and3rson/deck65/circuits/anim/1.png

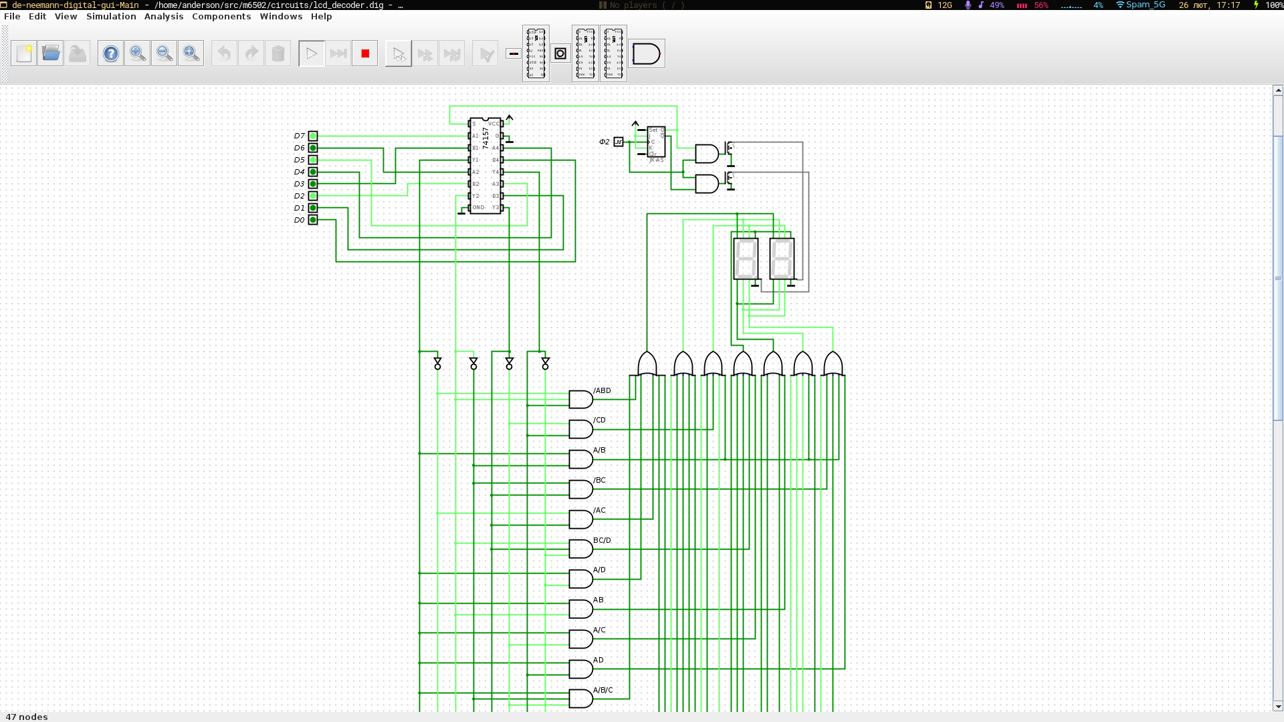
circuits/anim/1.png
