and3rson/deck65/circuits/anim/3.png

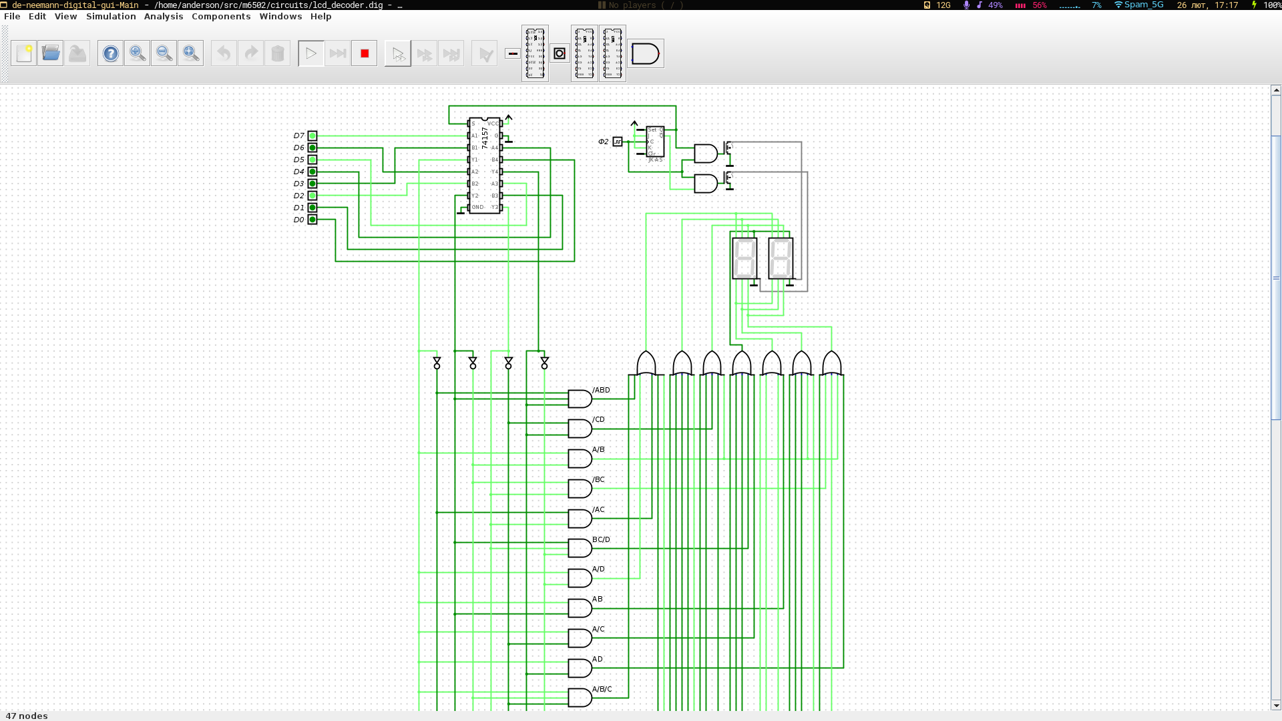
circuits/anim/3.png
