and3rson/deck65/circuits/anim/anim.gif

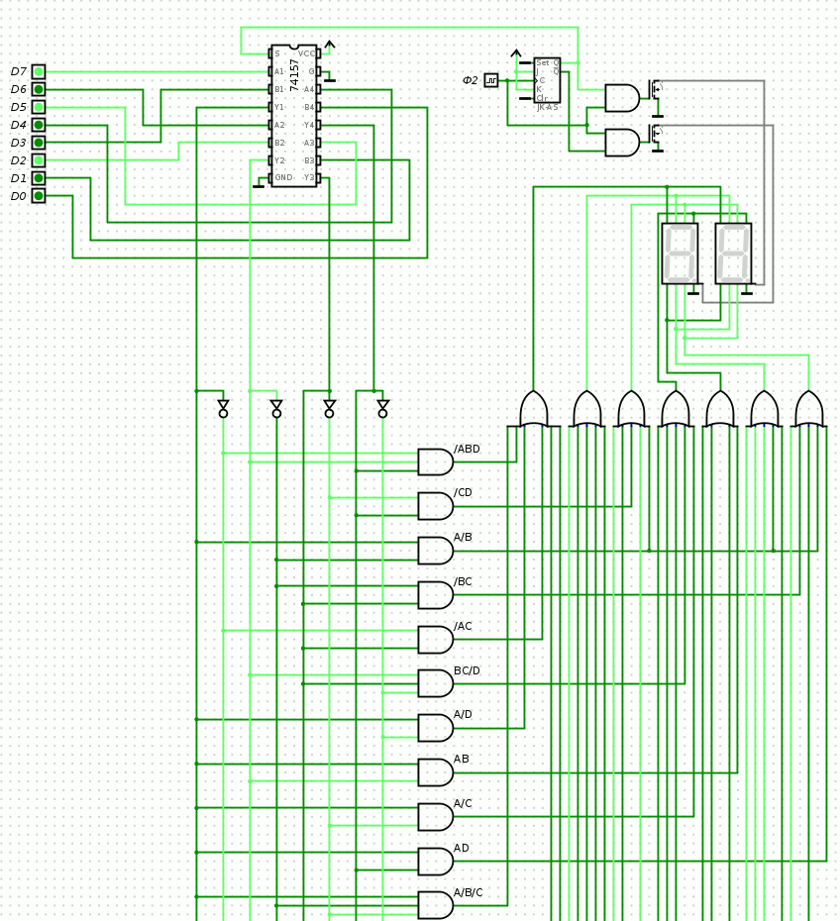
circuits/anim/anim.gif
