and3rson/deck65/circuits/sevenseg_decoder.png

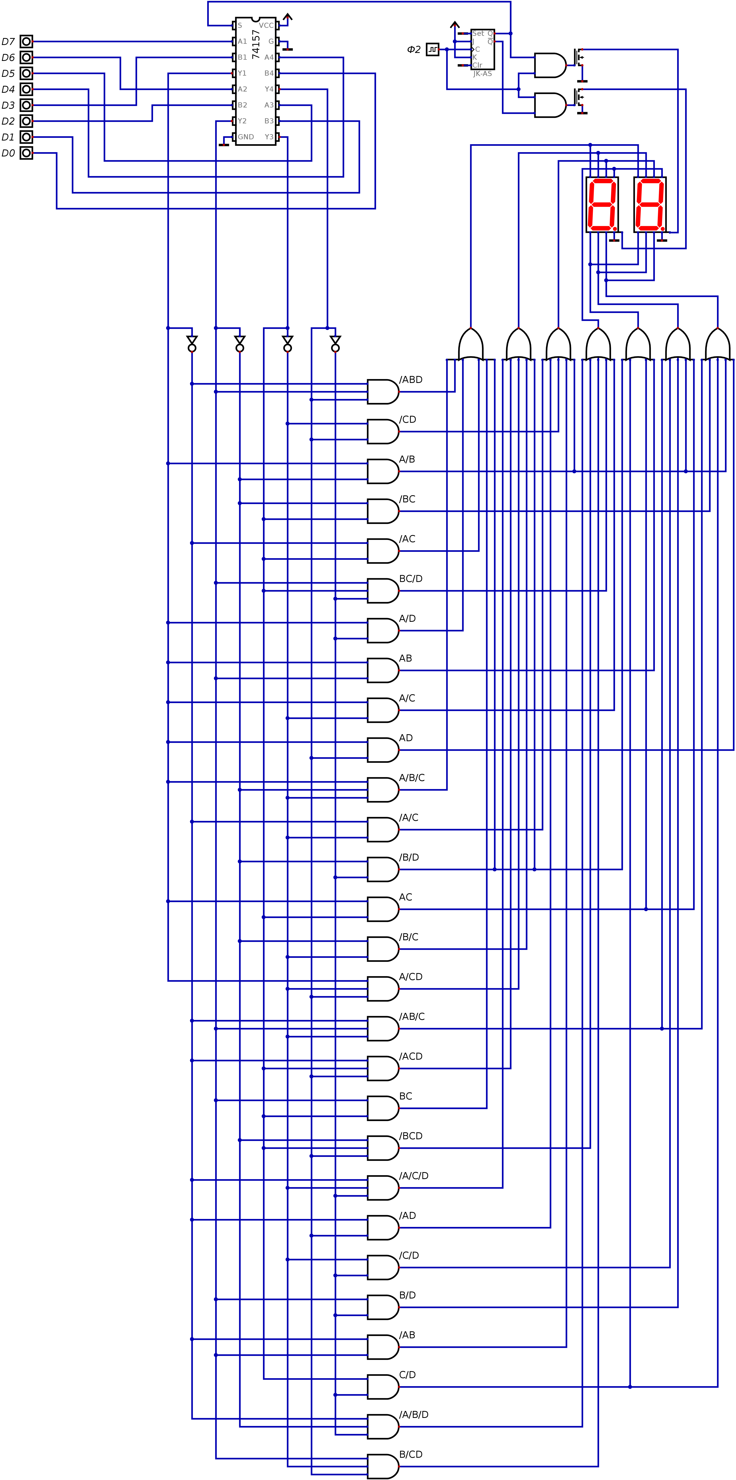
circuits/sevenseg_decoder.png
