and3rson/deck65/gal/img/1_big.png

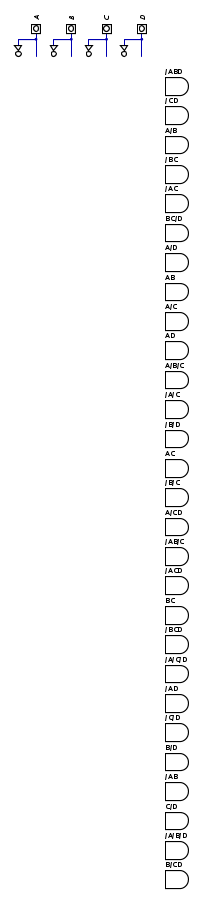
gal/img/1_big.png
