and3rson/deck65/gal/img/2_big.png

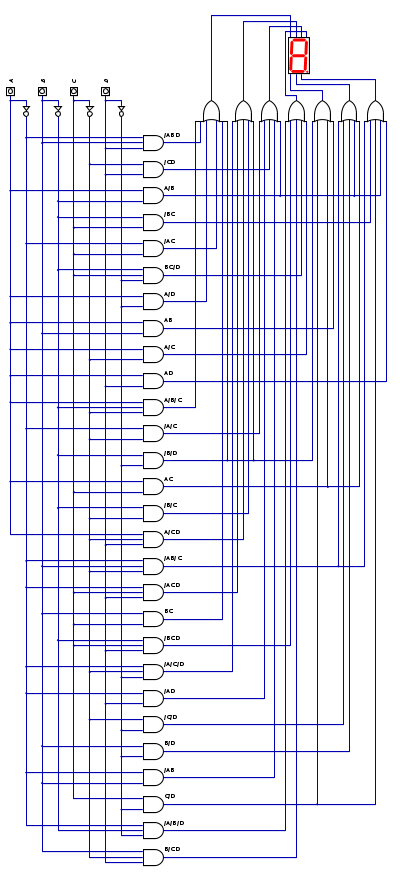
gal/img/2_big.png
