and3rson/deck65/gal/img/3_big.png

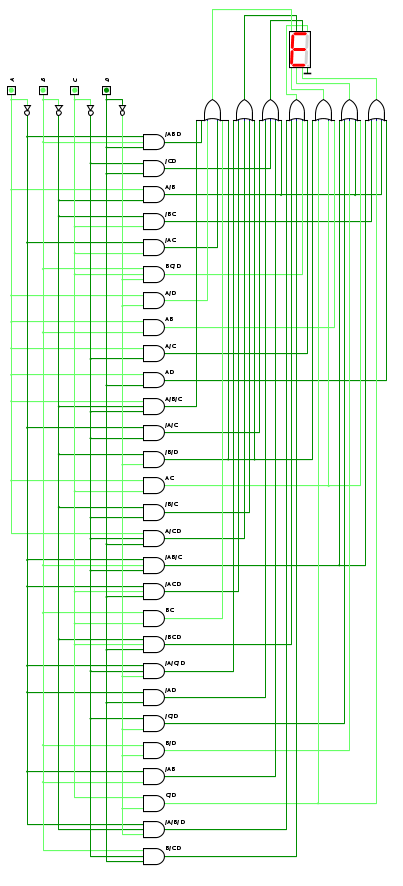
gal/img/3_big.png
