and3rson/deck65/img/24064.jpg

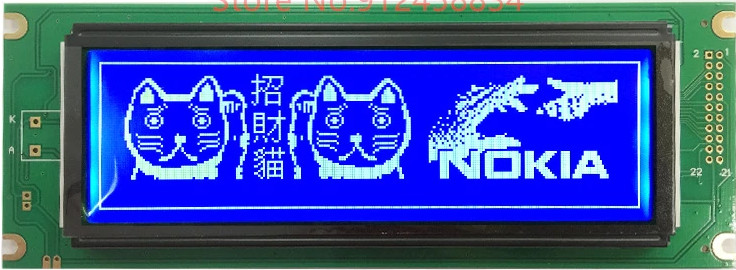
img/24064.jpg
