and3rson/deck65/img/24064_quirks.png

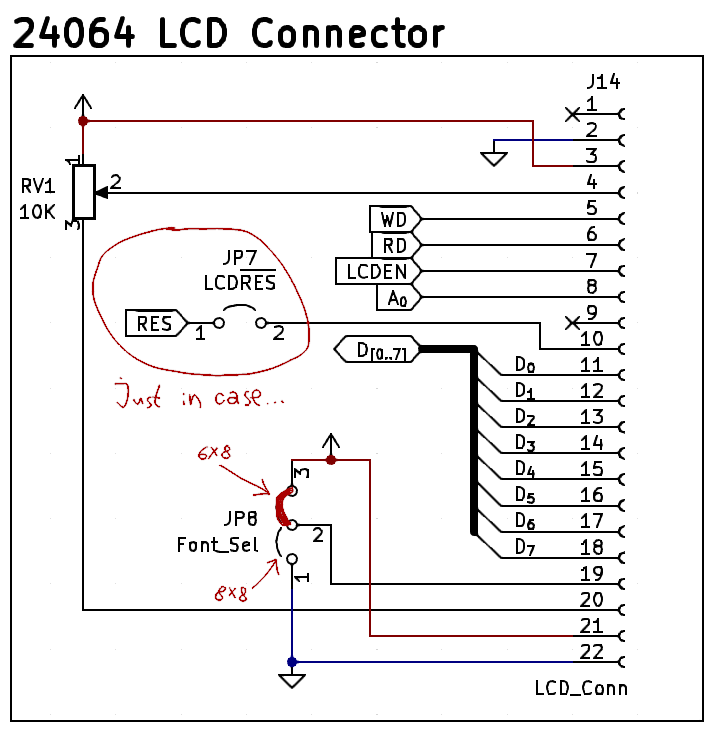
img/24064_quirks.png
