and3rson/deck65/img/cap_spread.png

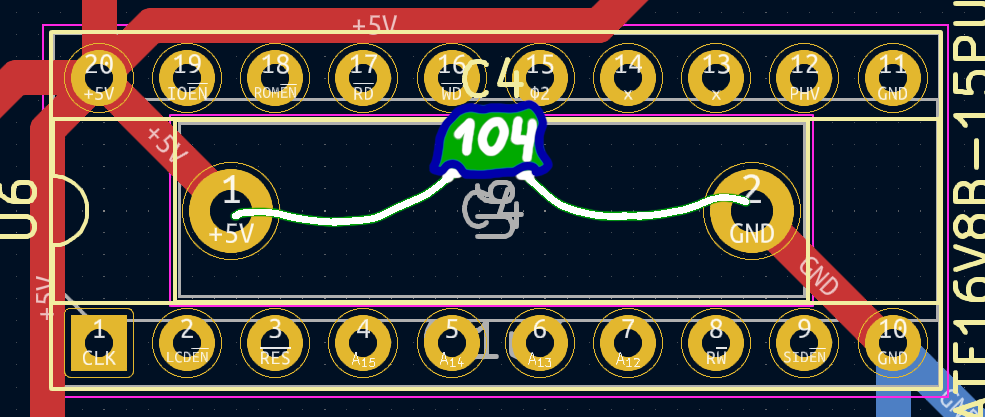
img/cap_spread.png
