and3rson/deck65/img/case_4_screws.jpg

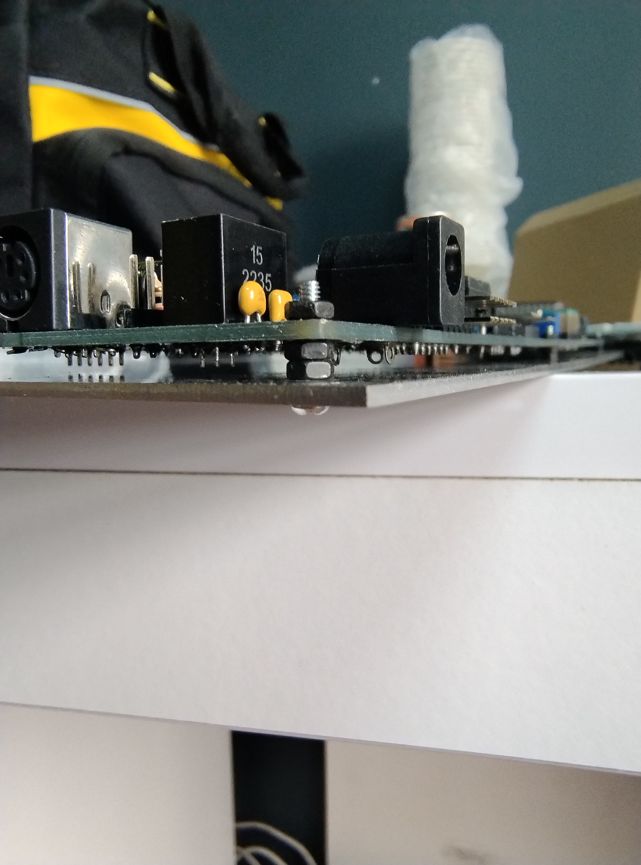
img/case_4_screws.jpg
