and3rson/deck65/img/case_8_clearance.jpg

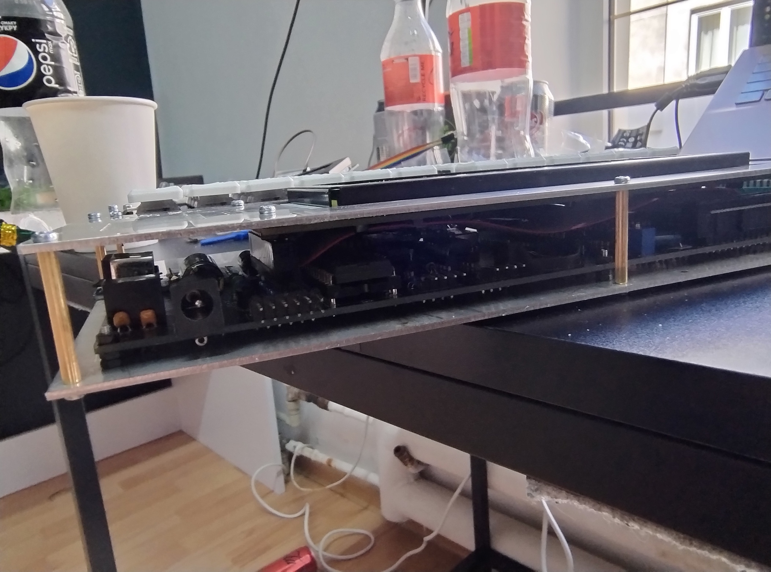
img/case_8_clearance.jpg
