and3rson/deck65/img/clock.png

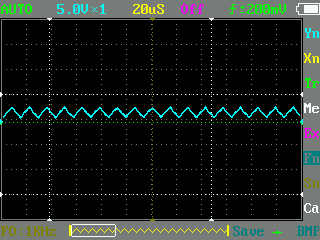
img/clock.png
