and3rson/deck65/img/composite_render_tv.jpg

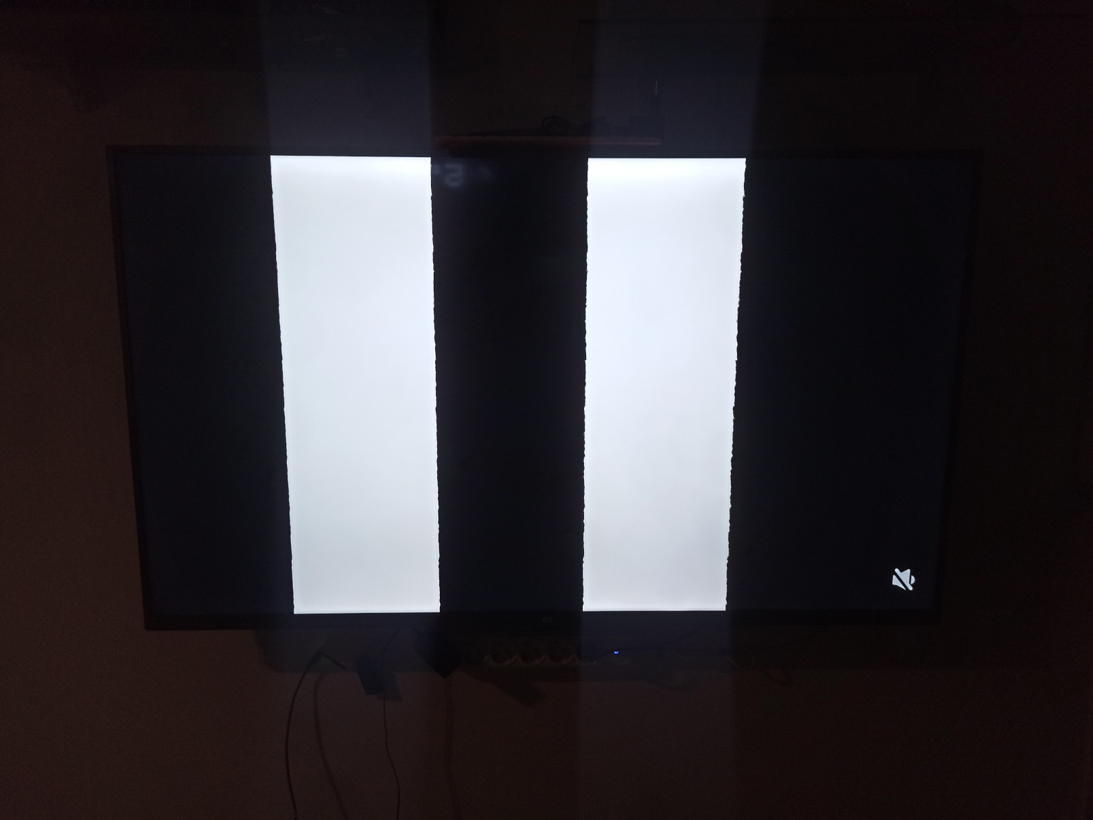
img/composite_render_tv.jpg
