and3rson/deck65/img/ds1813_reset.png

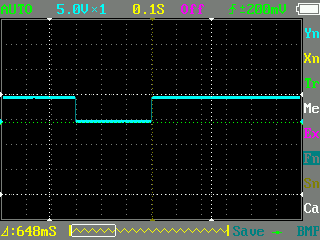
img/ds1813_reset.png
