and3rson/deck65/img/gal_slowbus_addr_rw.png

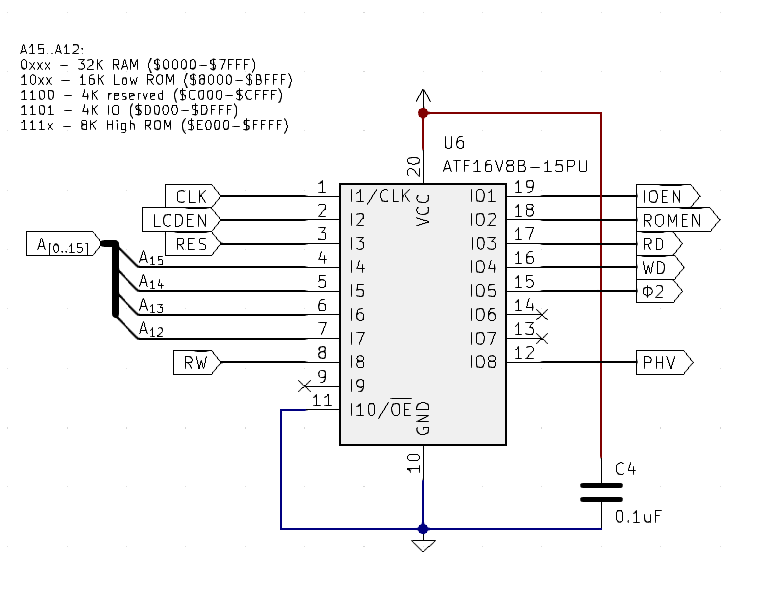
img/gal_slowbus_addr_rw.png
