and3rson/deck65/img/lcd_garbage.jpg

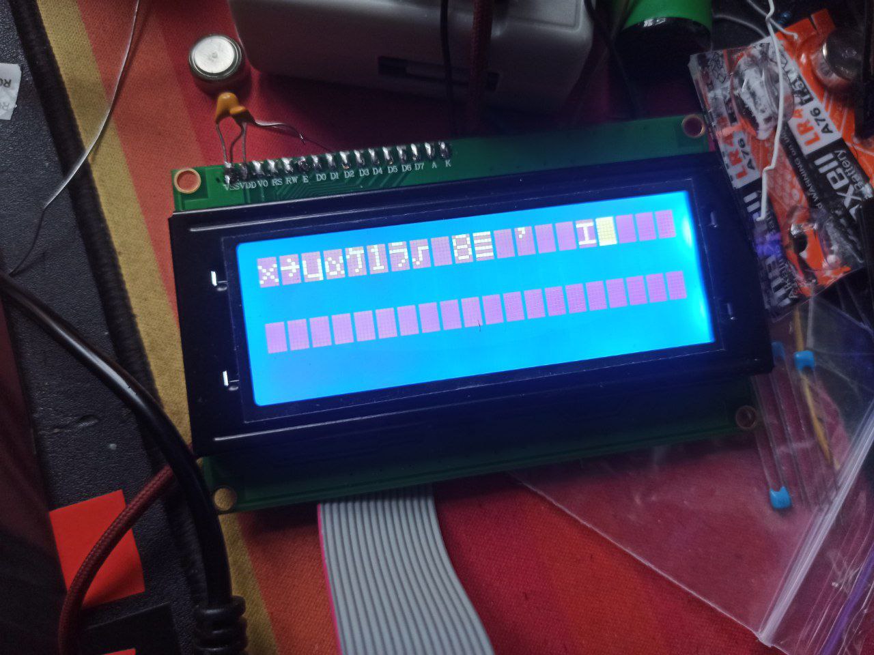
img/lcd_garbage.jpg
