and3rson/deck65/img/lcd_via_timing.png

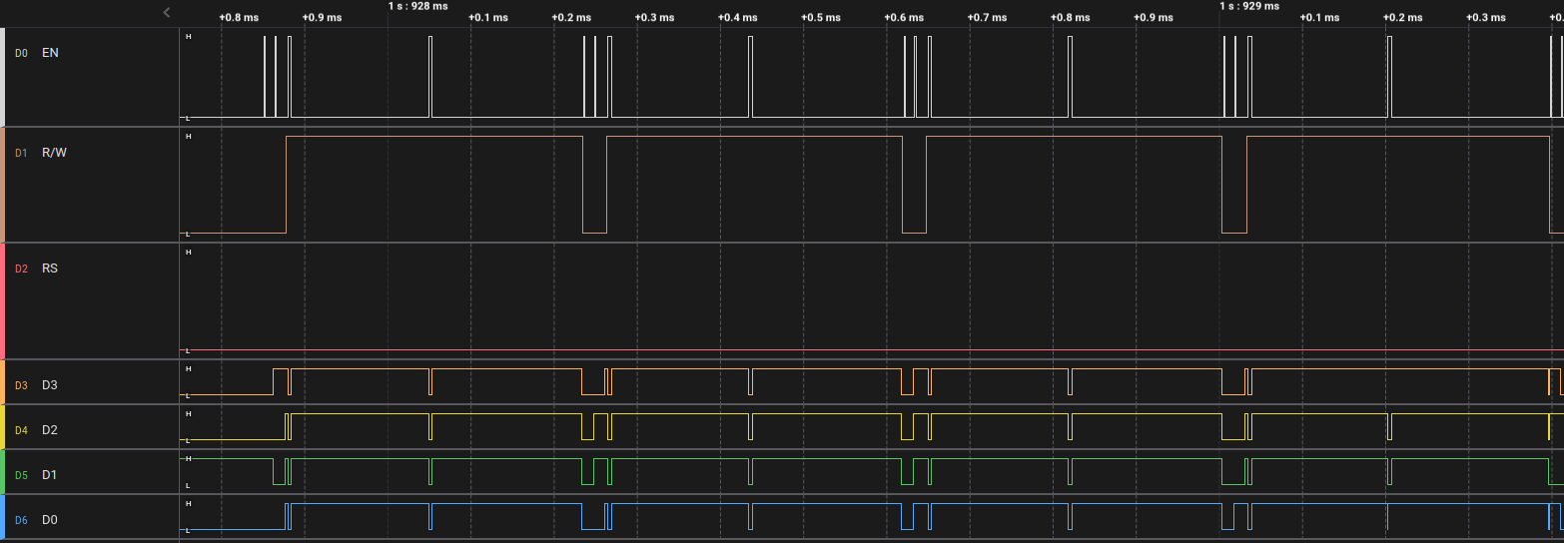
img/lcd_via_timing.png
