and3rson/deck65/img/lcd_weirdness.png

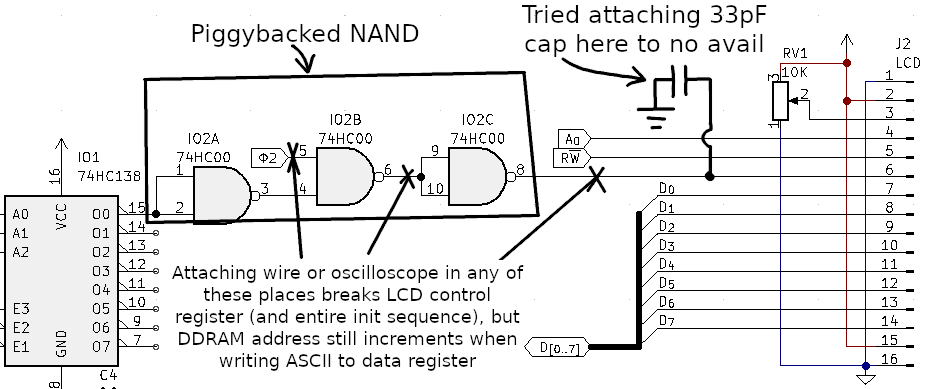
img/lcd_weirdness.png
