and3rson/deck65/img/lcden_timing2.png

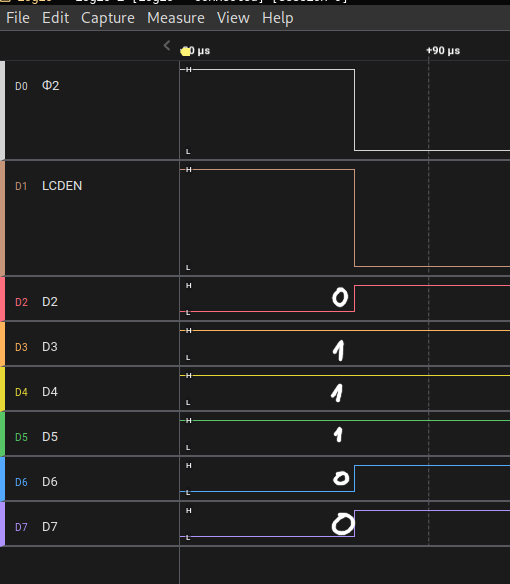
img/lcden_timing2.png
