and3rson/deck65/img/lcden_timing.png

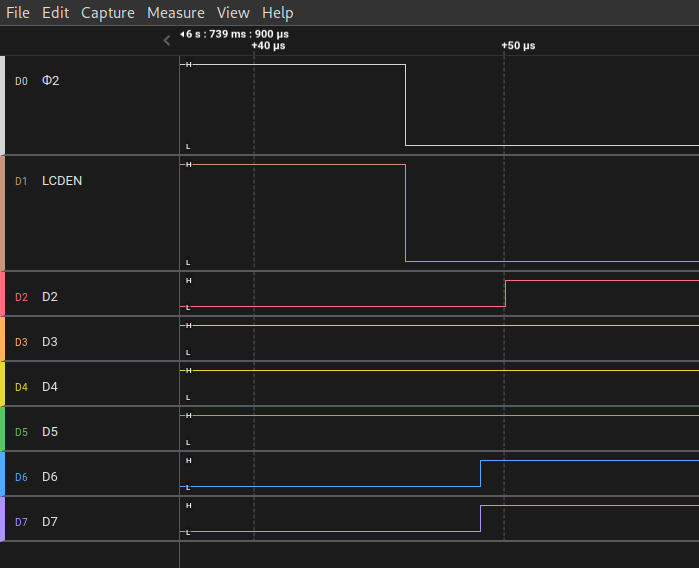
img/lcden_timing.png
