and3rson/deck65/img/mess2.jpg

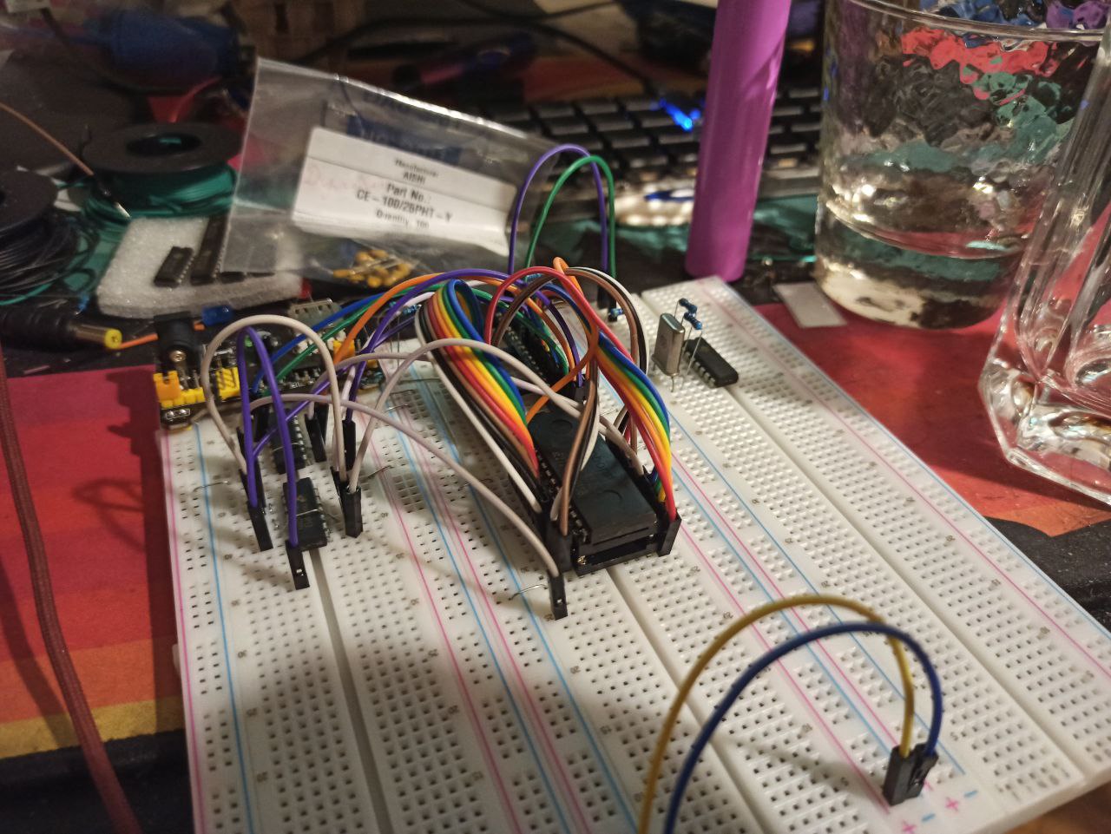
img/mess2.jpg
