and3rson/deck65/img/mess3.jpg

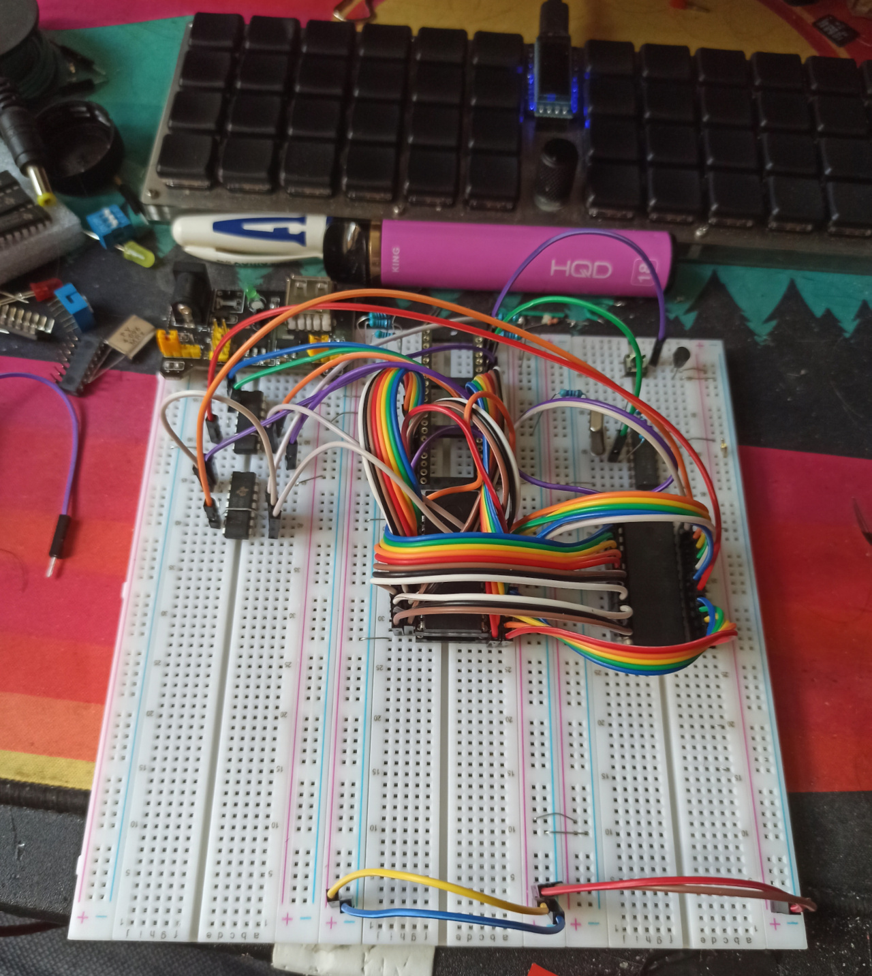
img/mess3.jpg
