and3rson/deck65/img/mess.jpg

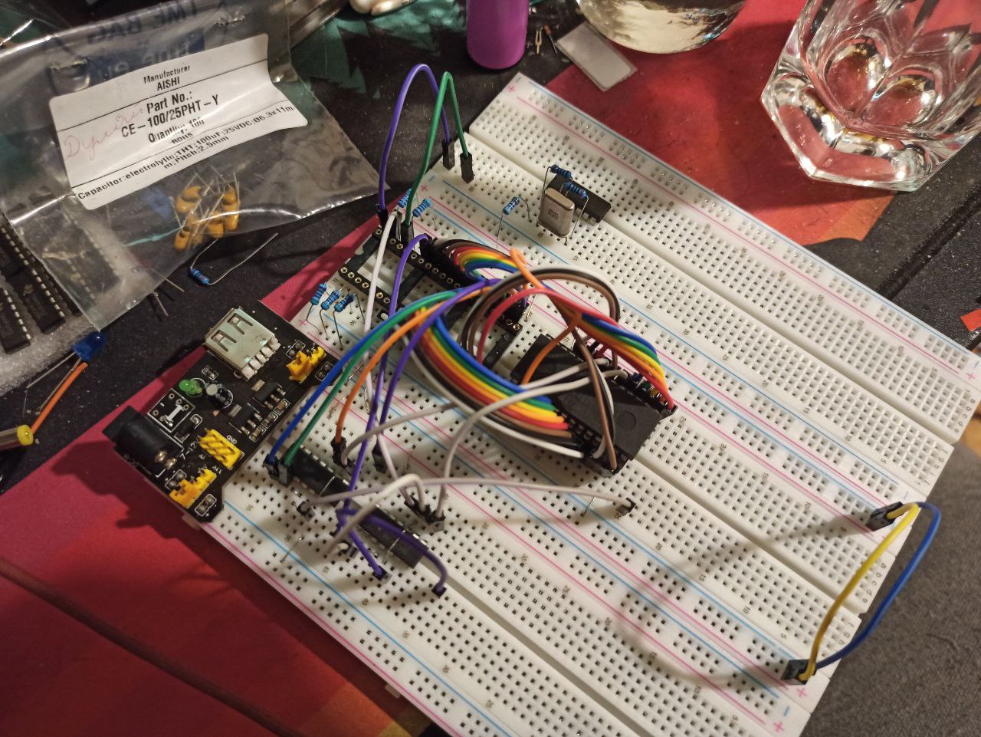
img/mess.jpg
