and3rson/deck65/img/nand_piggyback.jpg

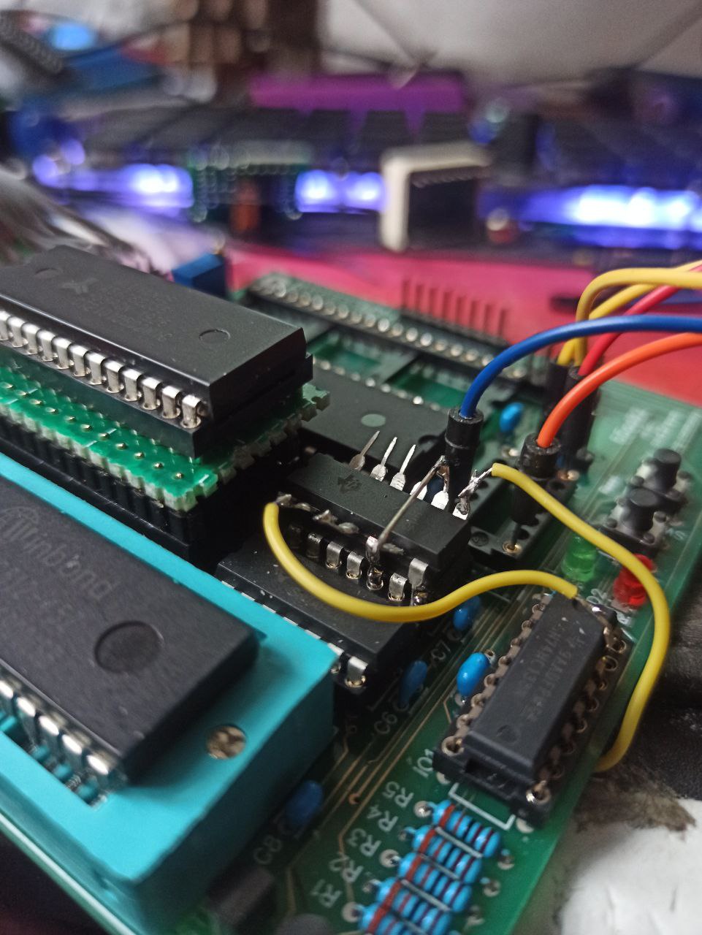
img/nand_piggyback.jpg
