and3rson/deck65/img/pal_weirdness.png

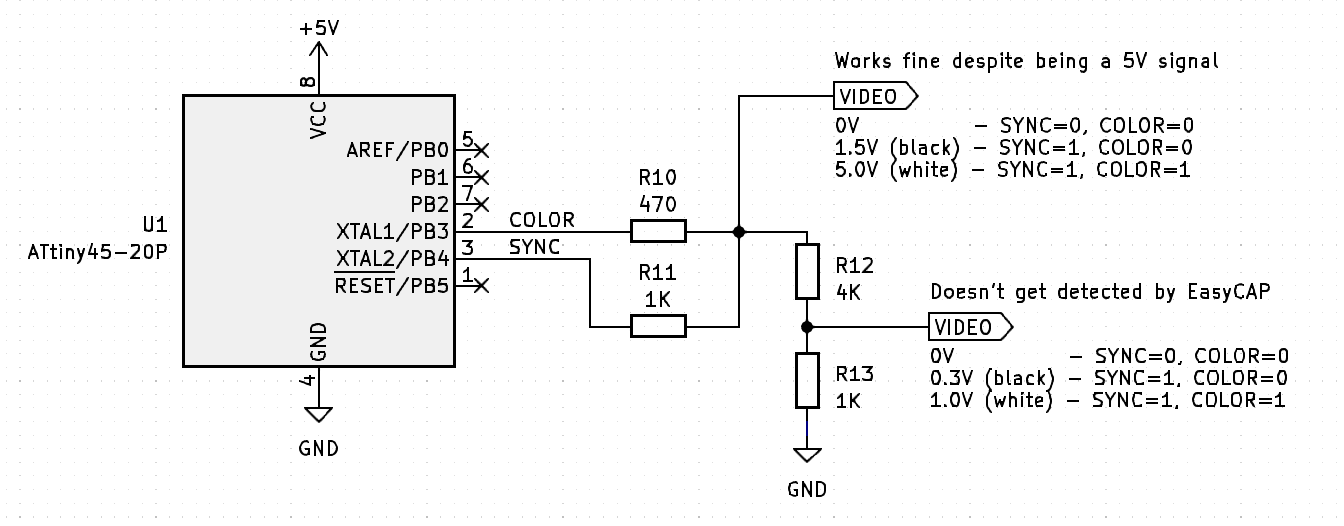
img/pal_weirdness.png
