and3rson/deck65/img/ram_banking.png

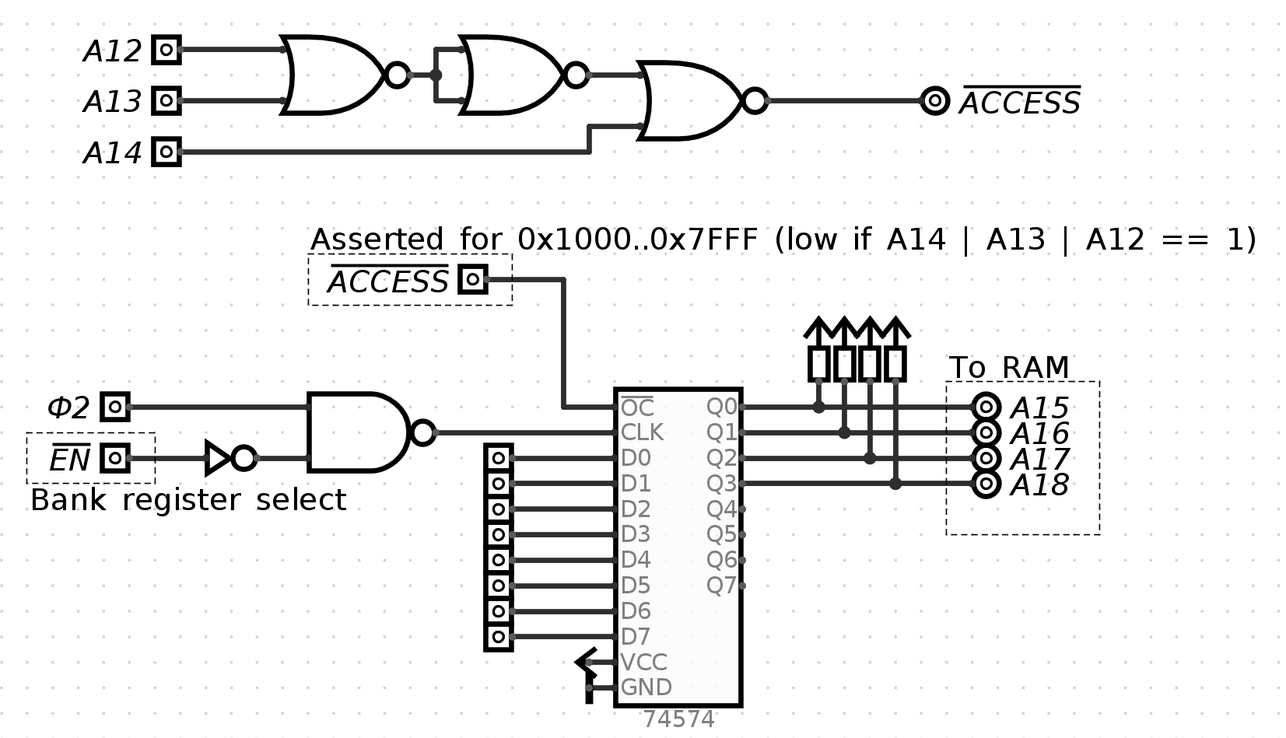
img/ram_banking.png
