and3rson/deck65/img/render.gif

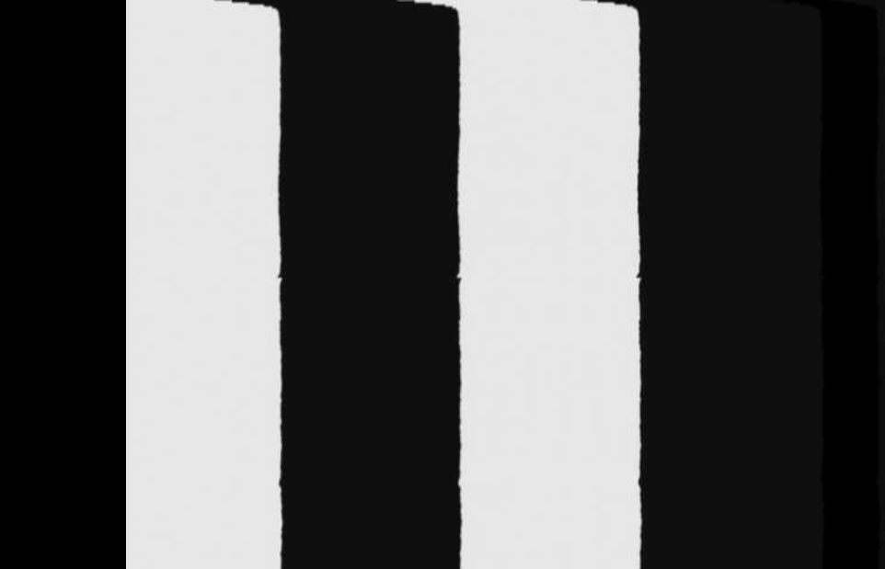
img/render.gif
