and3rson/deck65/img/rw_banking2.jpg

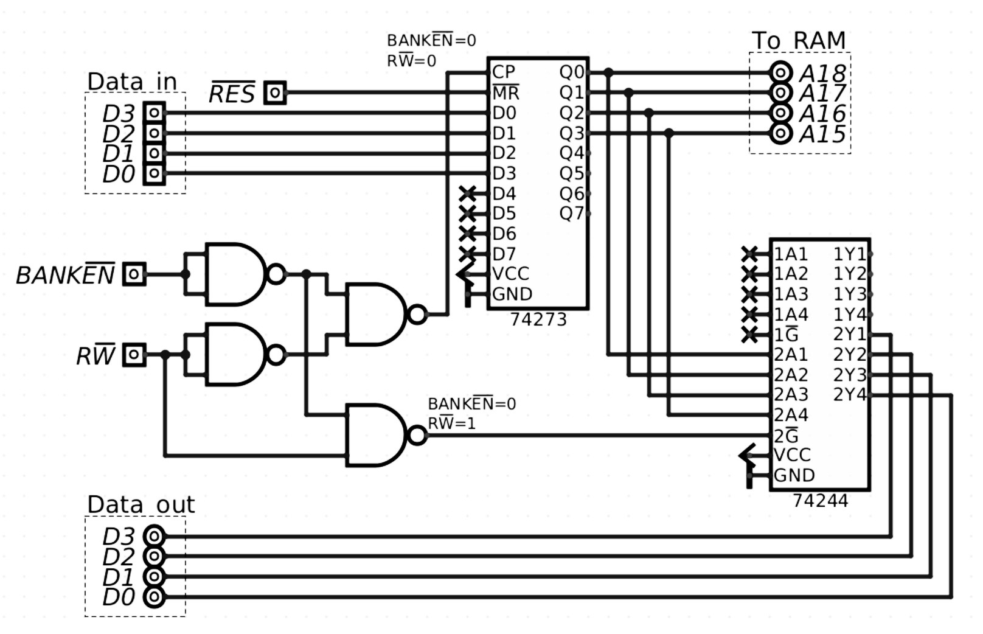
img/rw_banking2.jpg
