and3rson/deck65/img/rw_banking3.jpg

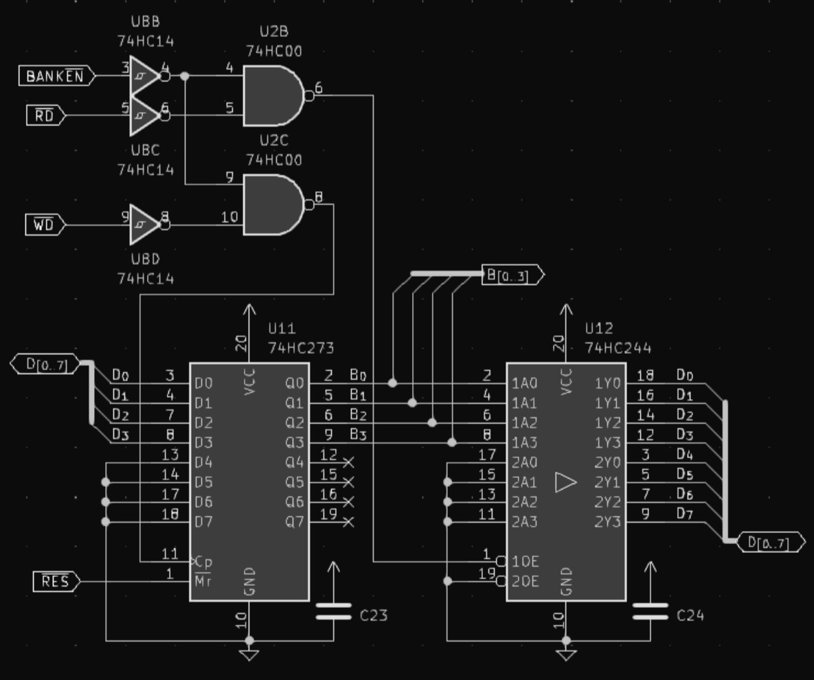
img/rw_banking3.jpg
