and3rson/deck65/img/rw_banking4.jpg

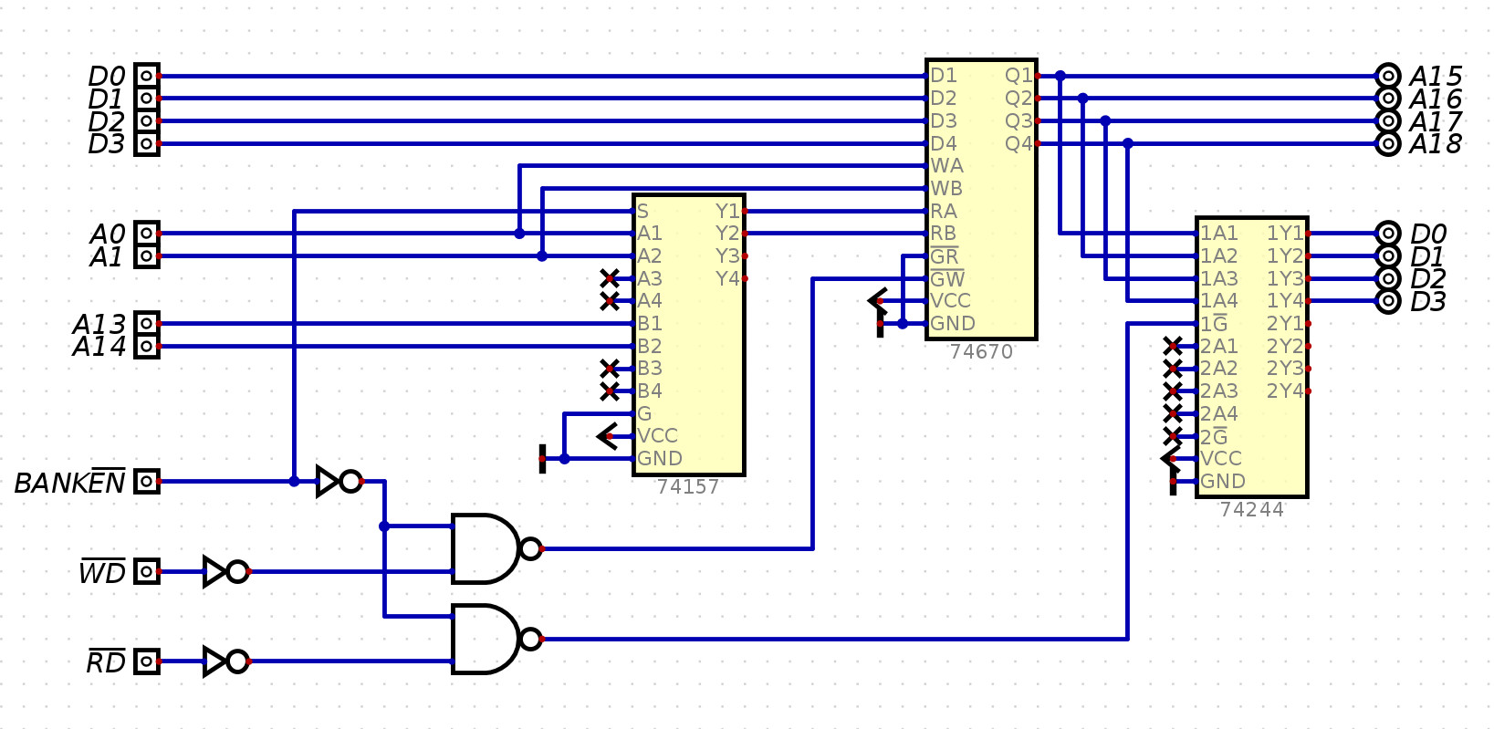
img/rw_banking4.jpg
