and3rson/deck65/img/rw_banking.jpg

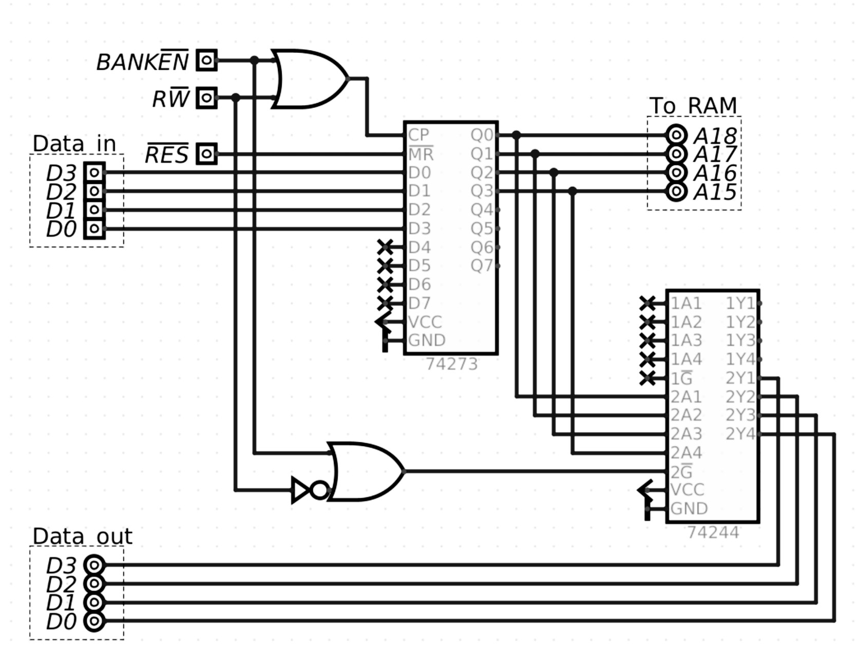
img/rw_banking.jpg
