and3rson/deck65/img/sdcard_timing.png

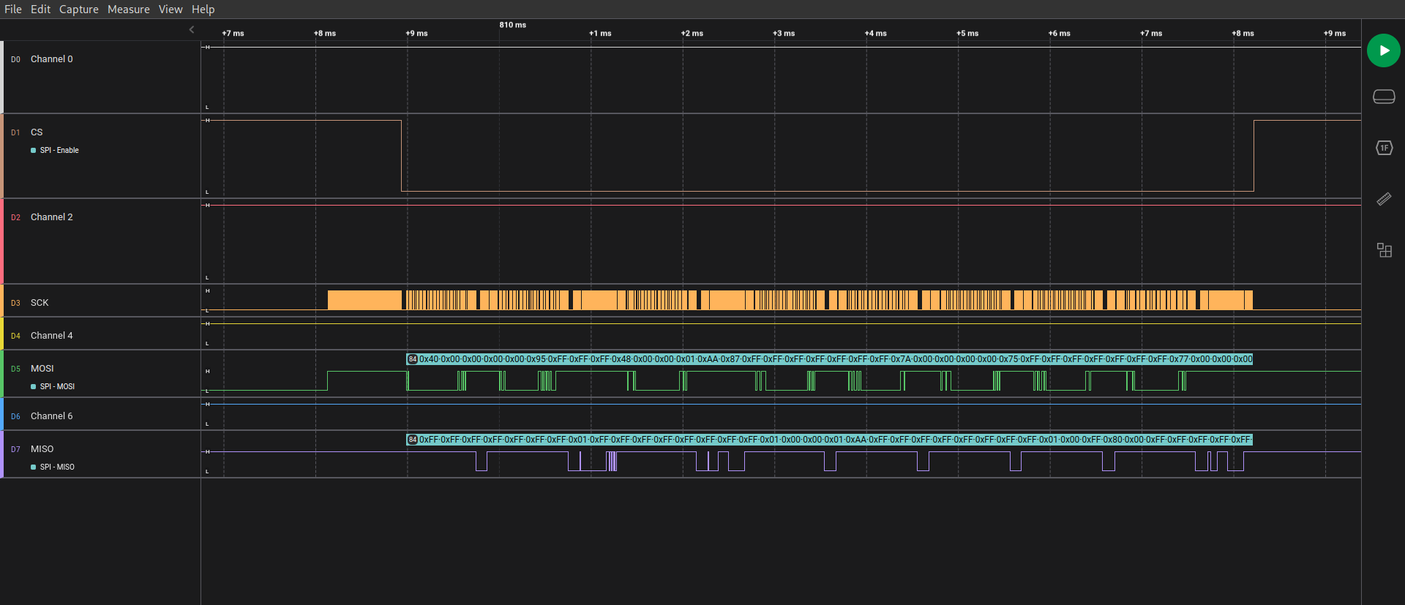
img/sdcard_timing.png
