and3rson/deck65/img/sid_sync.png

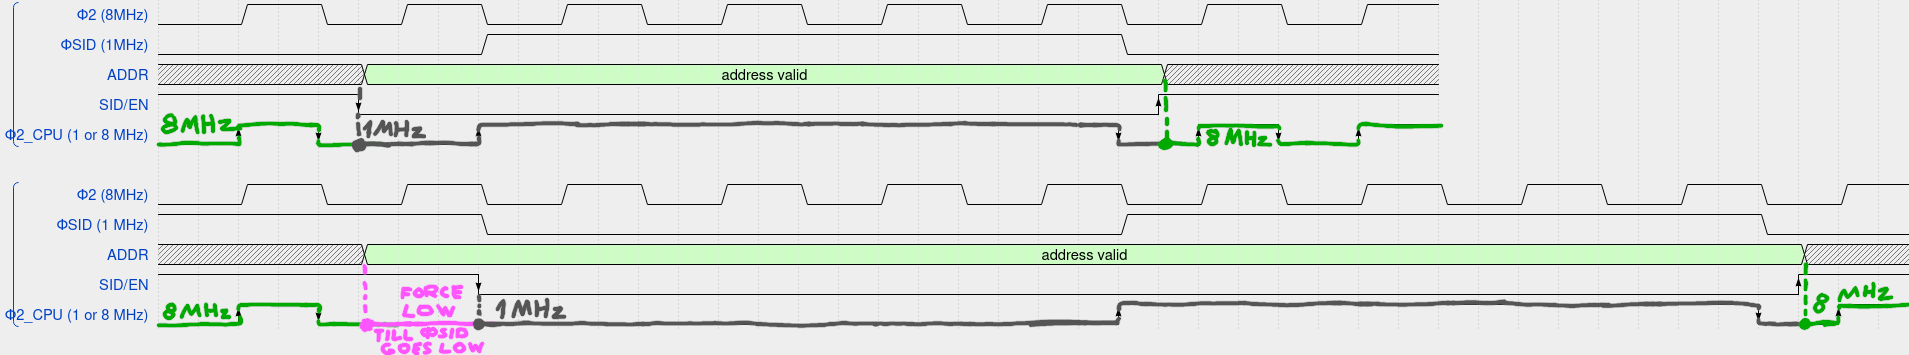
img/sid_sync.png
