and3rson/deck65/img/slowbus_diagram.png

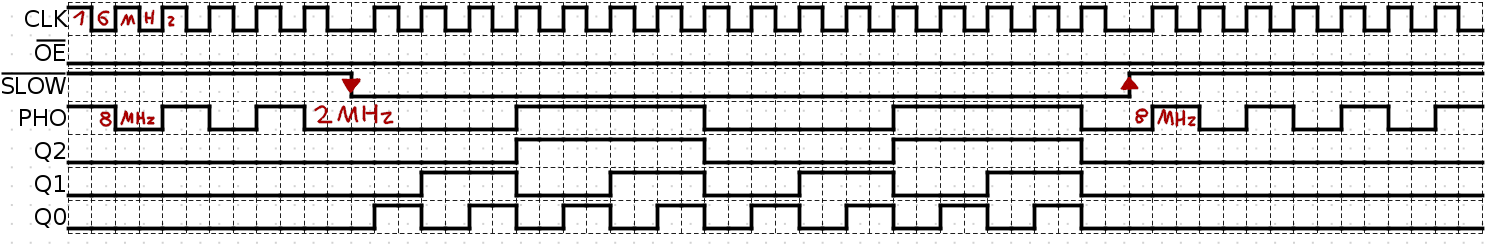
img/slowbus_diagram.png
