and3rson/deck65/img/telehack1.jpg

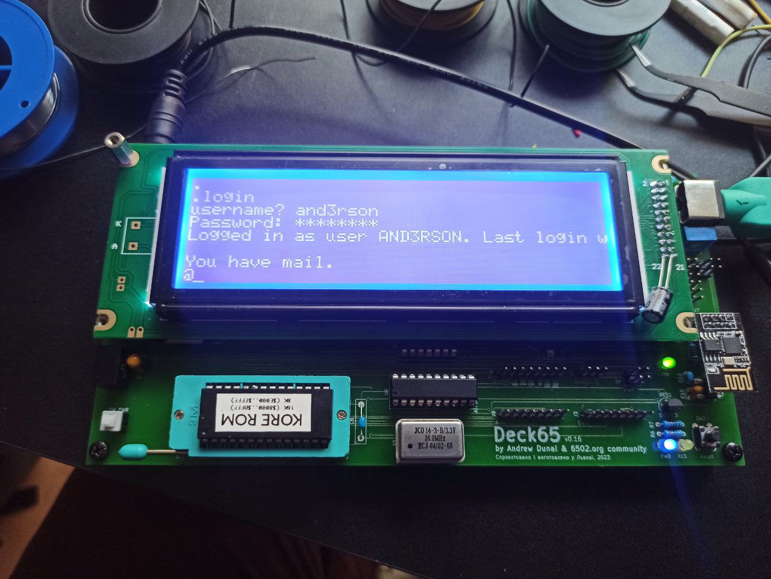
img/telehack1.jpg
