and3rson/deck65/img/telehack2.jpg

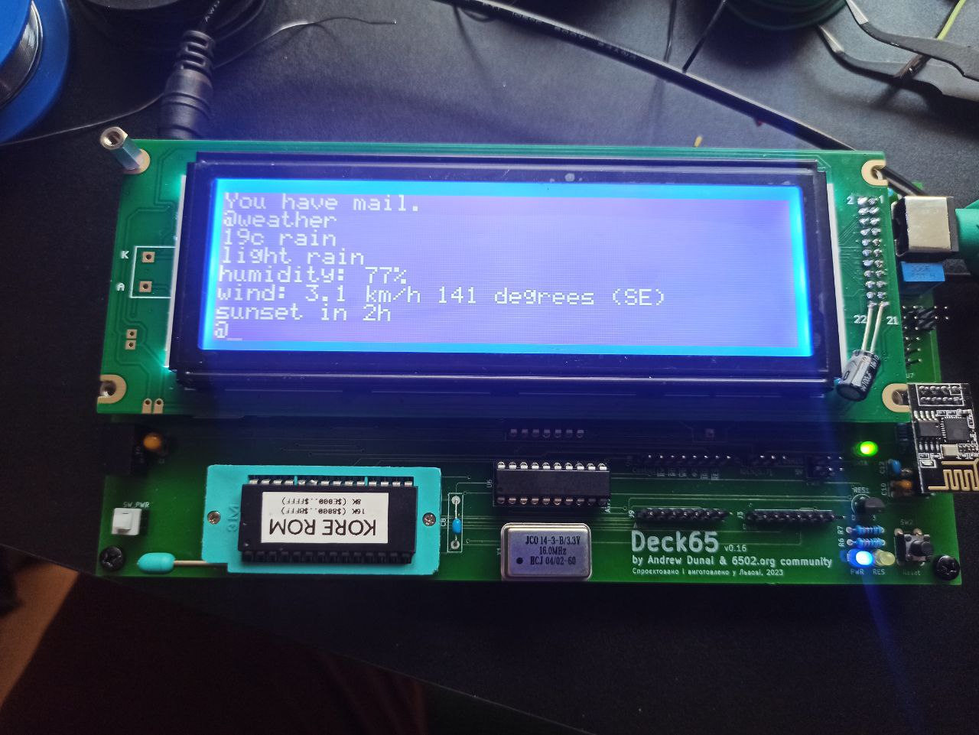
img/telehack2.jpg
