and3rson/deck65/img/telehack3.jpg

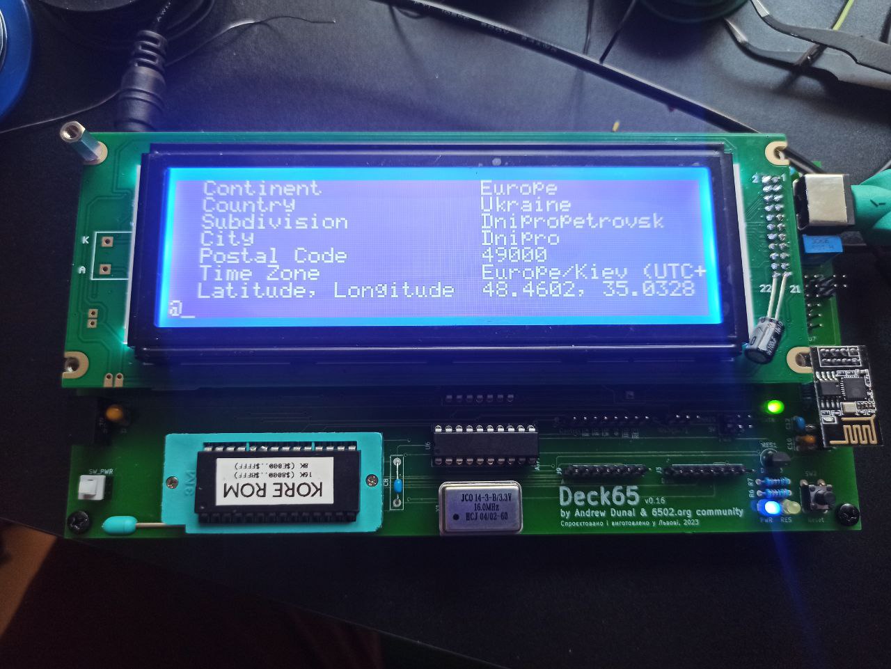
img/telehack3.jpg
