and3rson/deck65/img/underclock.png

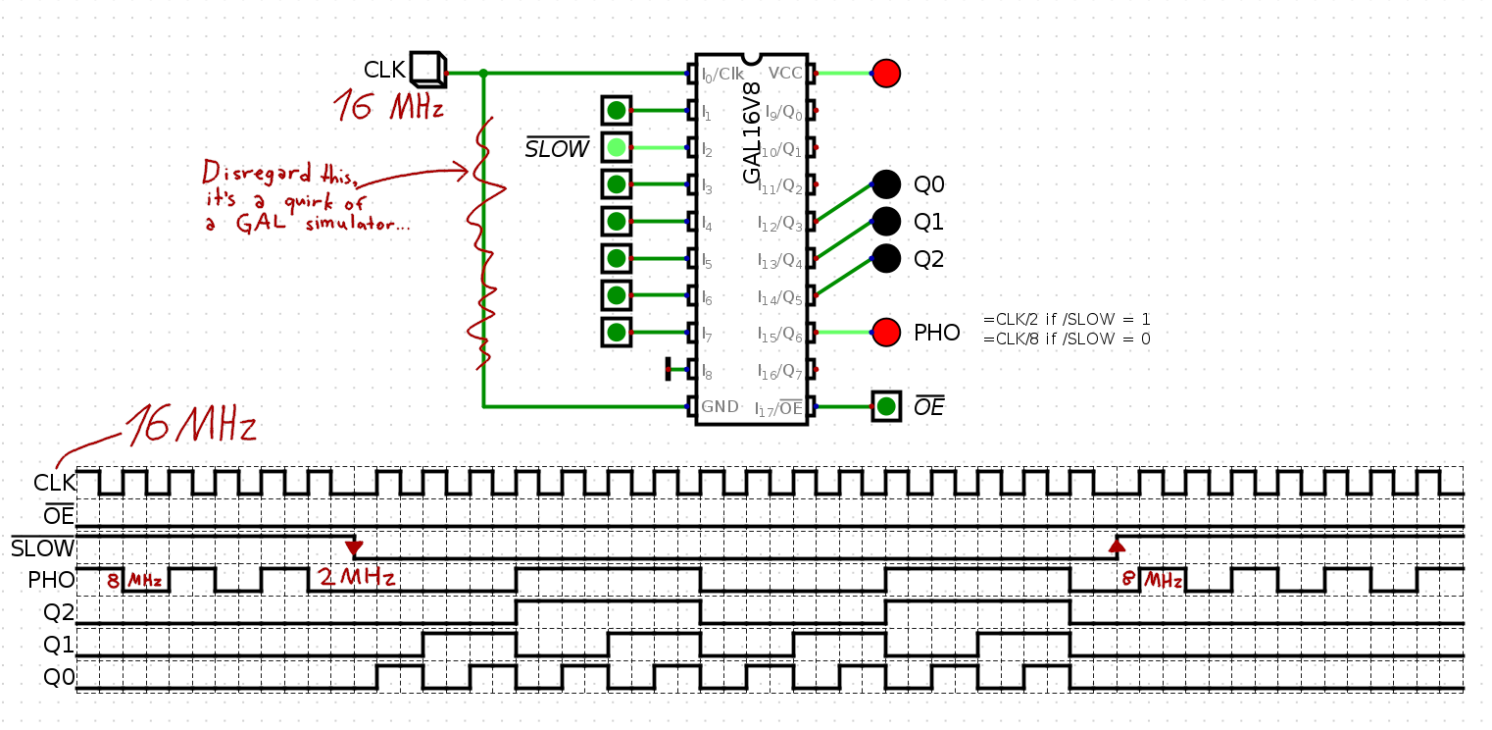
img/underclock.png
