and3rson/deck65/img/v01.png

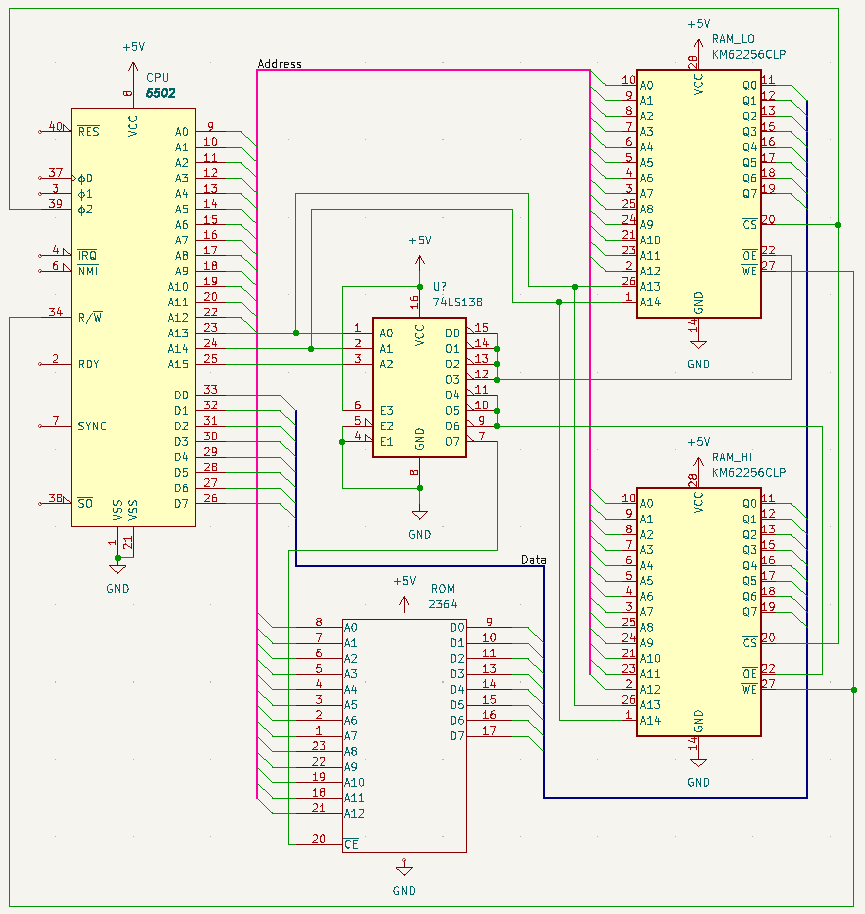
img/v01.png
