and3rson/deck65/img/v02.png

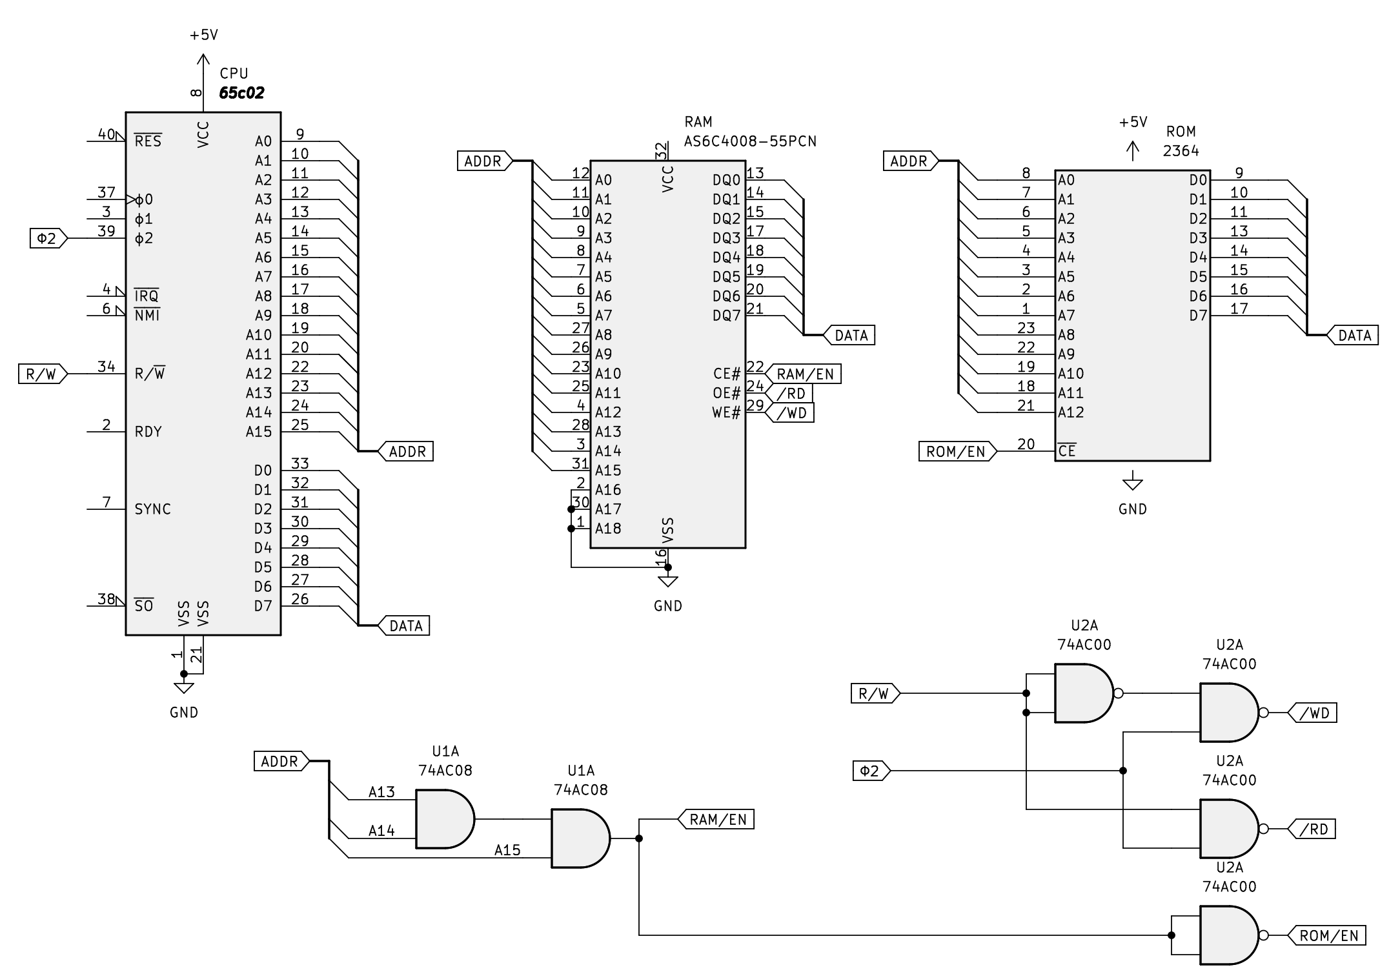
img/v02.png
