and3rson/deck65/img/v2_0.jpg

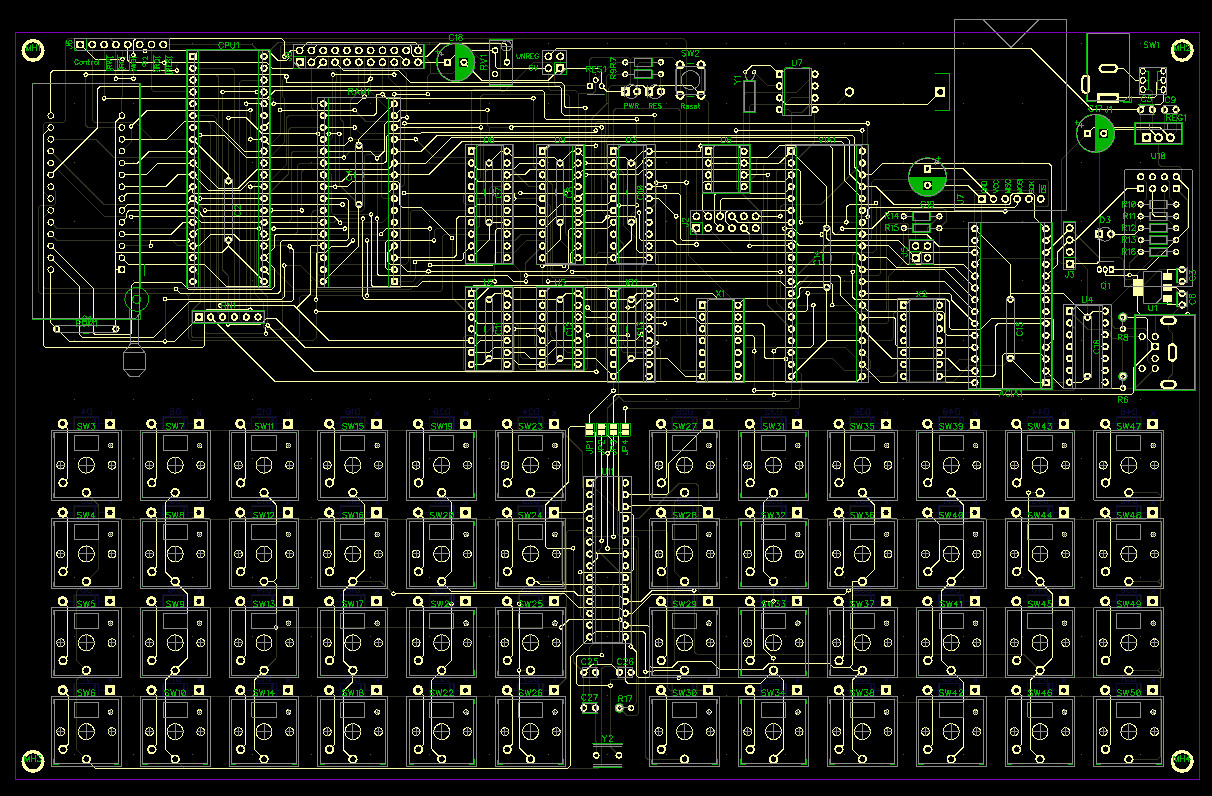
img/v2_0.jpg
