and3rson/deck65/img/v2_0.png

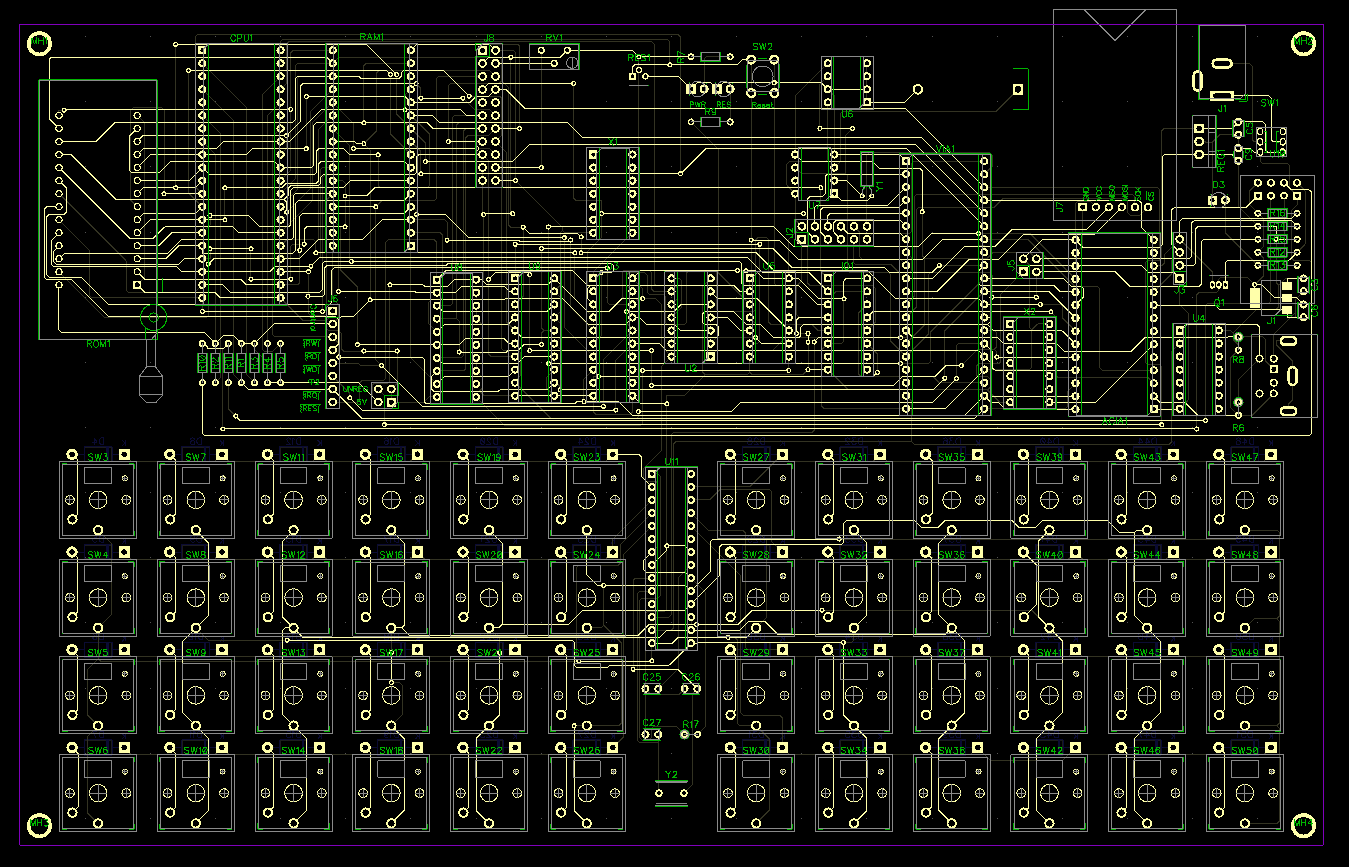
img/v2_0.png
