and3rson/deck65/img/v2_0_3d.jpg

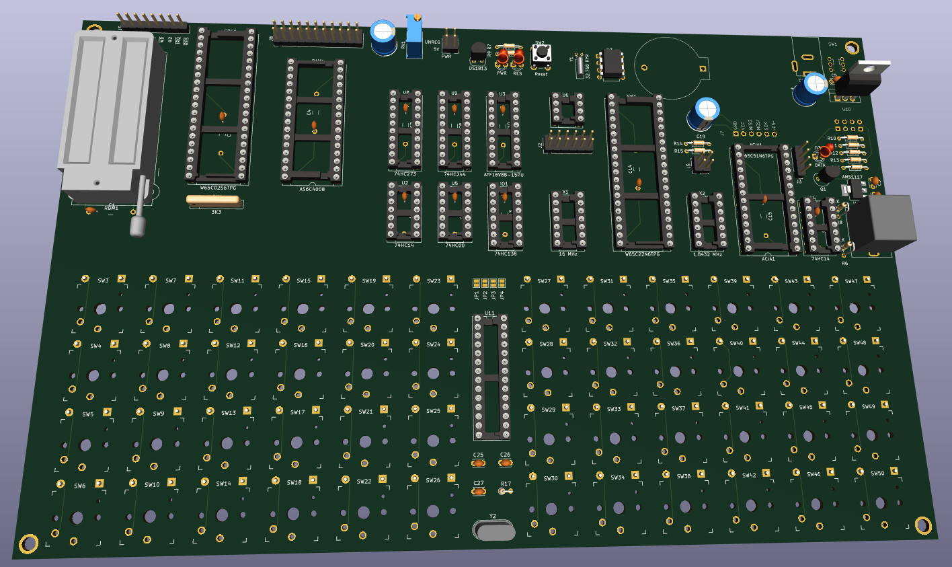
img/v2_0_3d.jpg
