and3rson/deck65/img/v2_0_banking_610.jpg

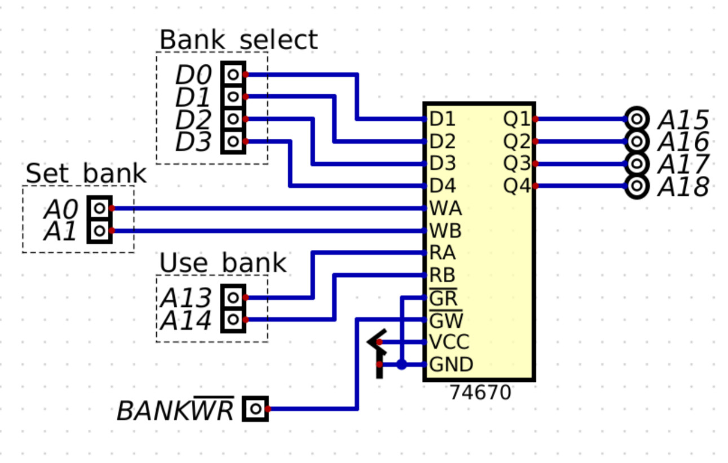
img/v2_0_banking_610.jpg
