and3rson/deck65/img/v2_0_banking_mistake.jpg

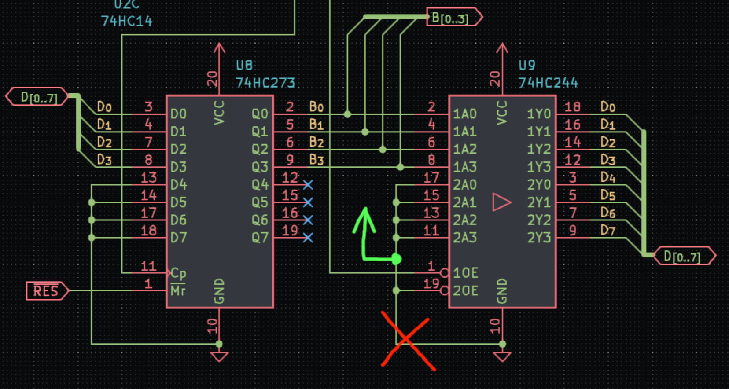
img/v2_0_banking_mistake.jpg
