and3rson/deck65/img/v2_0_case_bottom.png

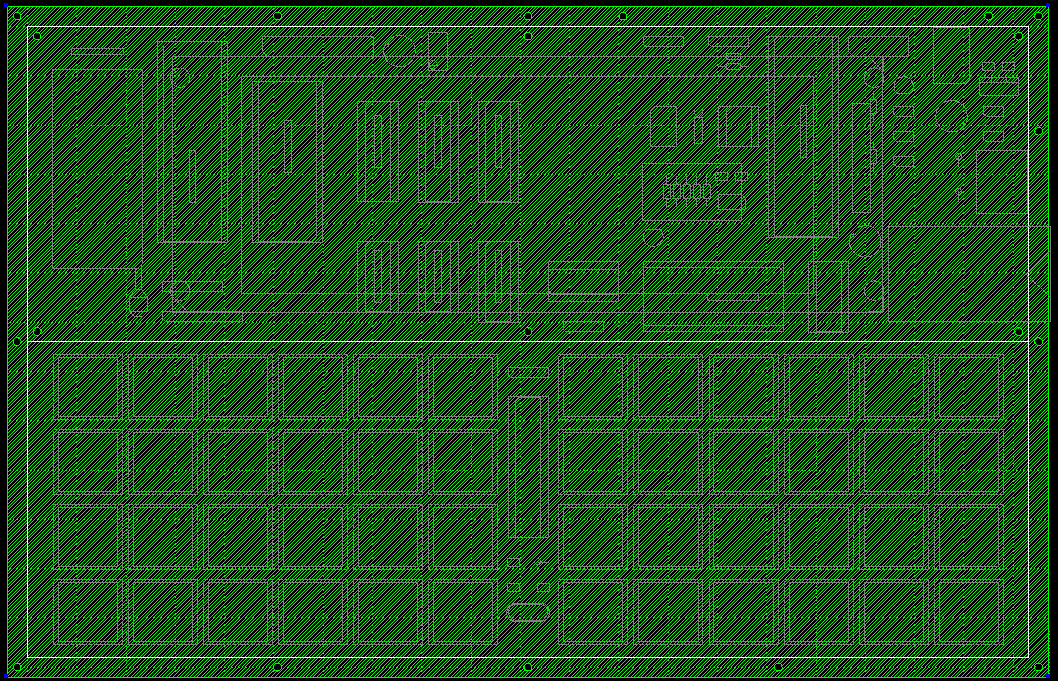
img/v2_0_case_bottom.png
