and3rson/deck65/img/v2_0_case_middle.png

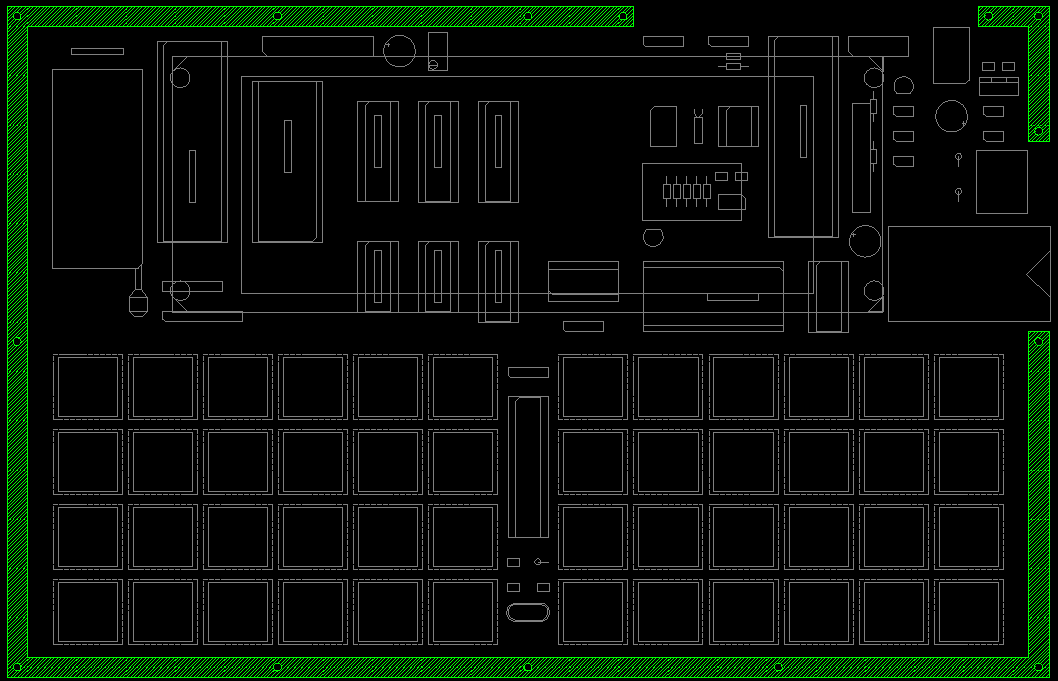
img/v2_0_case_middle.png
