and3rson/deck65/img/v2_0_pcb1.jpg

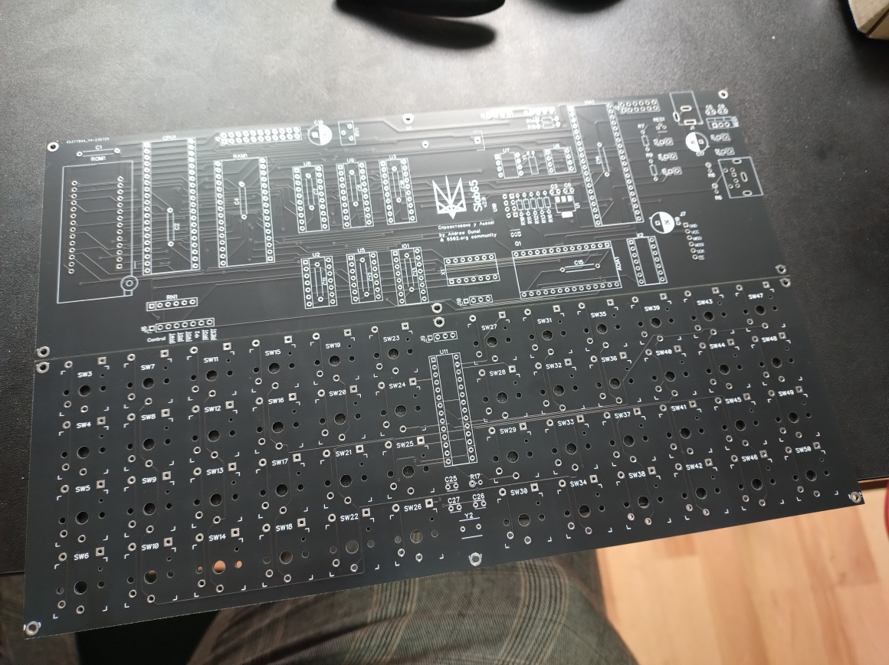
img/v2_0_pcb1.jpg
