and3rson/deck65/img/v2_0_renders/editor.jpg

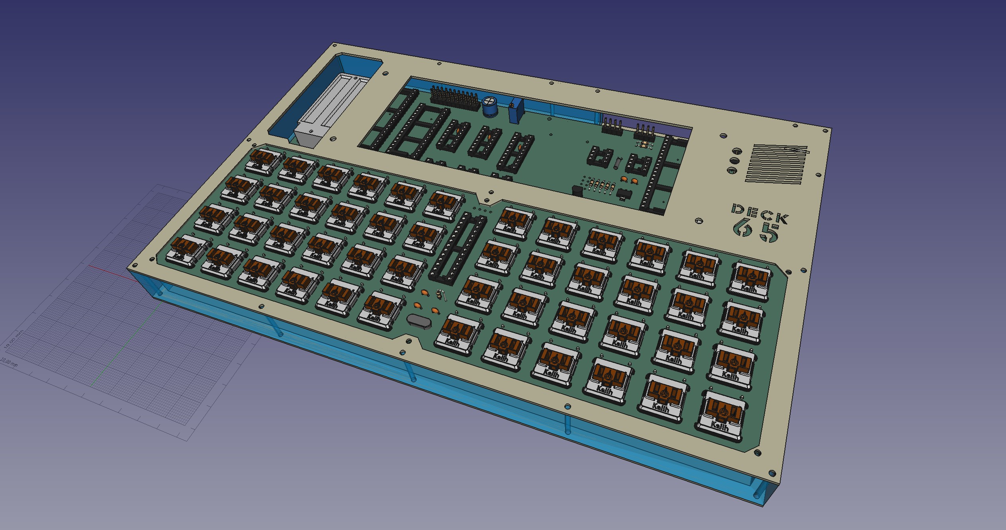
img/v2_0_renders/editor.jpg
