and3rson/deck65/img/v2_0_renders/freecad.jpg

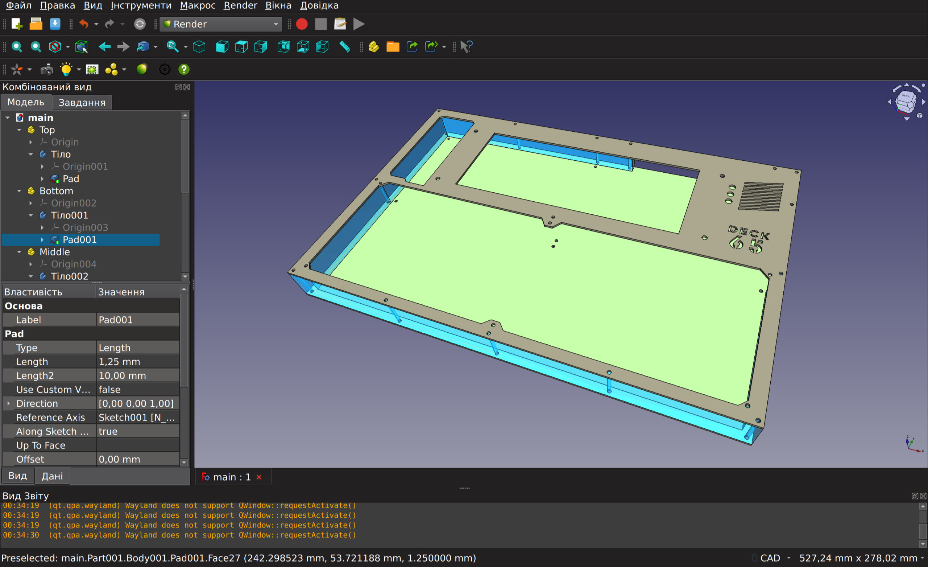
img/v2_0_renders/freecad.jpg
