and3rson/deck65/img/v2_0_renders/render.jpg

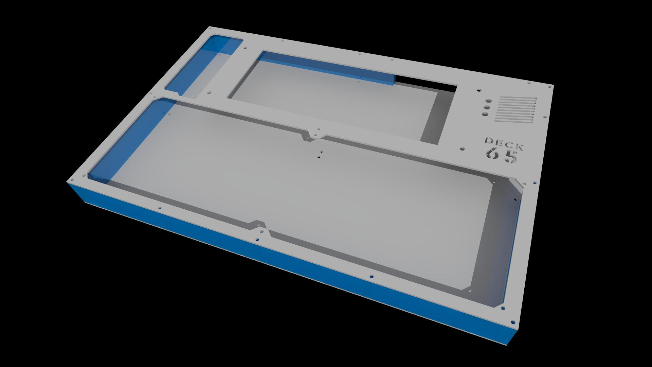
img/v2_0_renders/render.jpg
