and3rson/deck65/img/v2_0_renders/render_angle_pcb.jpg

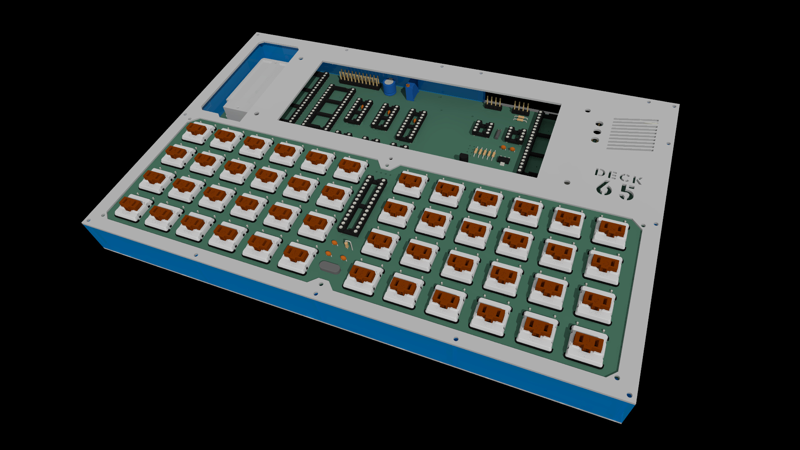
img/v2_0_renders/render_angle_pcb.jpg
