and3rson/deck65/img/v2_0_renders/render_top_pcb.jpg

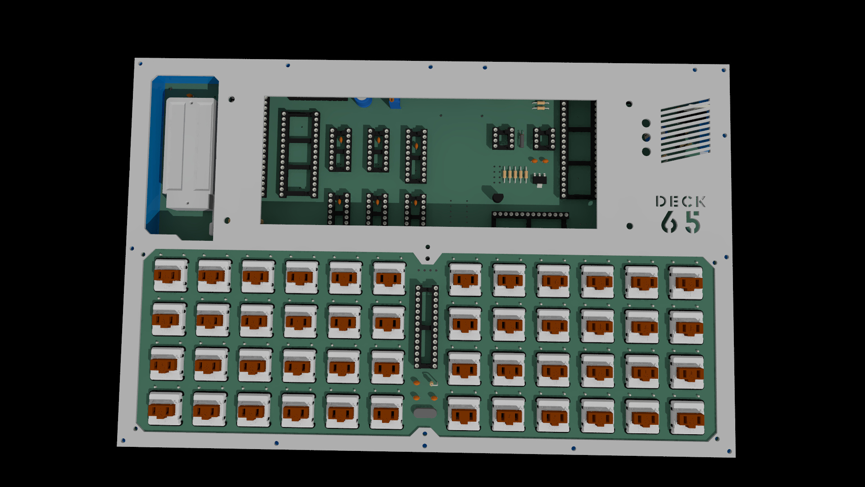
img/v2_0_renders/render_top_pcb.jpg
