and3rson/deck65/img/v2_0_renders/top.png

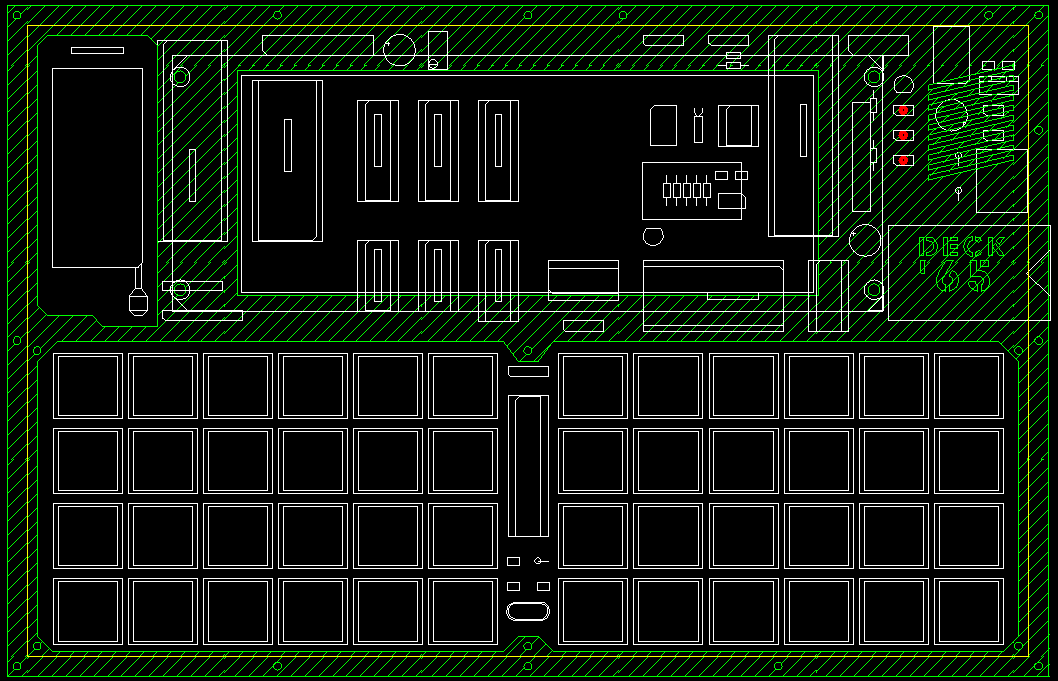
img/v2_0_renders/top.png
