and3rson/deck65/img/v2_0_top_view.jpg

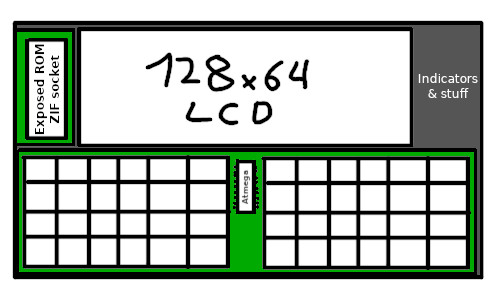
img/v2_0_top_view.jpg
