and3rson/deck65/img/v2_0_unrouted.jpg

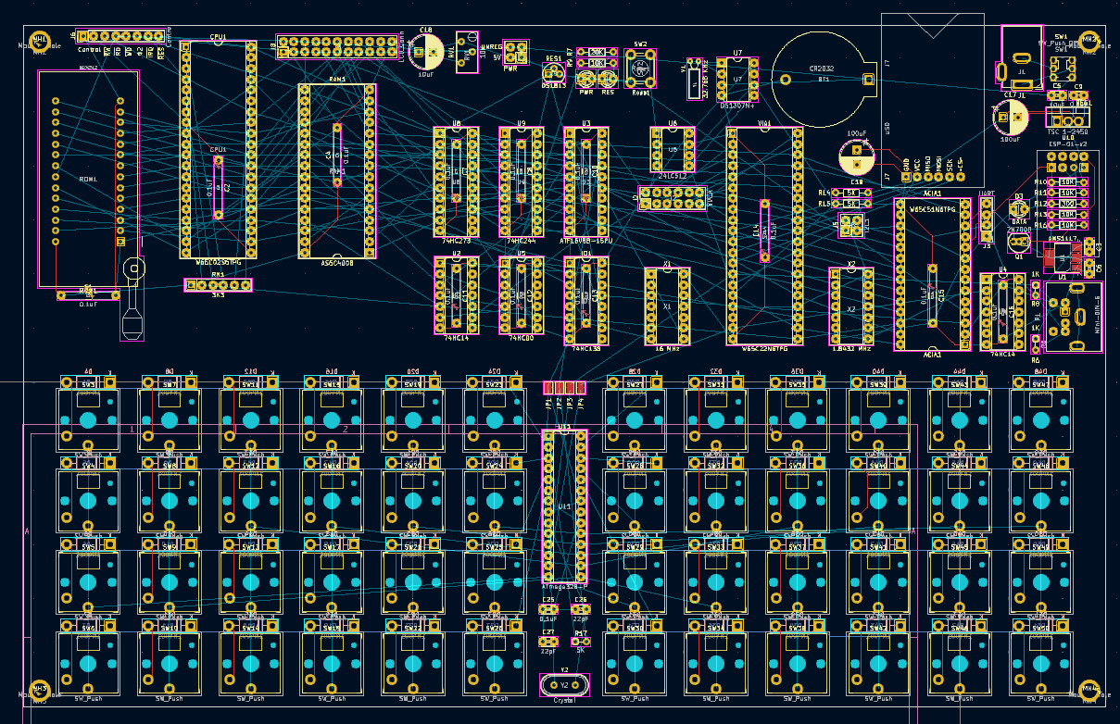
img/v2_0_unrouted.jpg
