and3rson/deck65/img/v03.png

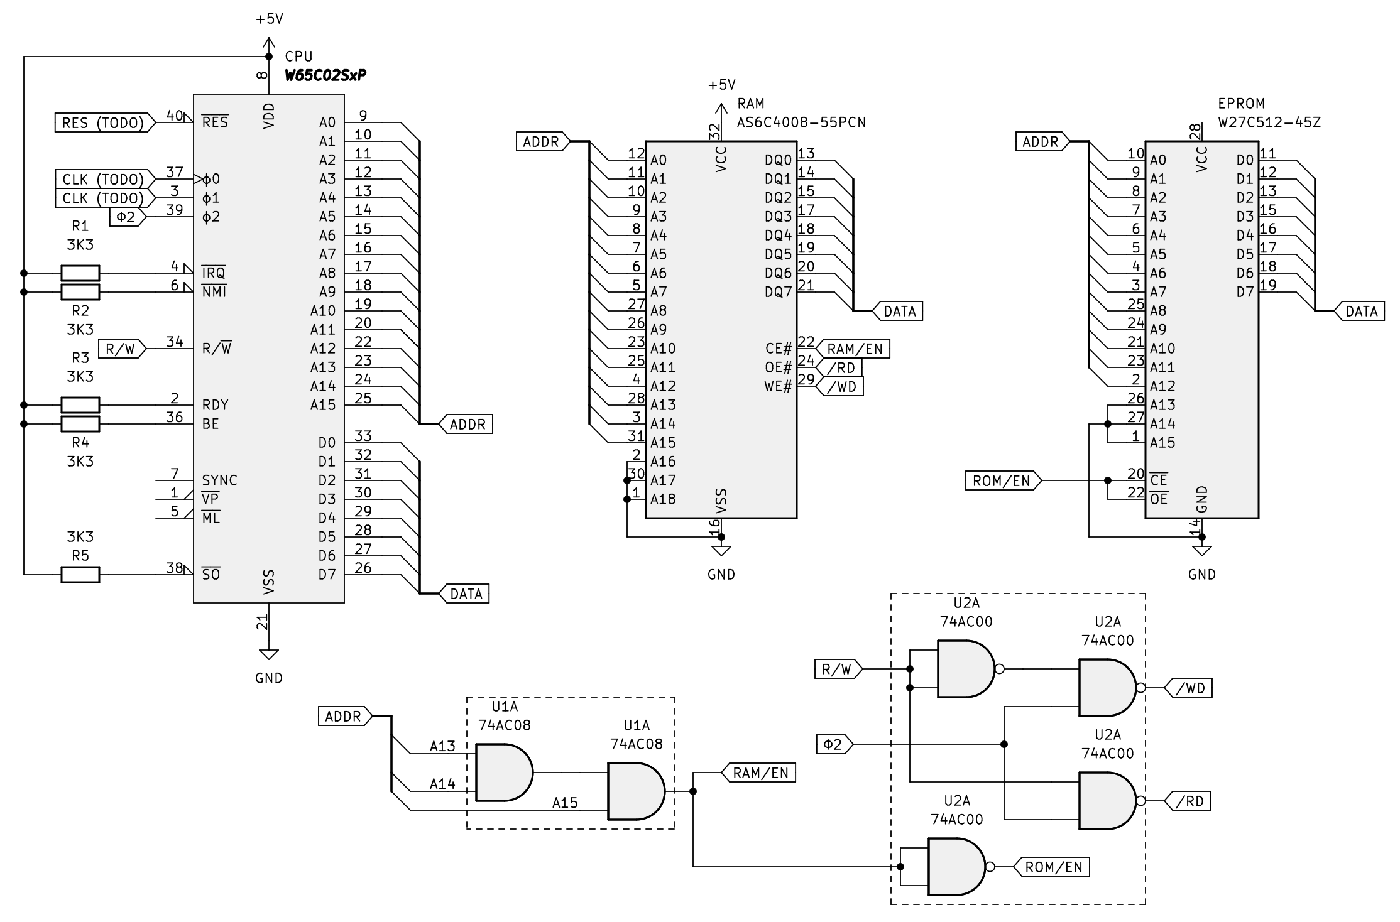
img/v03.png
