and3rson/deck65/img/v04.png

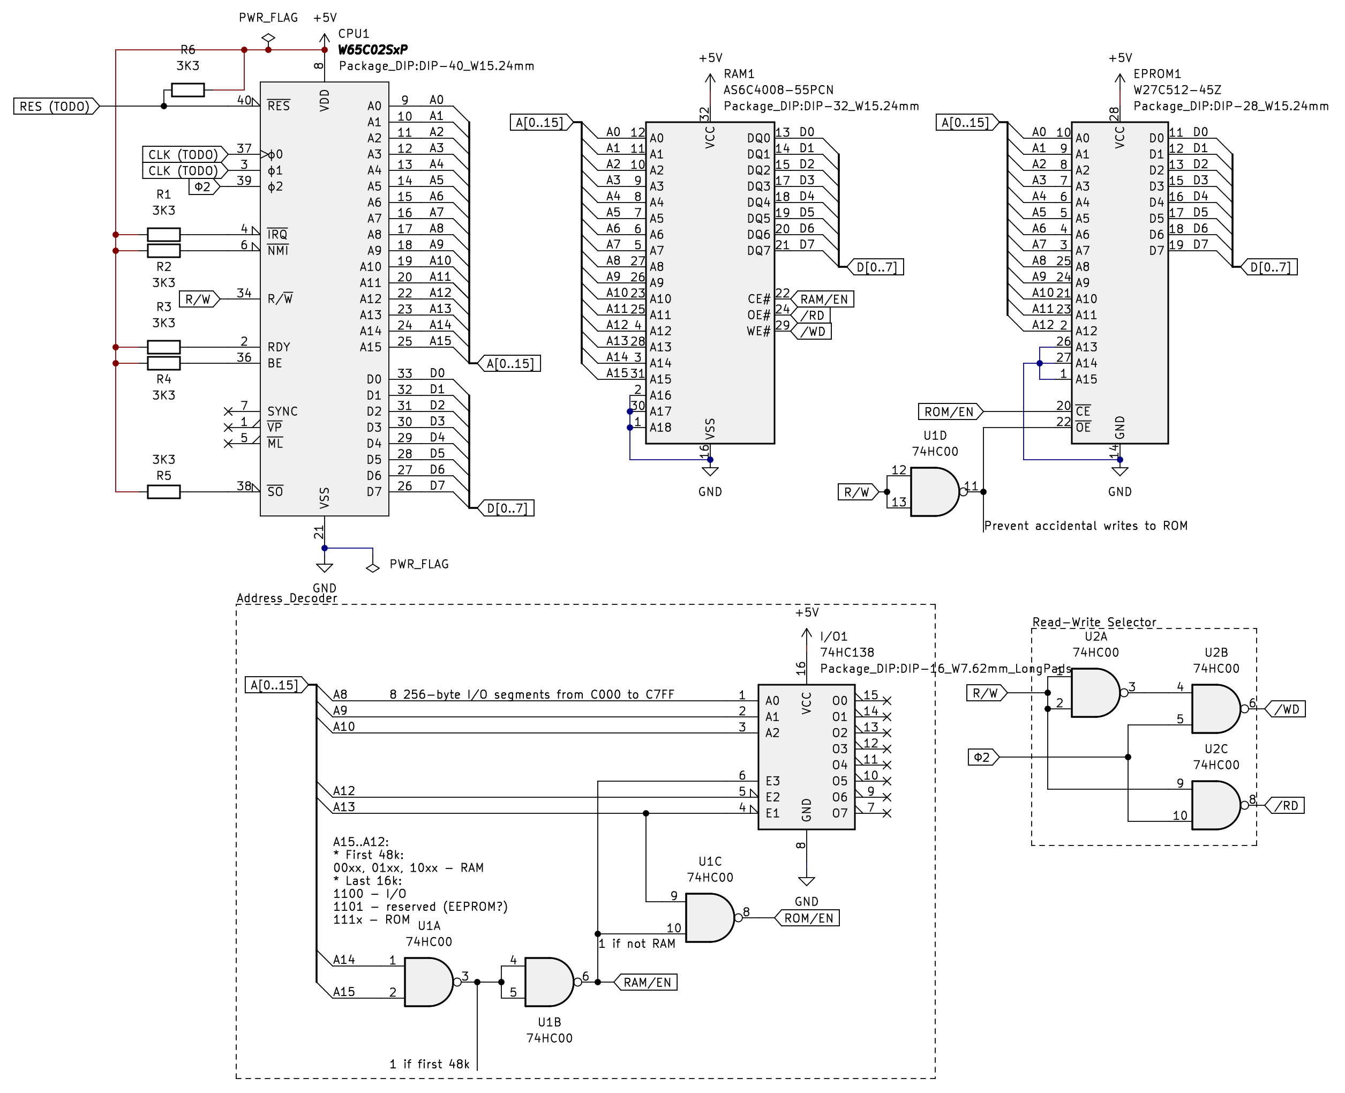
img/v04.png
