and3rson/deck65/img/v04_addr.png

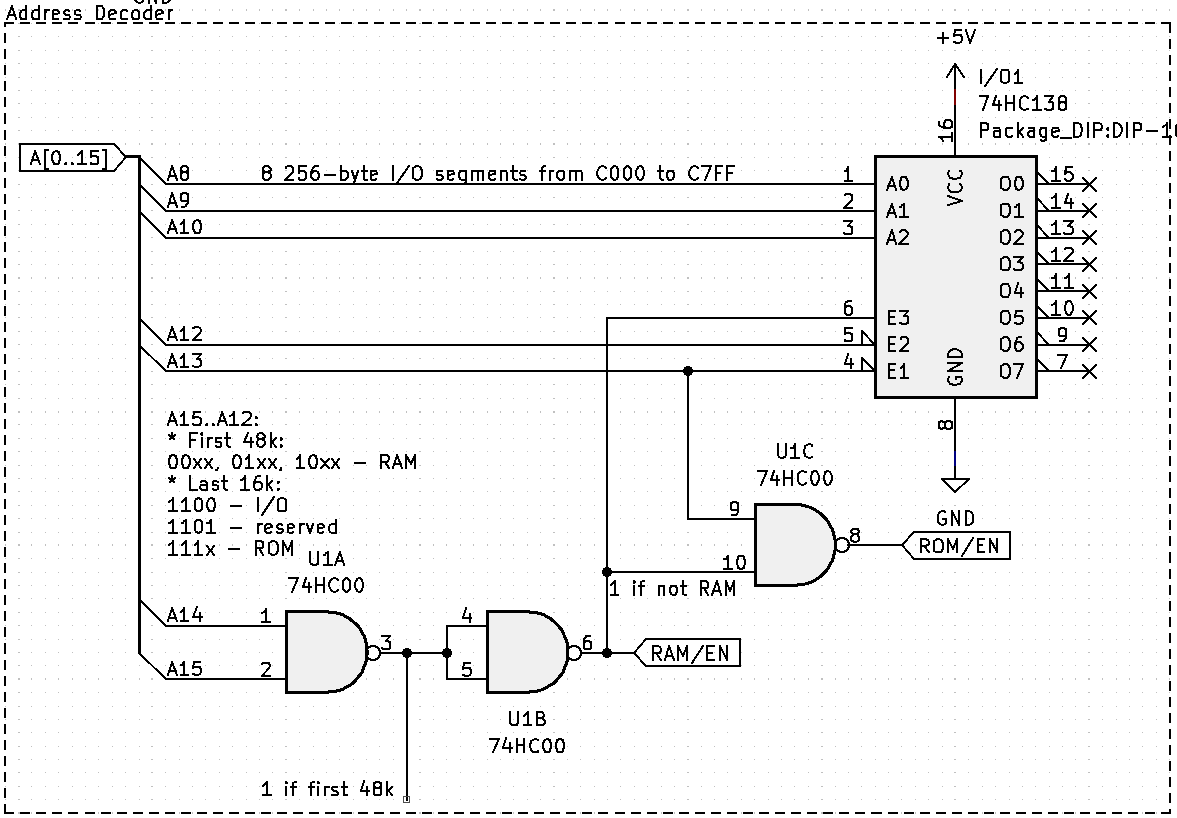
img/v04_addr.png
