and3rson/deck65/img/v05.png

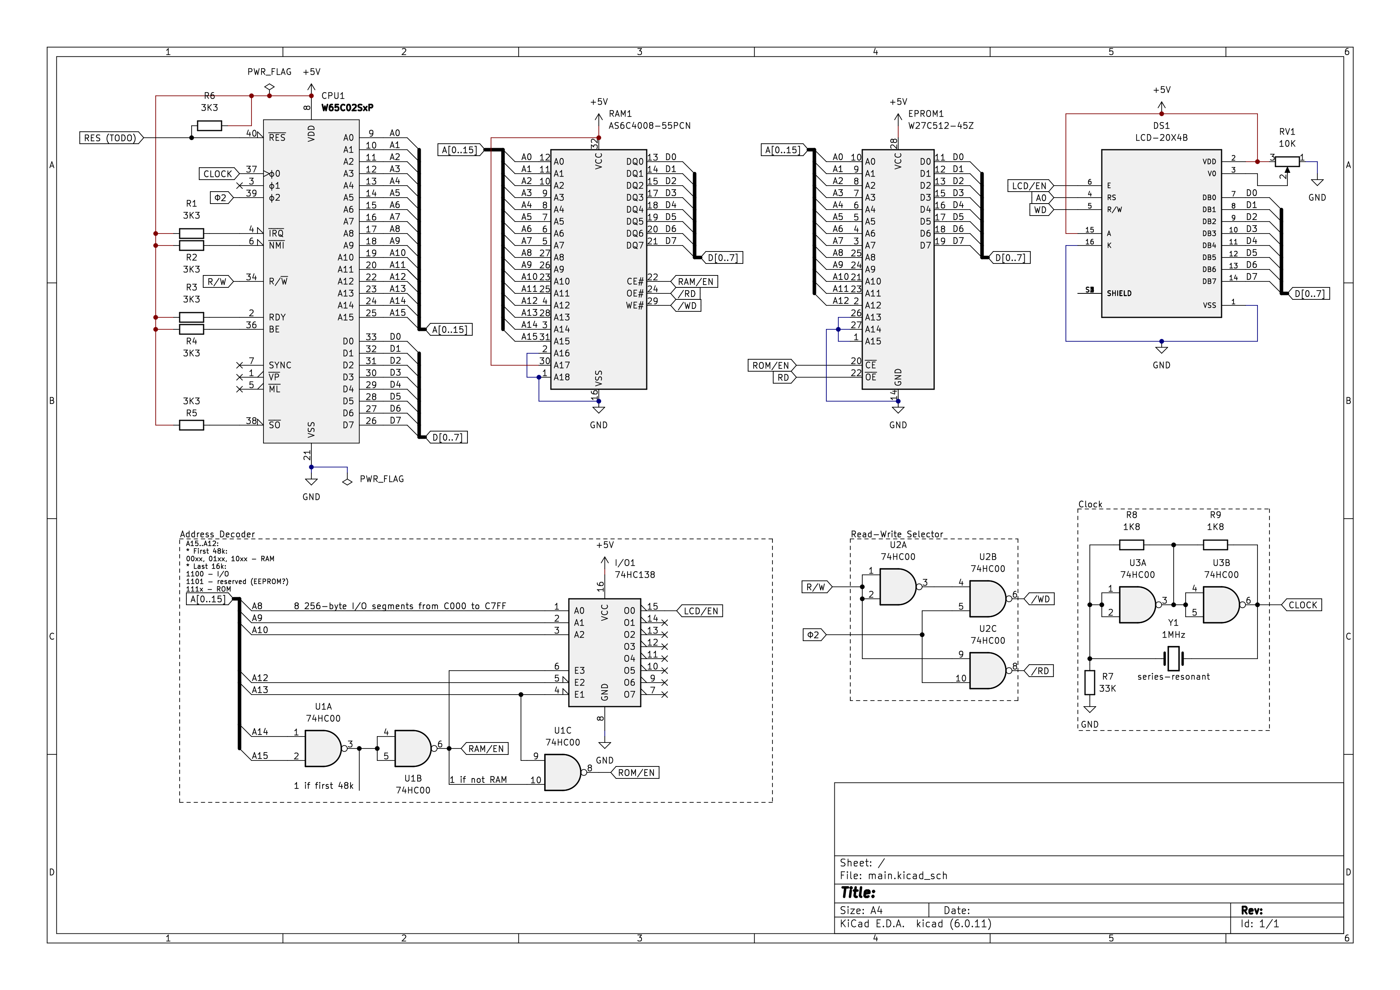
img/v05.png
