and3rson/deck65/img/v06.png

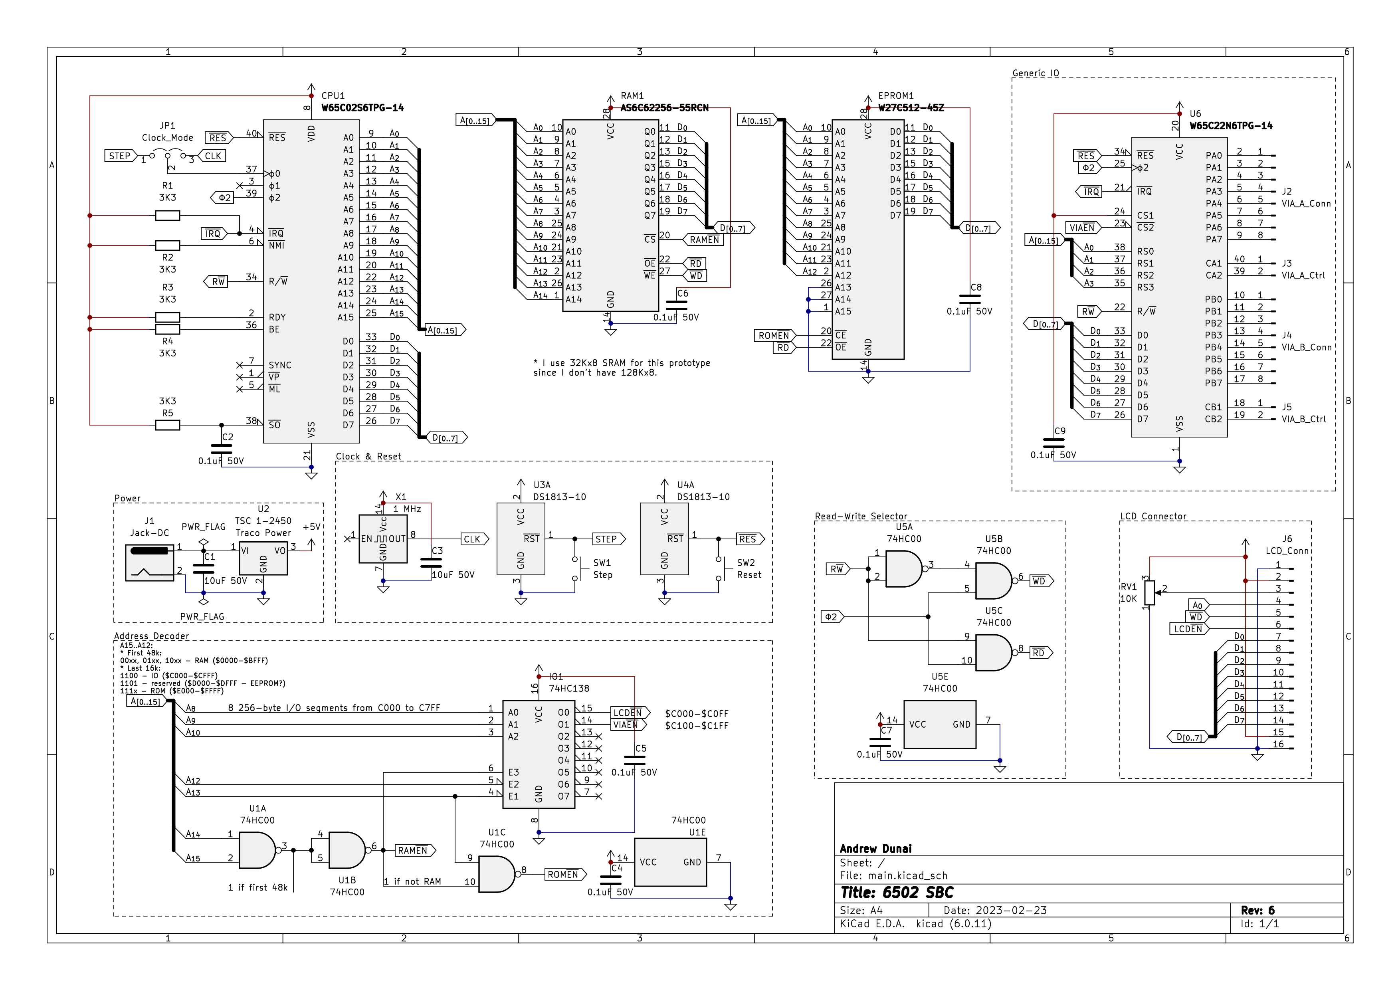
img/v06.png
