and3rson/deck65/img/v07.jpg

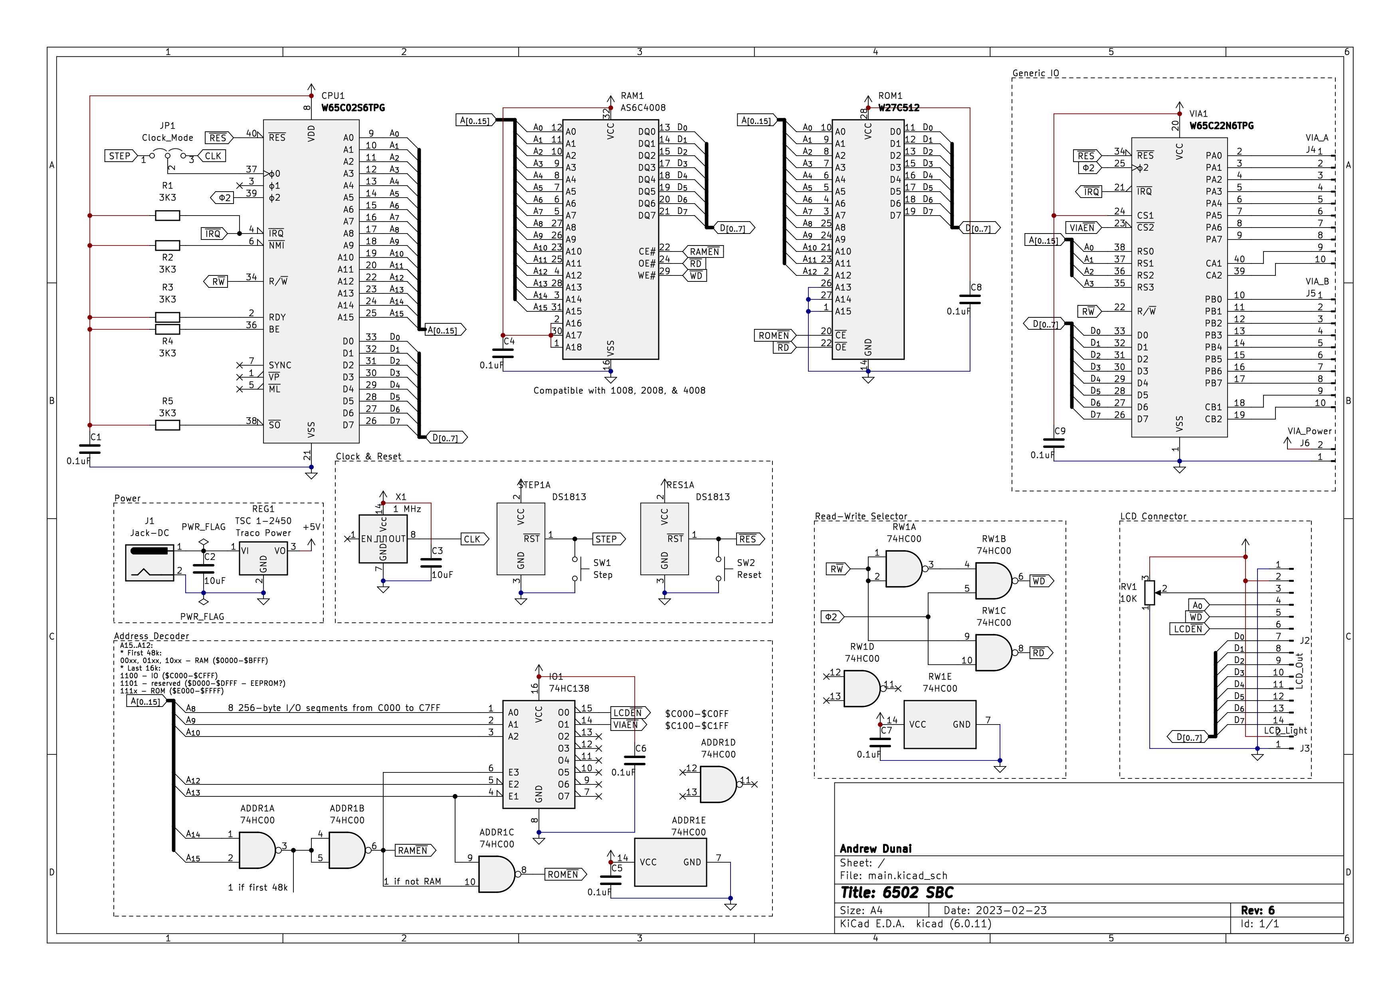
img/v07.jpg
