and3rson/deck65/img/v07_3d.jpg

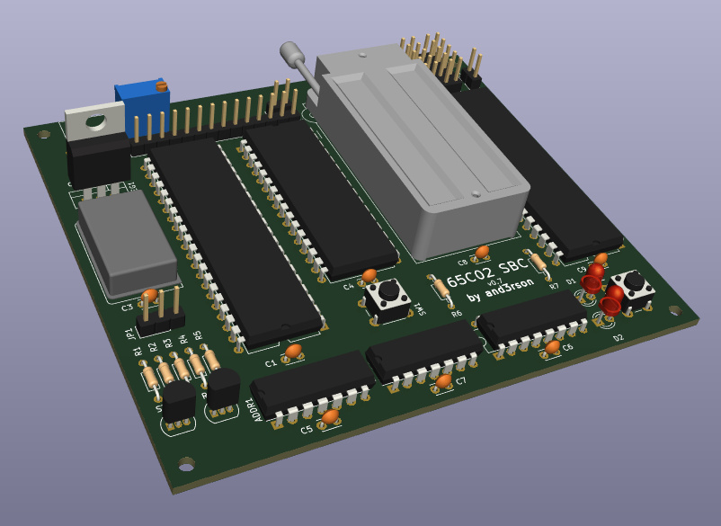
img/v07_3d.jpg
