and3rson/deck65/img/v07_routed.jpg

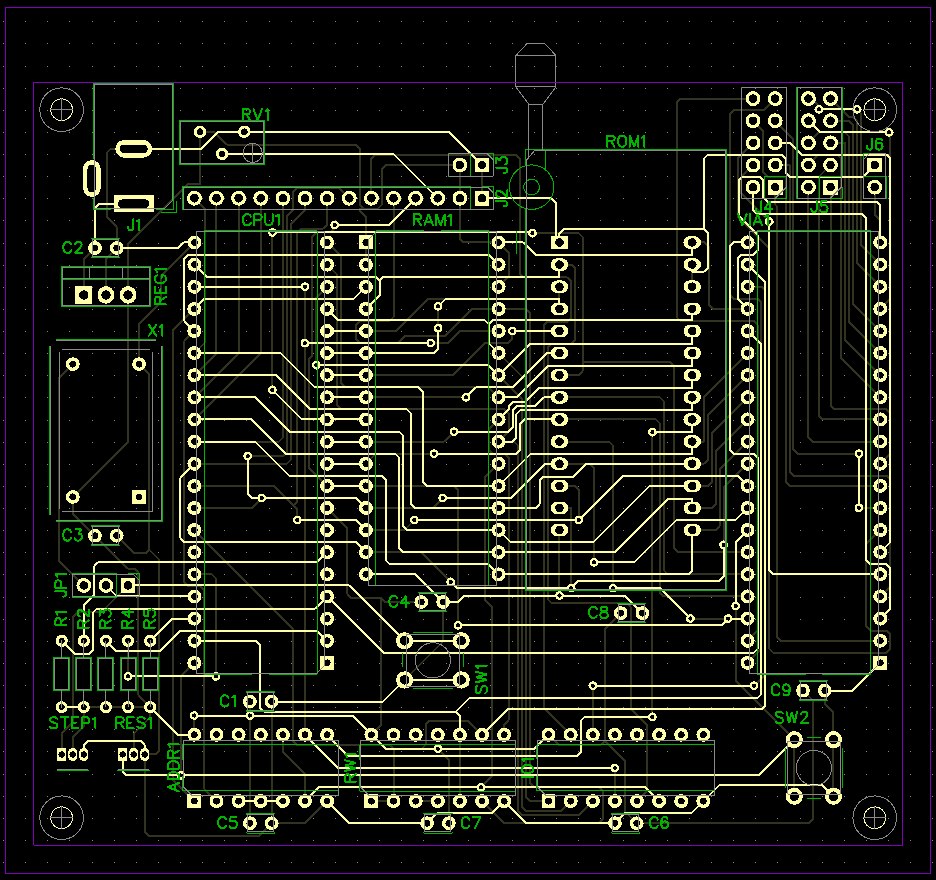
img/v07_routed.jpg
