and3rson/deck65/img/v07_unrouted.jpg

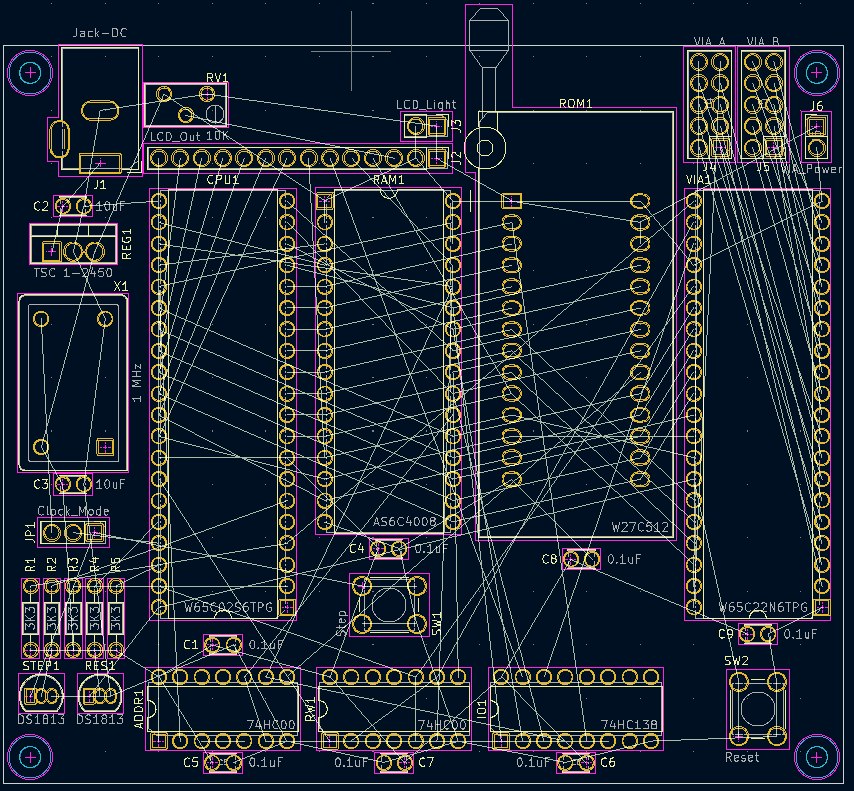
img/v07_unrouted.jpg
