and3rson/deck65/img/v08_3d.jpg

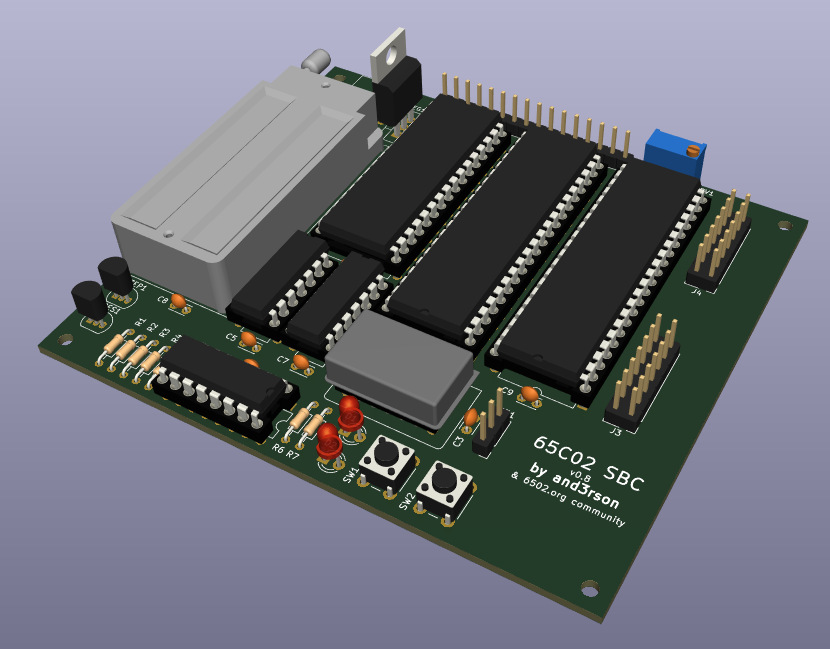
img/v08_3d.jpg
