and3rson/deck65/img/v08_routed.jpg

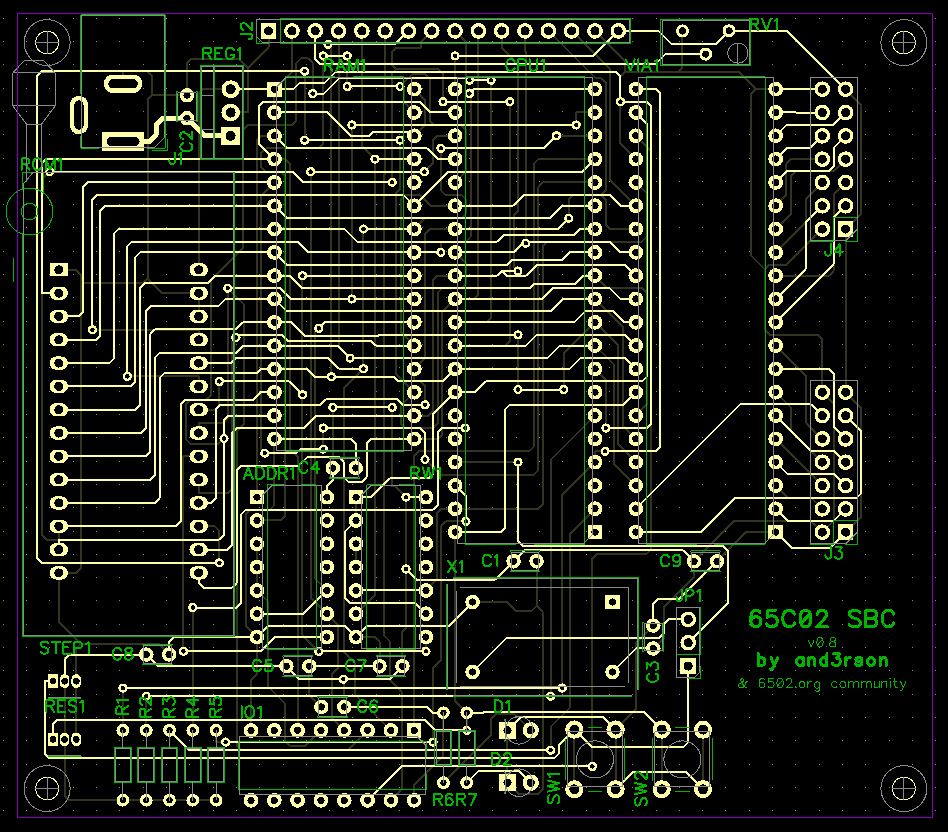
img/v08_routed.jpg
