and3rson/deck65/img/v08_unrouted.jpg

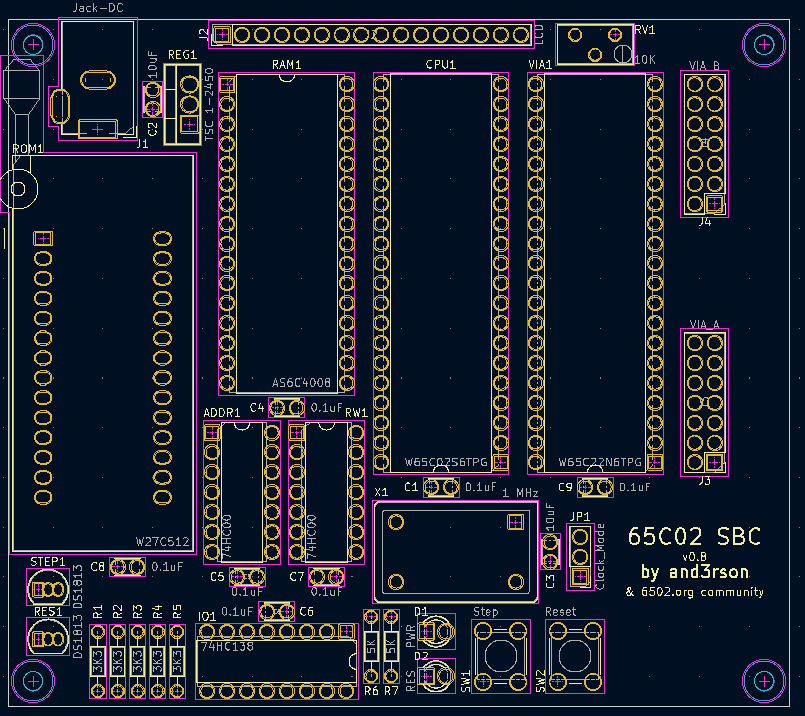
img/v08_unrouted.jpg
