and3rson/deck65/img/v08_unrouted_bw.jpg

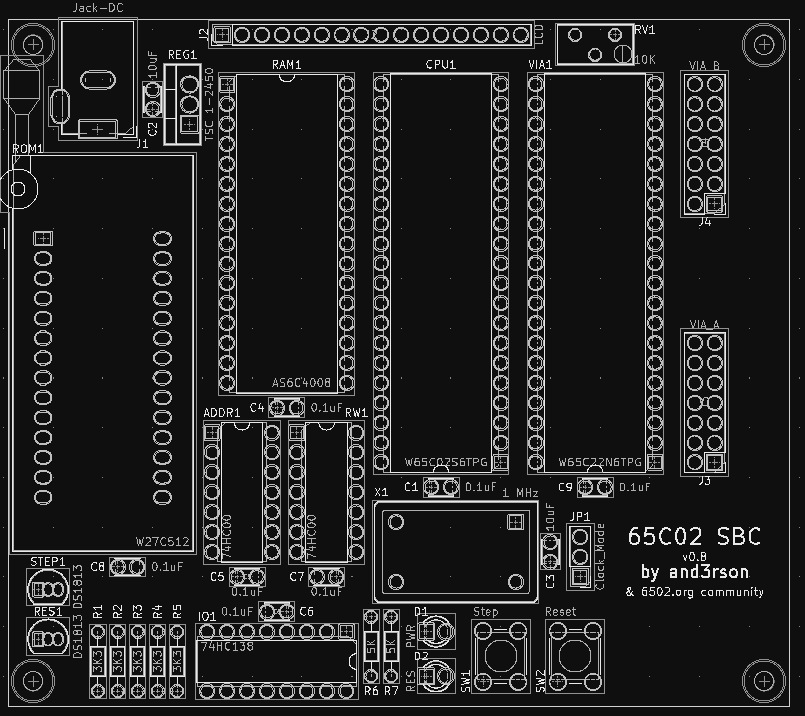
img/v08_unrouted_bw.jpg
