and3rson/deck65/img/v09.jpg

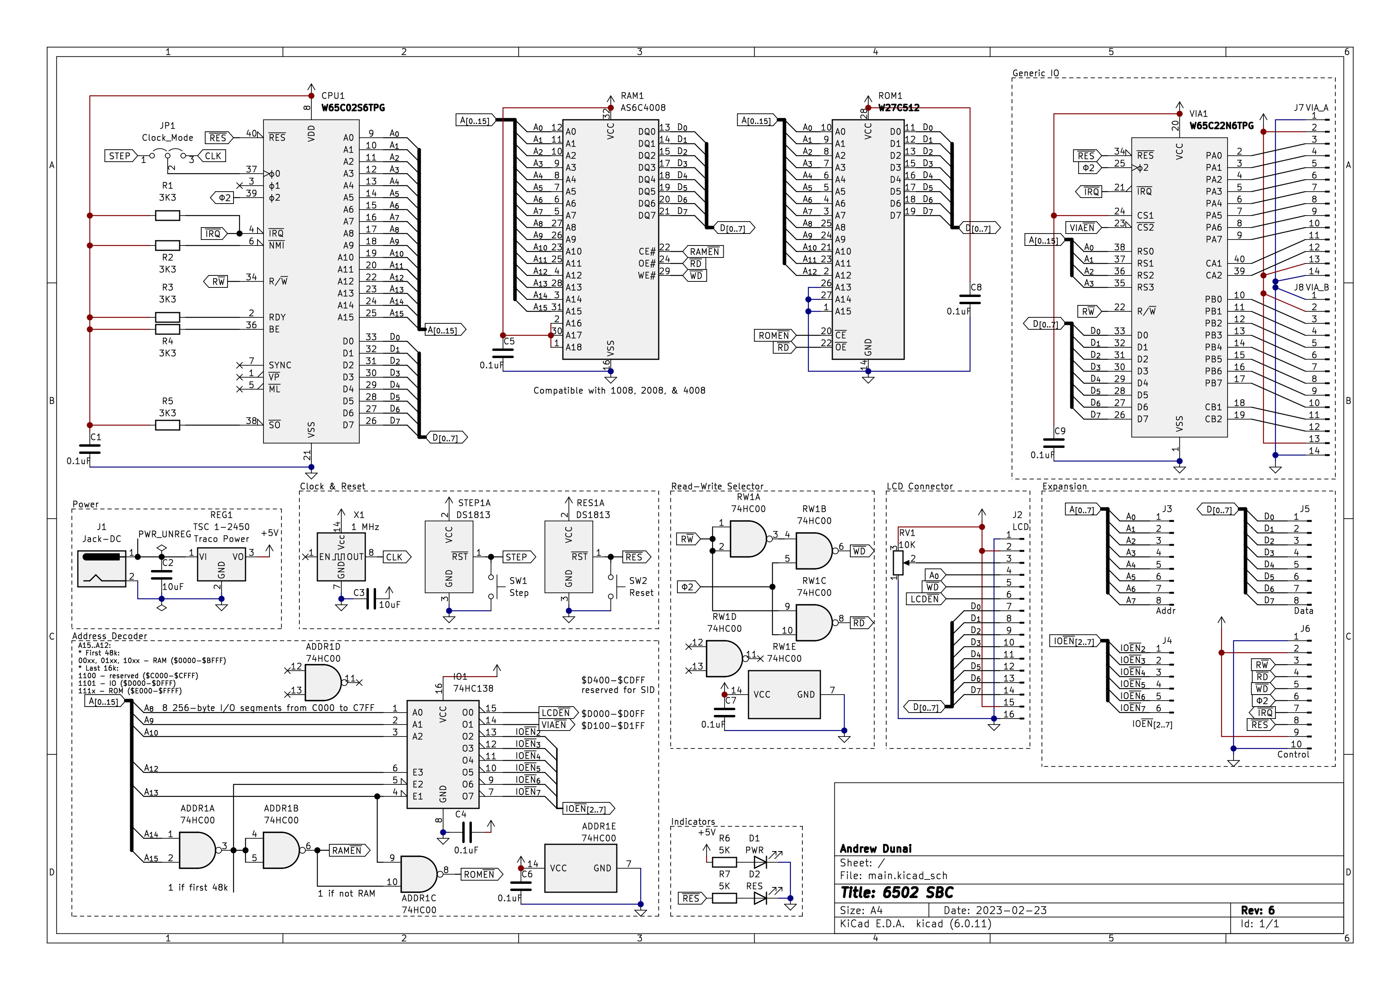
img/v09.jpg
