and3rson/deck65/img/v09_3d.jpg

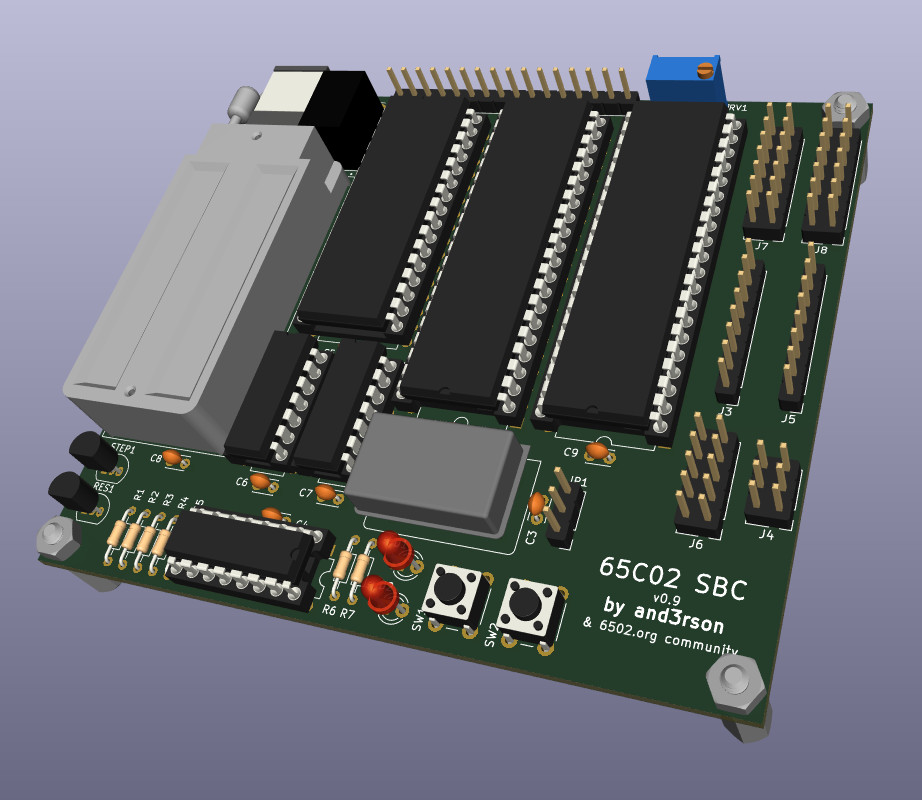
img/v09_3d.jpg
