and3rson/deck65/img/v09_add_numbers.png

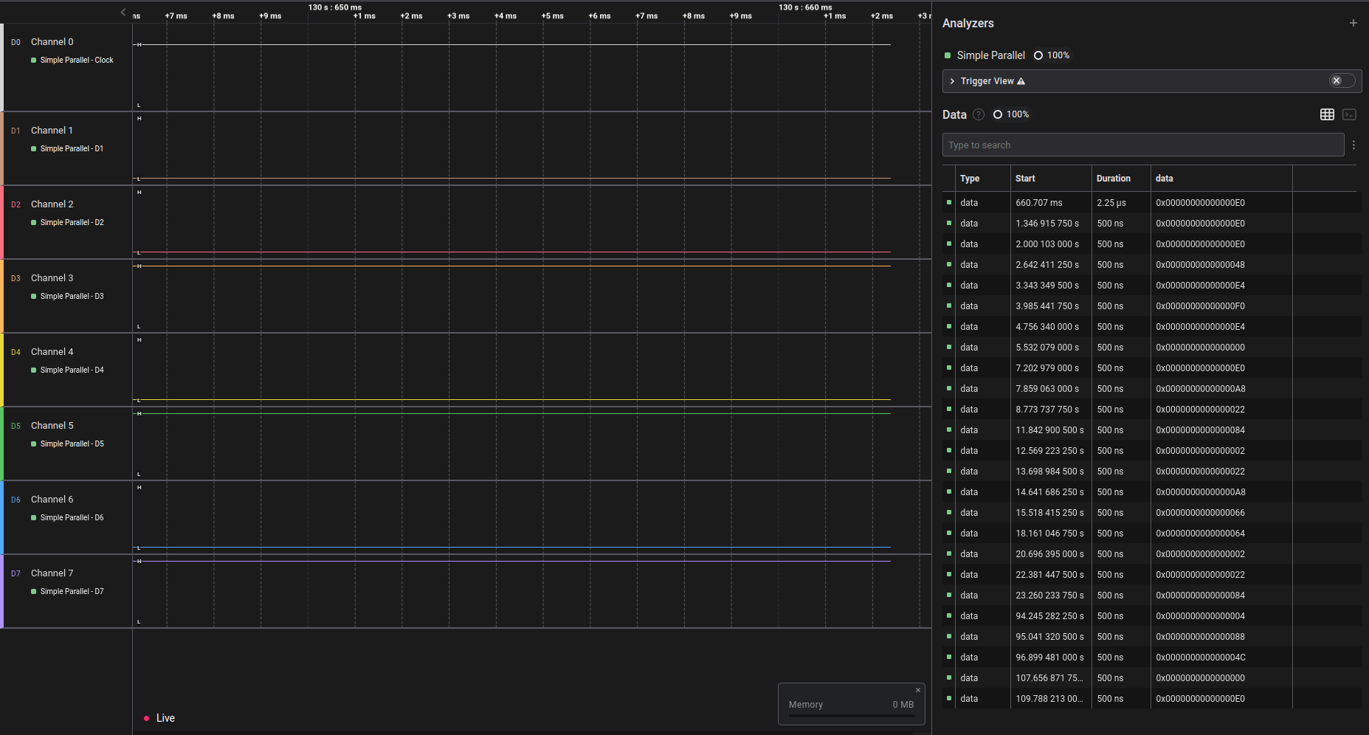
img/v09_add_numbers.png
