and3rson/deck65/img/v09_clock.png

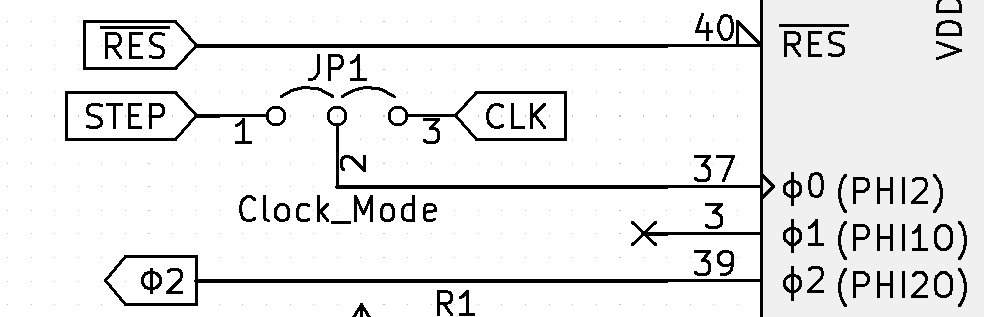
img/v09_clock.png
