and3rson/deck65/img/v09_clock_finally.png

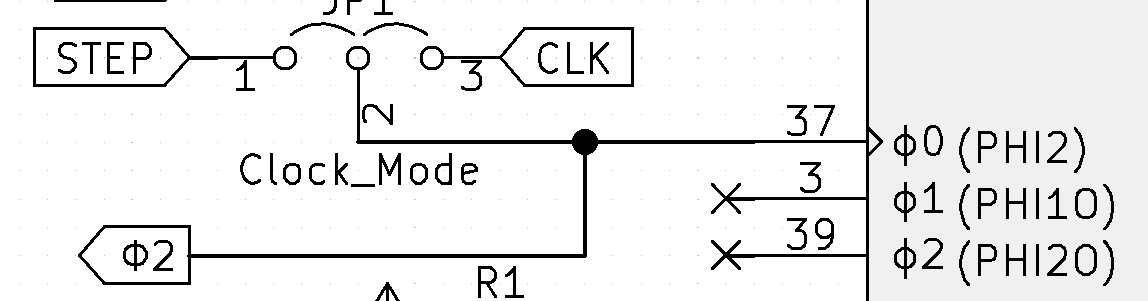
img/v09_clock_finally.png
