and3rson/deck65/img/v09_final.jpg

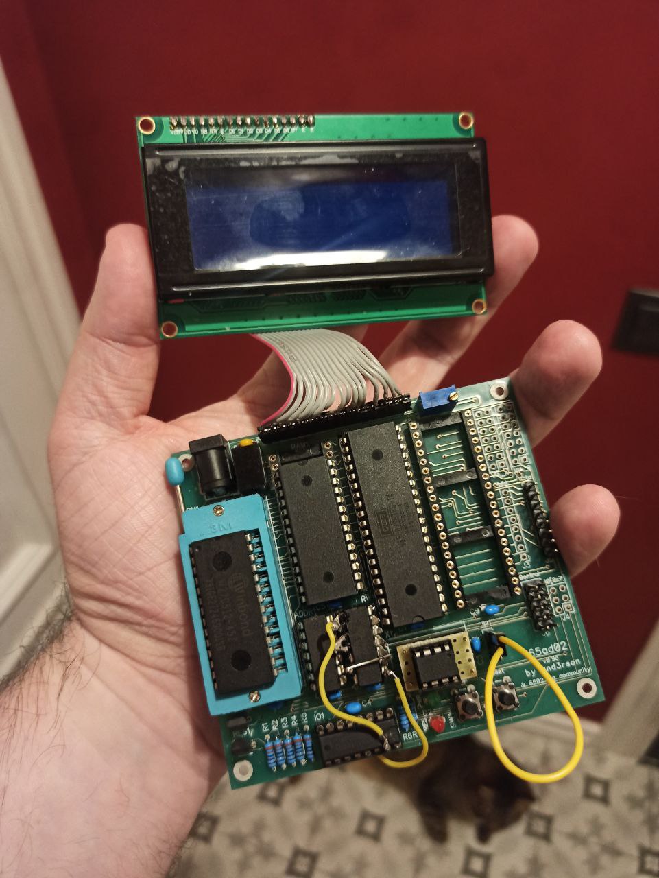
img/v09_final.jpg
