and3rson/deck65/img/v09_hello.jpg

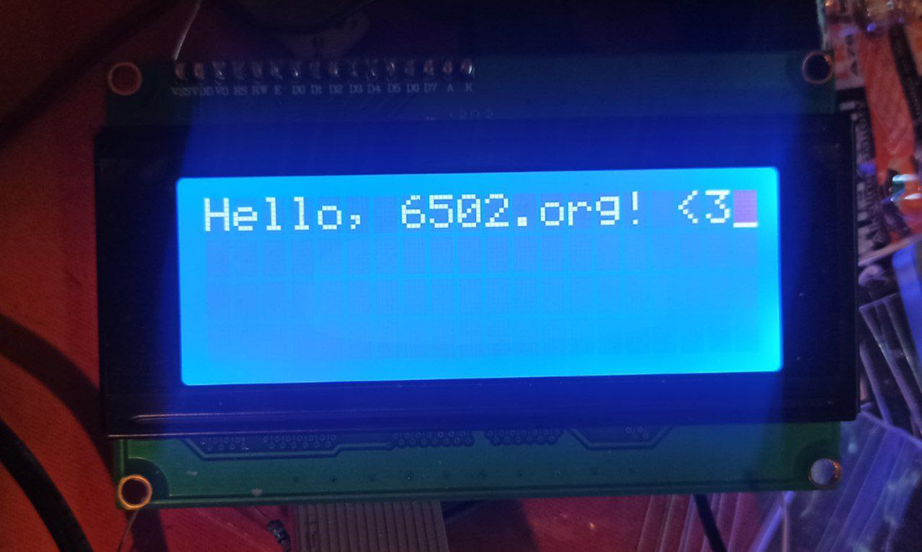
img/v09_hello.jpg
