and3rson/deck65/img/v09_routed2.png

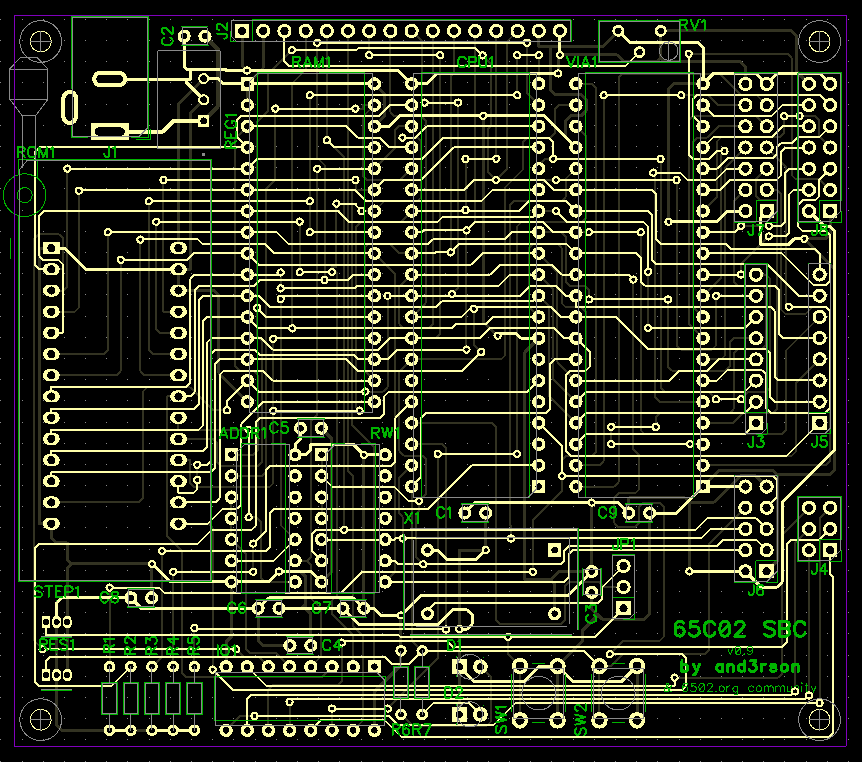
img/v09_routed2.png
