and3rson/deck65/img/v09_routed_bw.jpg

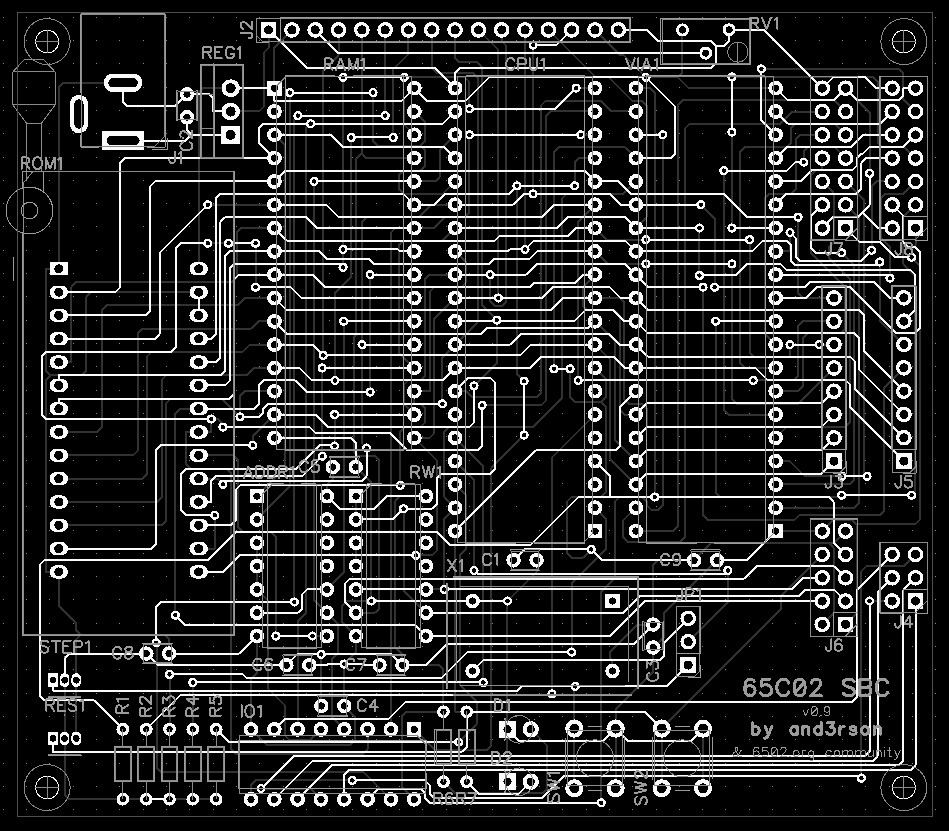
img/v09_routed_bw.jpg
