and3rson/deck65/img/v09_unrouted.jpg

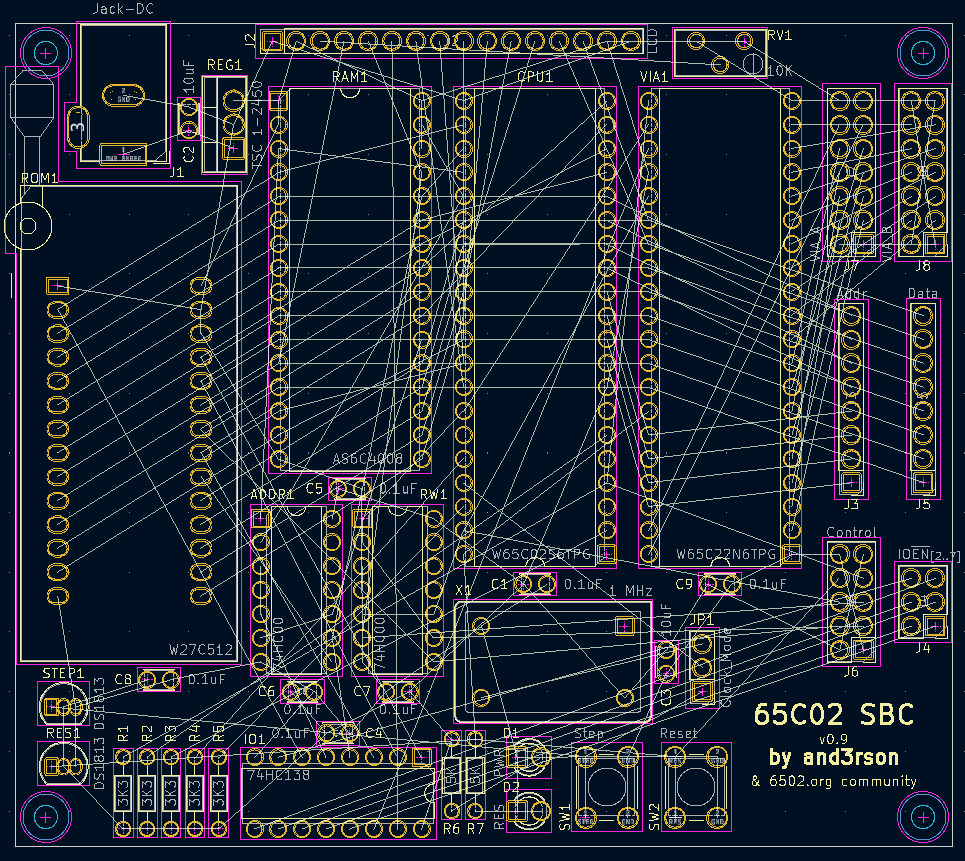
img/v09_unrouted.jpg
