and3rson/deck65/img/v10.png

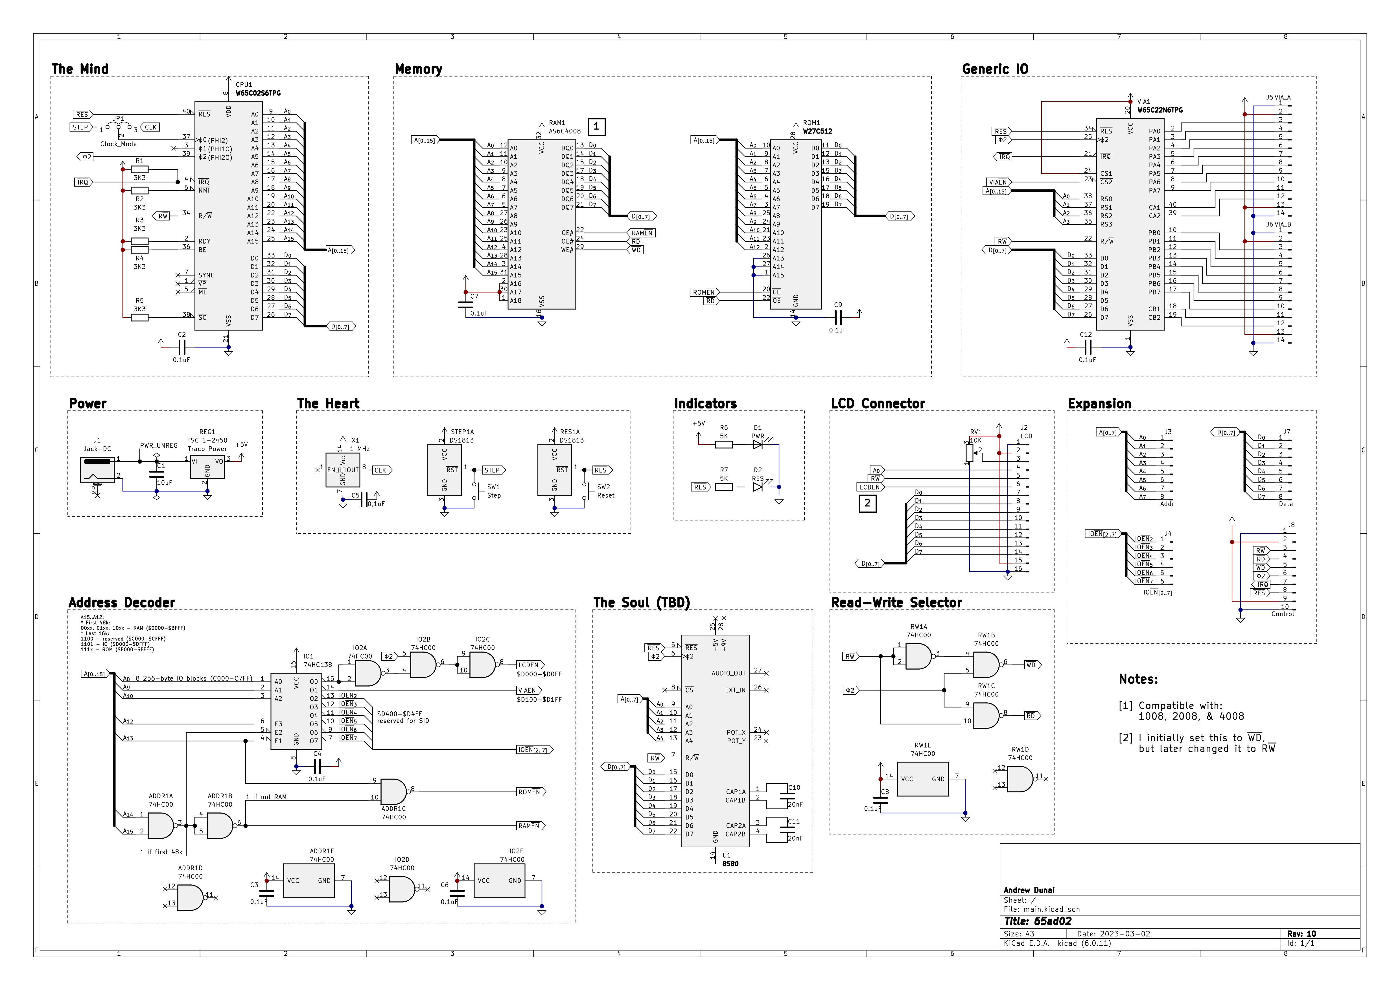
img/v10.png
