and3rson/deck65/img/v10_3d.jpg

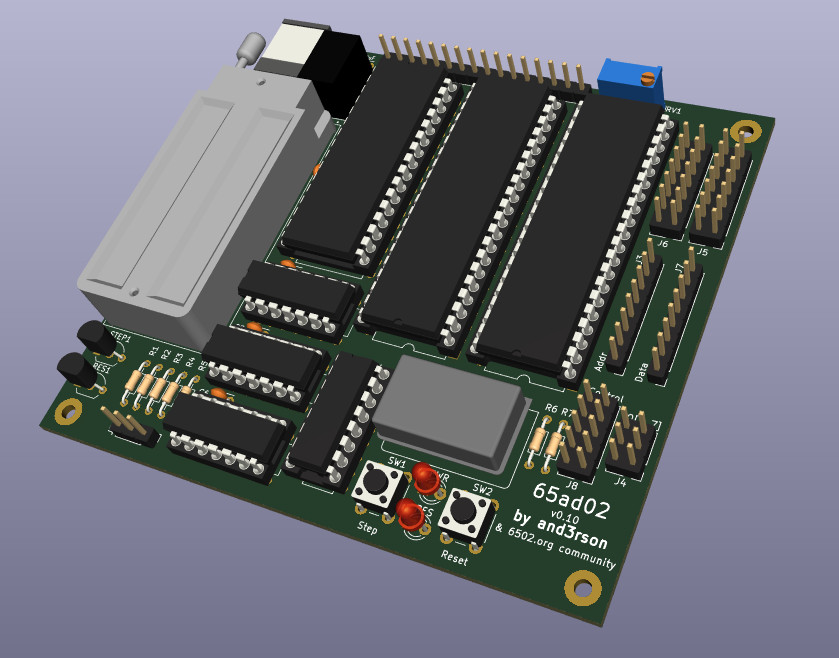
img/v10_3d.jpg
