and3rson/deck65/img/v10_banking.png

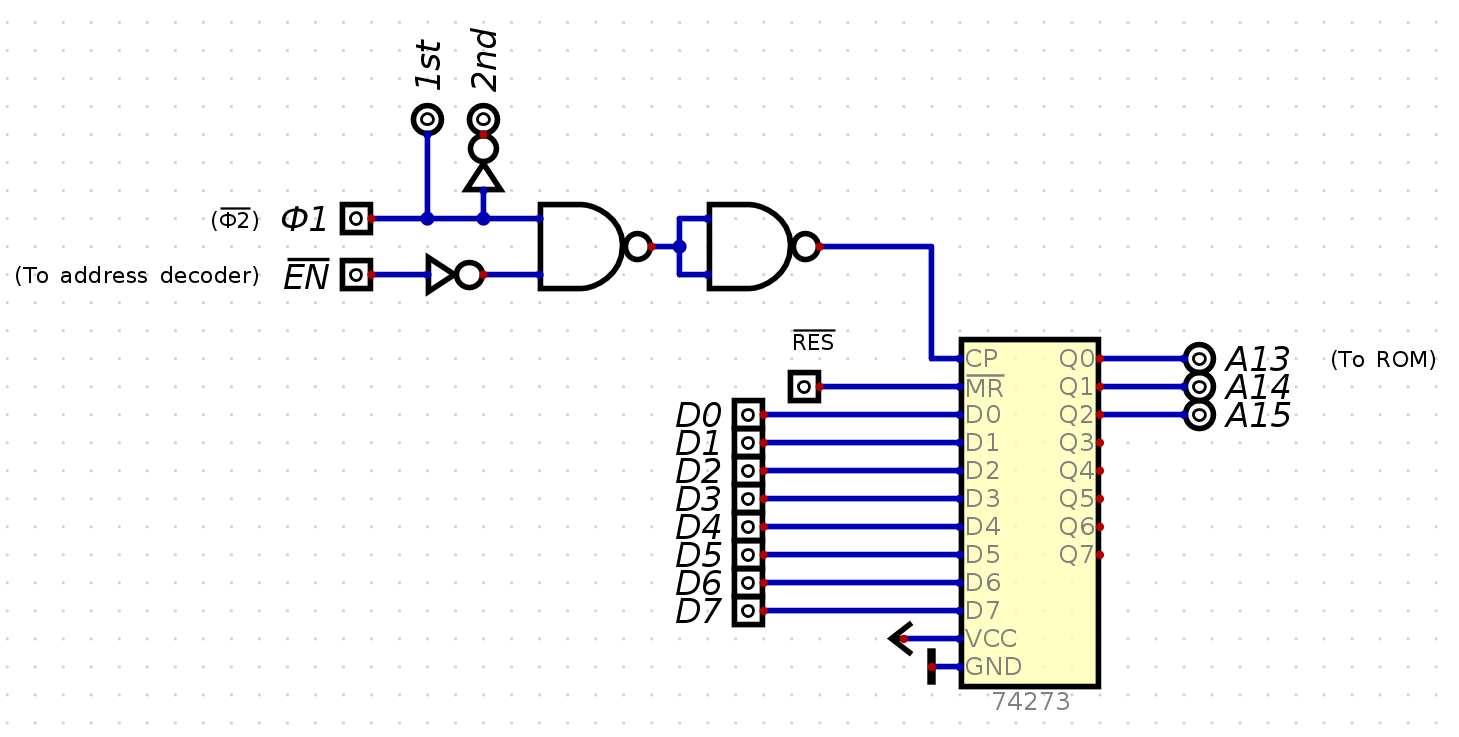
img/v10_banking.png
