and3rson/deck65/img/v10_routed.png

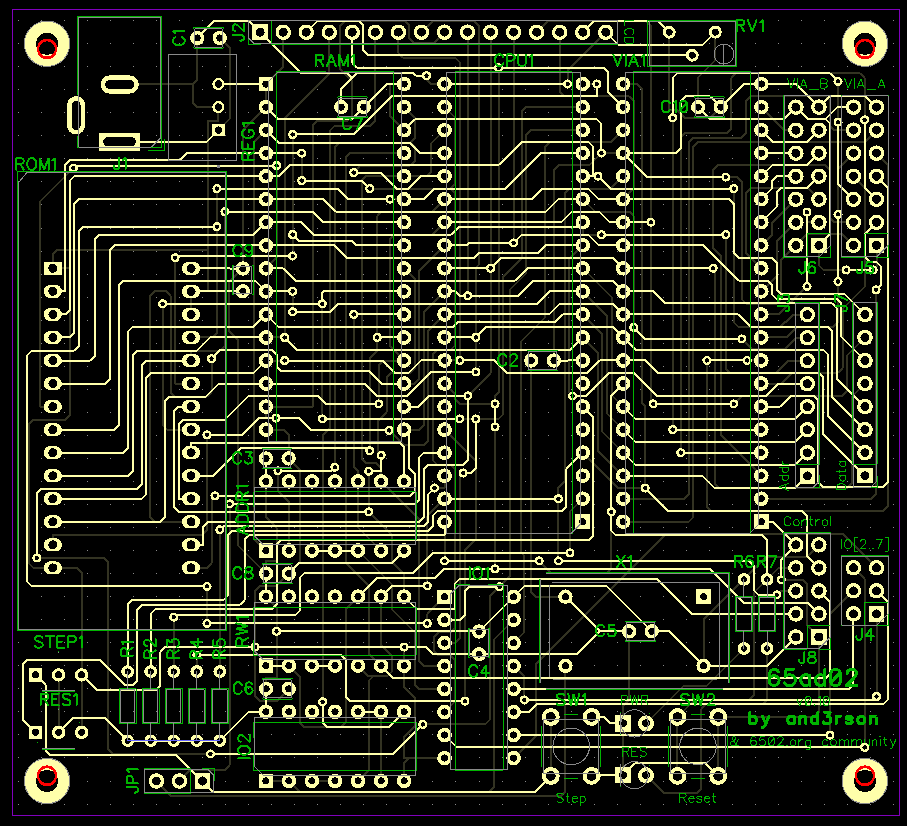
img/v10_routed.png
