and3rson/deck65/img/v10_unrouted.png

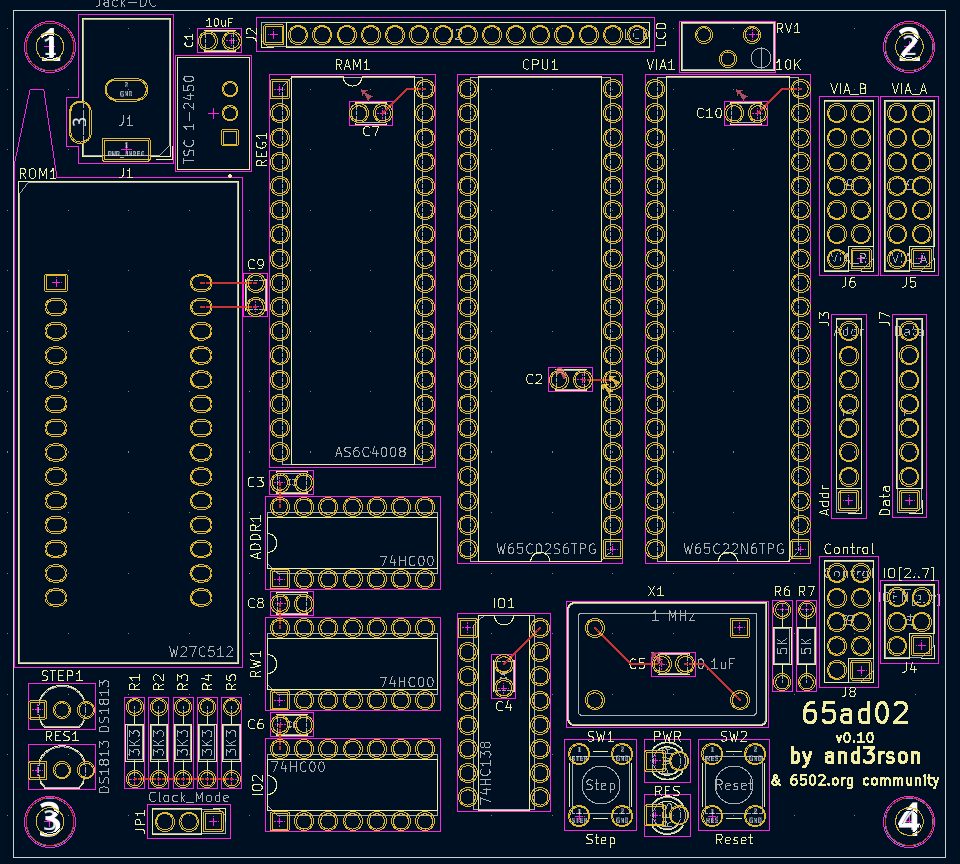
img/v10_unrouted.png
