and3rson/deck65/img/v11.jpg

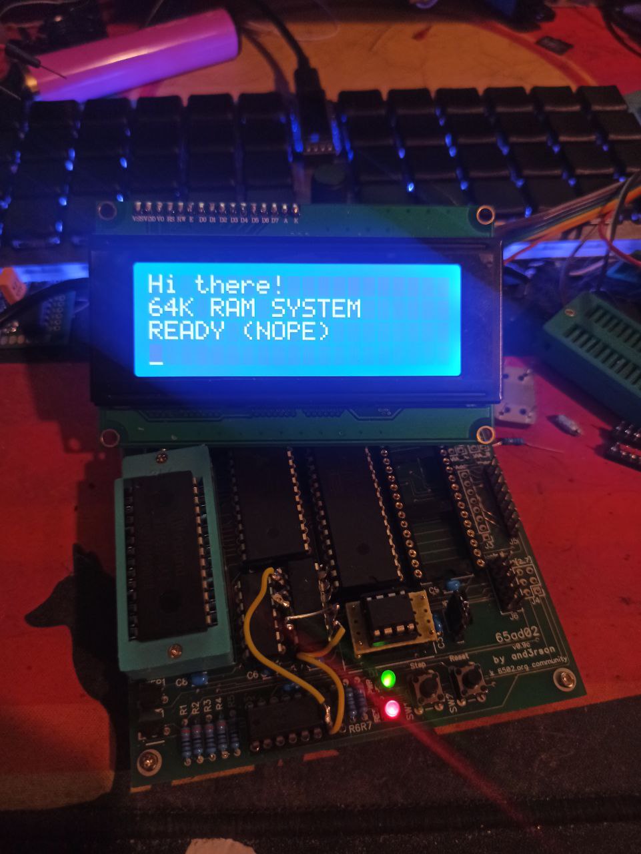
img/v11.jpg
