and3rson/deck65/img/v12.png

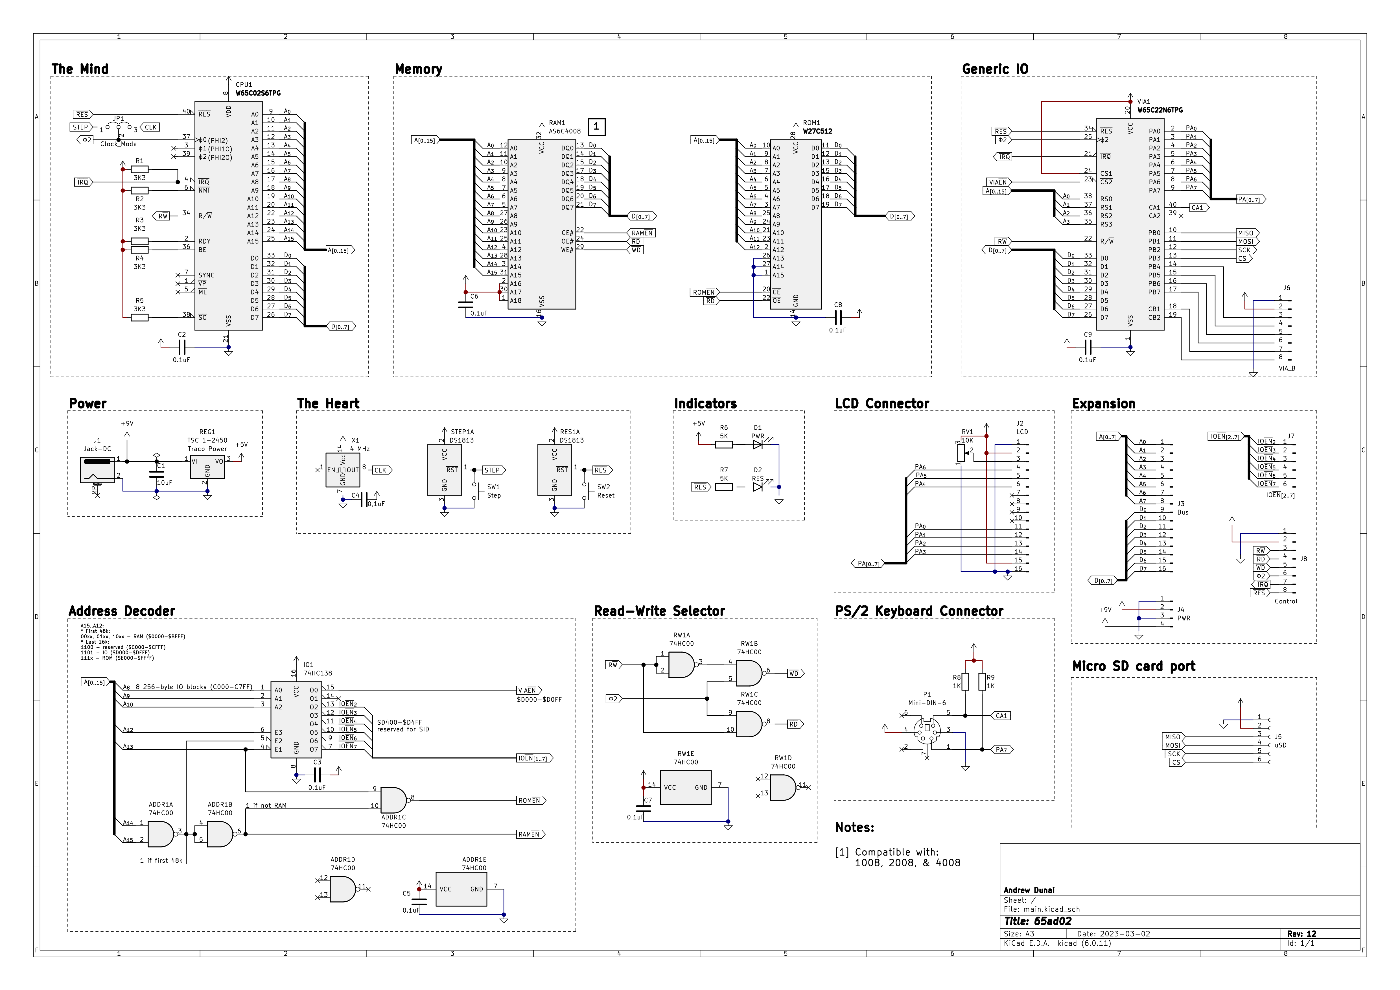
img/v12.png
