and3rson/deck65/img/v12_routed.png

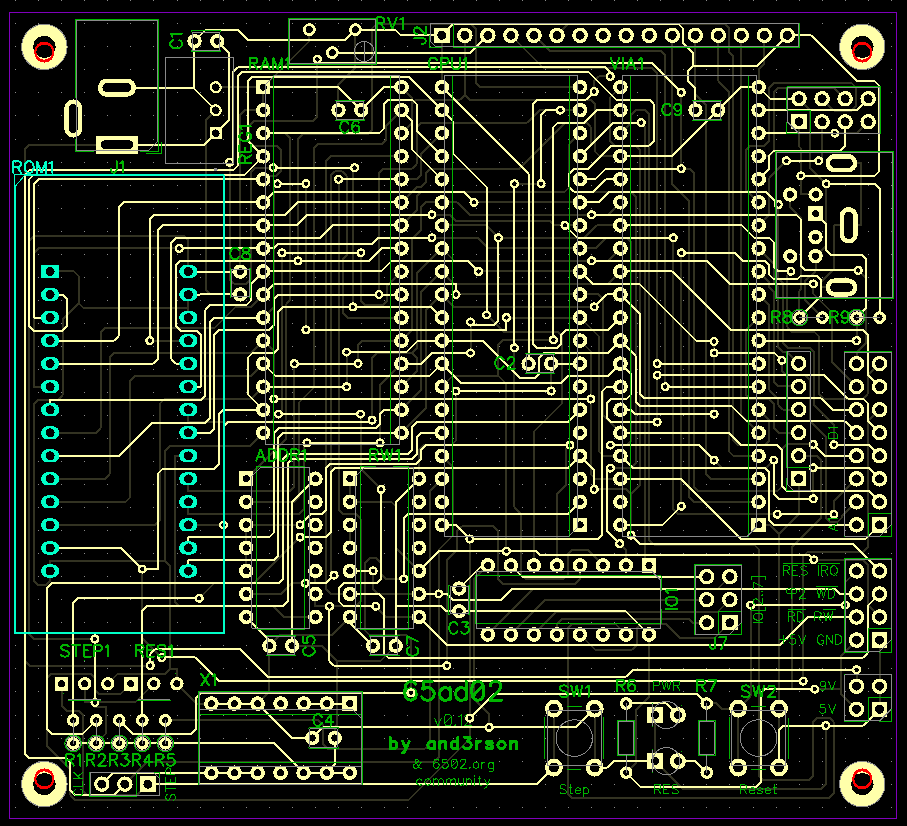
img/v12_routed.png
