and3rson/deck65/img/v13_address_decoder.png

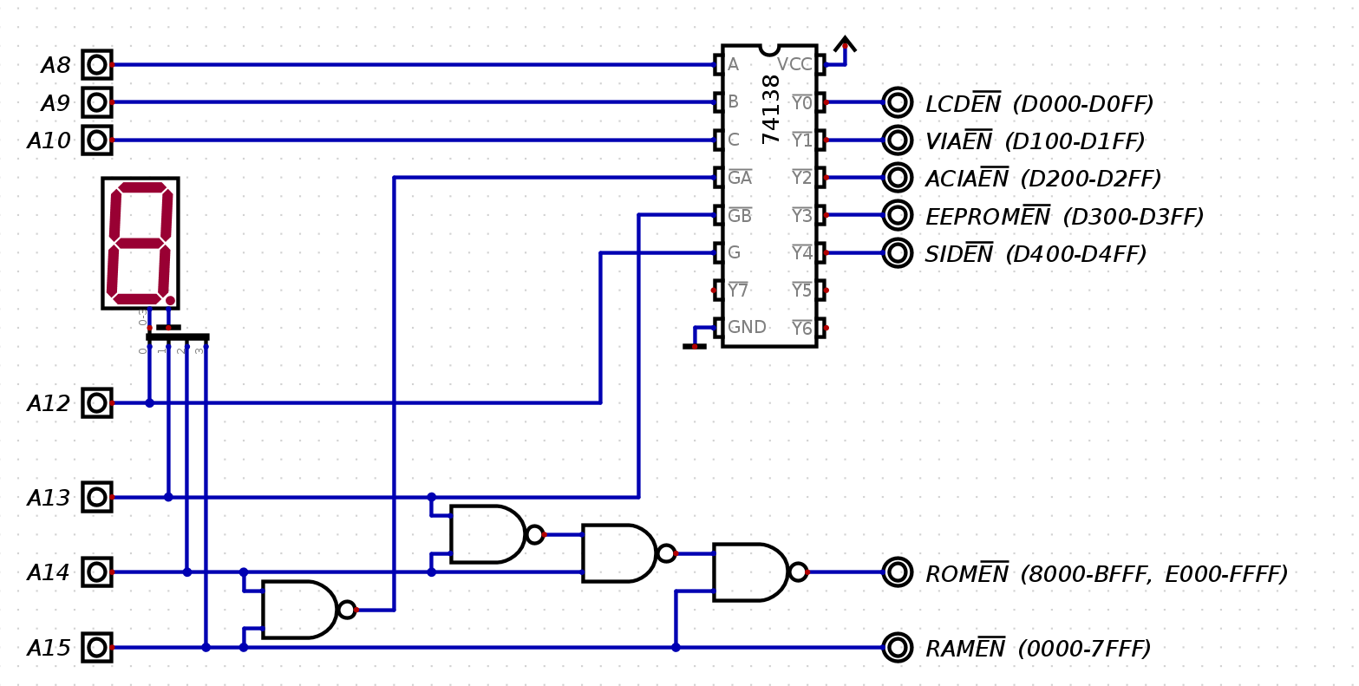
img/v13_address_decoder.png
