and3rson/deck65/img/v15_final.jpg

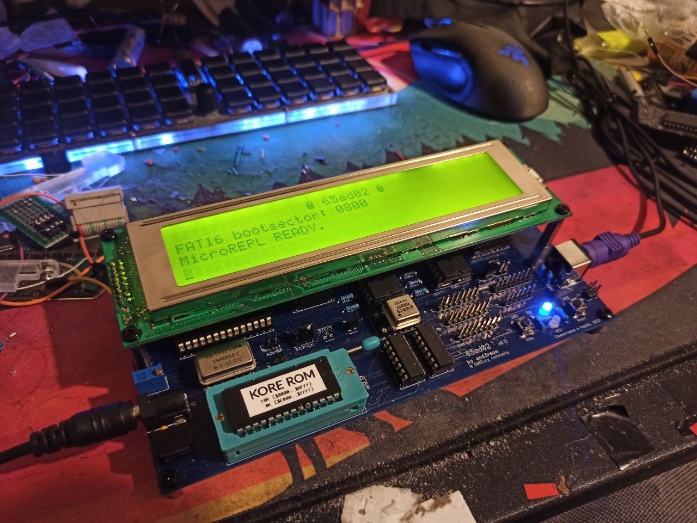
img/v15_final.jpg
