and3rson/deck65/img/v15_final_naked.jpg

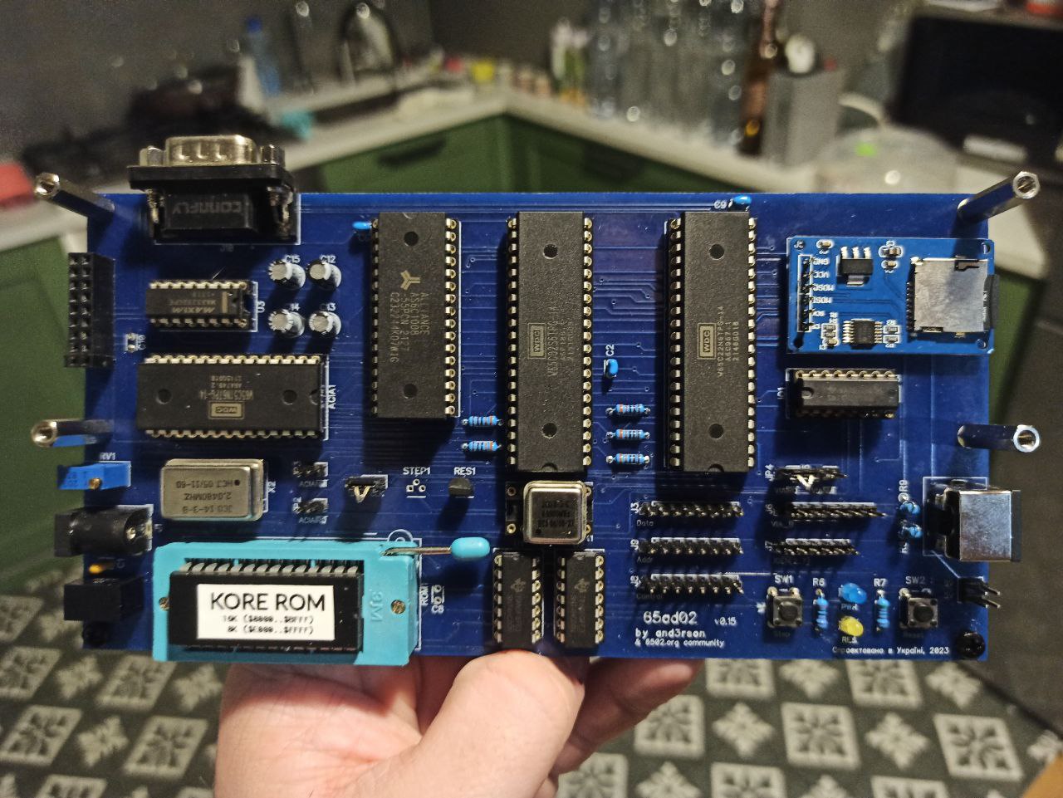
img/v15_final_naked.jpg
