and3rson/deck65/img/v15_irl3.jpg

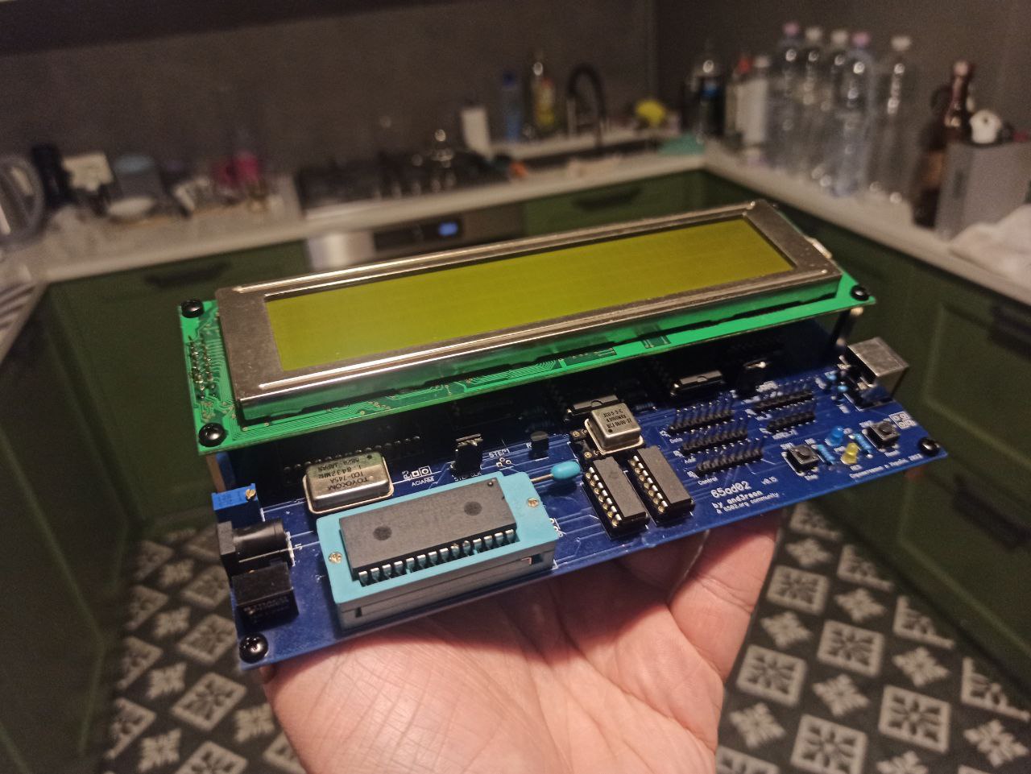
img/v15_irl3.jpg
