and3rson/deck65/img/v15_lcd_mirror.png

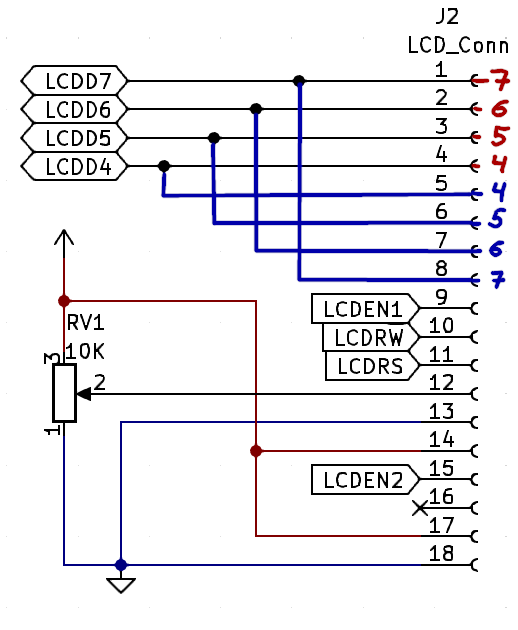
img/v15_lcd_mirror.png
