and3rson/deck65/img/v15_legs.jpg

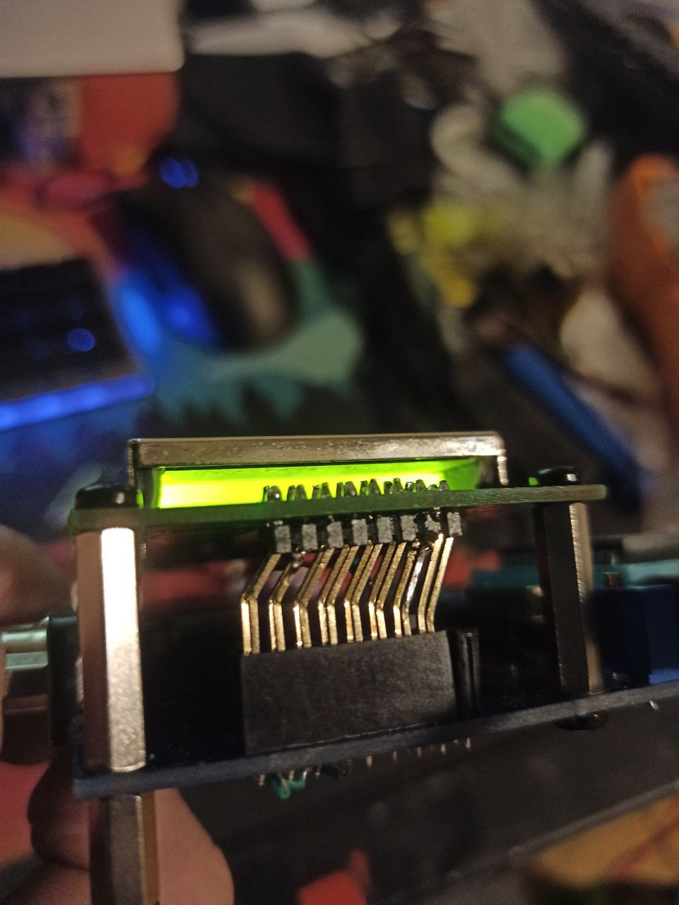
img/v15_legs.jpg
