and3rson/deck65/img/v15_pcb.png

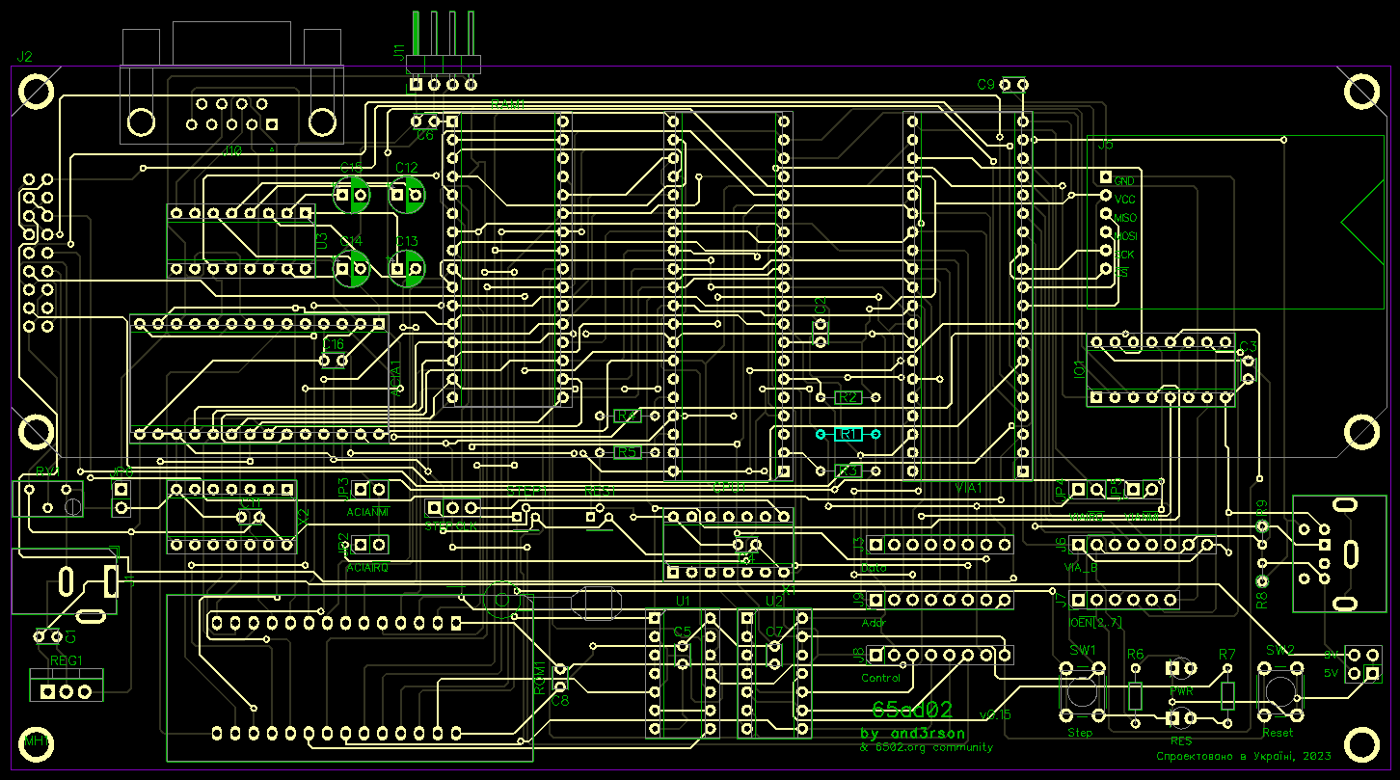
img/v15_pcb.png
