and3rson/deck65/img/v15_pcb_irl2.jpg

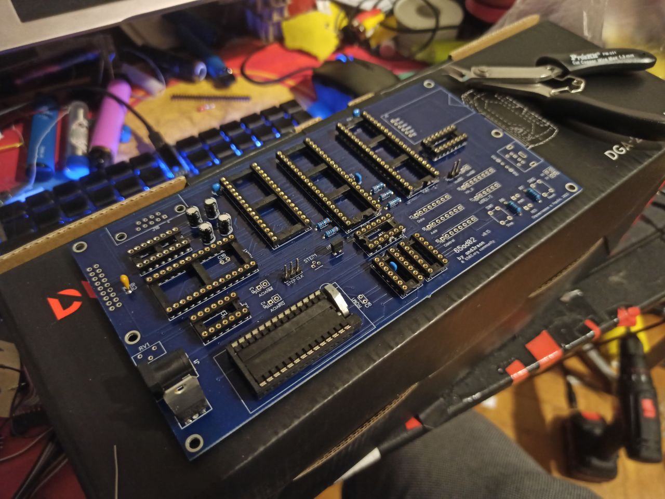
img/v15_pcb_irl2.jpg
