and3rson/deck65/img/v15_pcb_irl.jpg

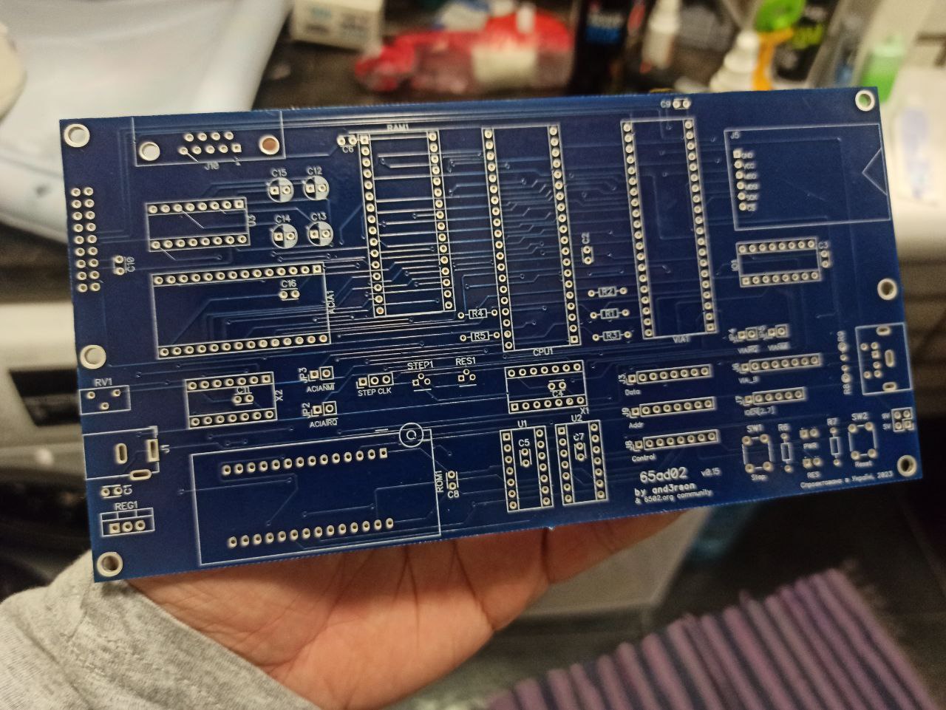
img/v15_pcb_irl.jpg
