and3rson/deck65/img/v16_gal_and_t6963c.jpg

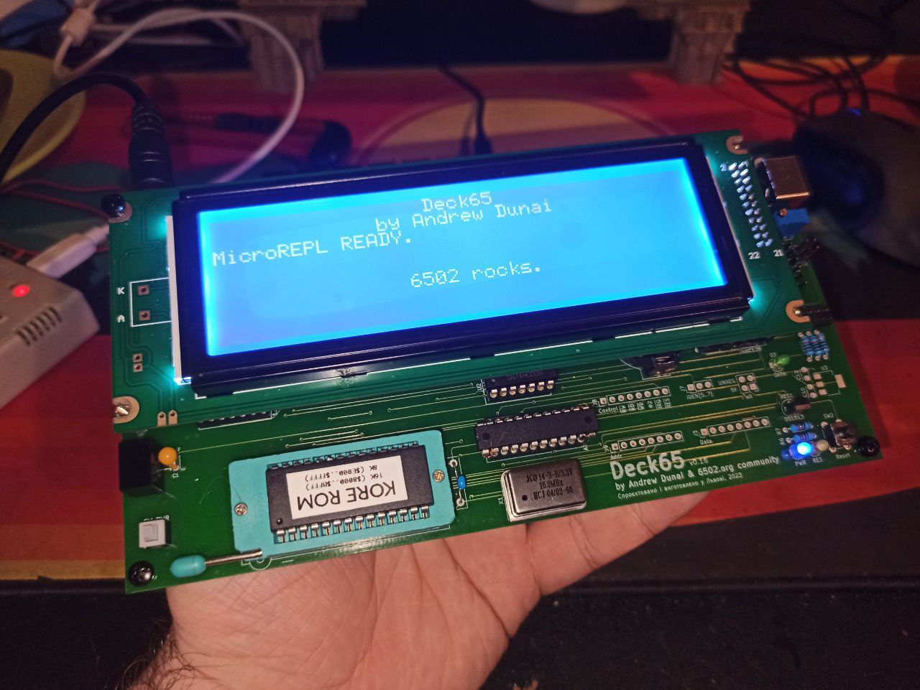
img/v16_gal_and_t6963c.jpg
