and3rson/deck65/img/v16_it_fits.jpg

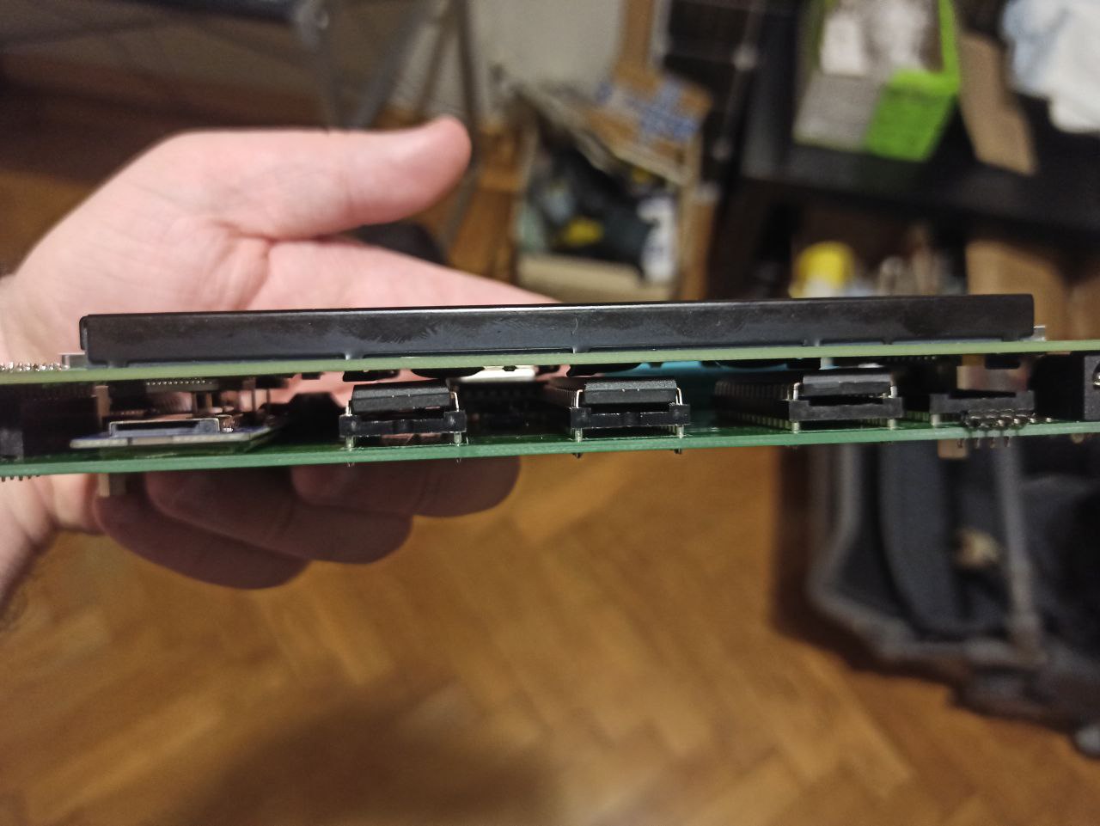
img/v16_it_fits.jpg
