and3rson/deck65/img/v16_mess.jpg

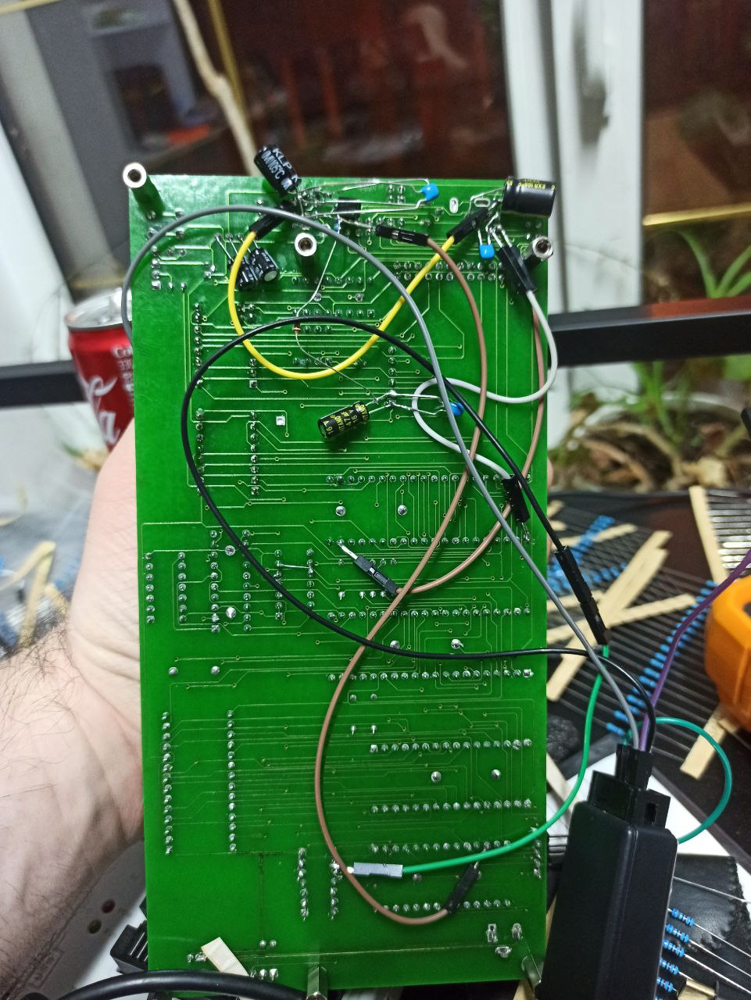
img/v16_mess.jpg
