and3rson/deck65/img/v16_thicc.jpg

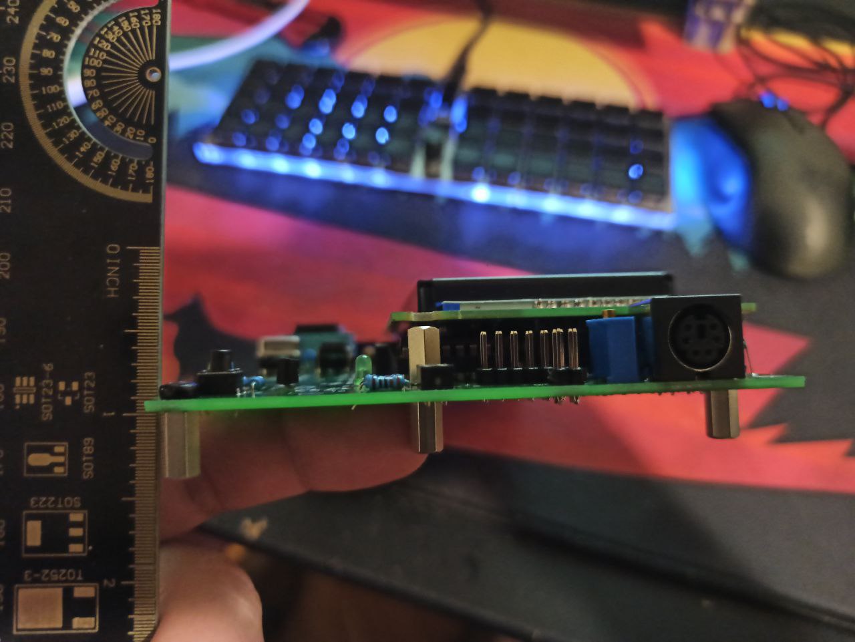
img/v16_thicc.jpg
