and3rson/deck65/img/v17_fs_jumper.jpg

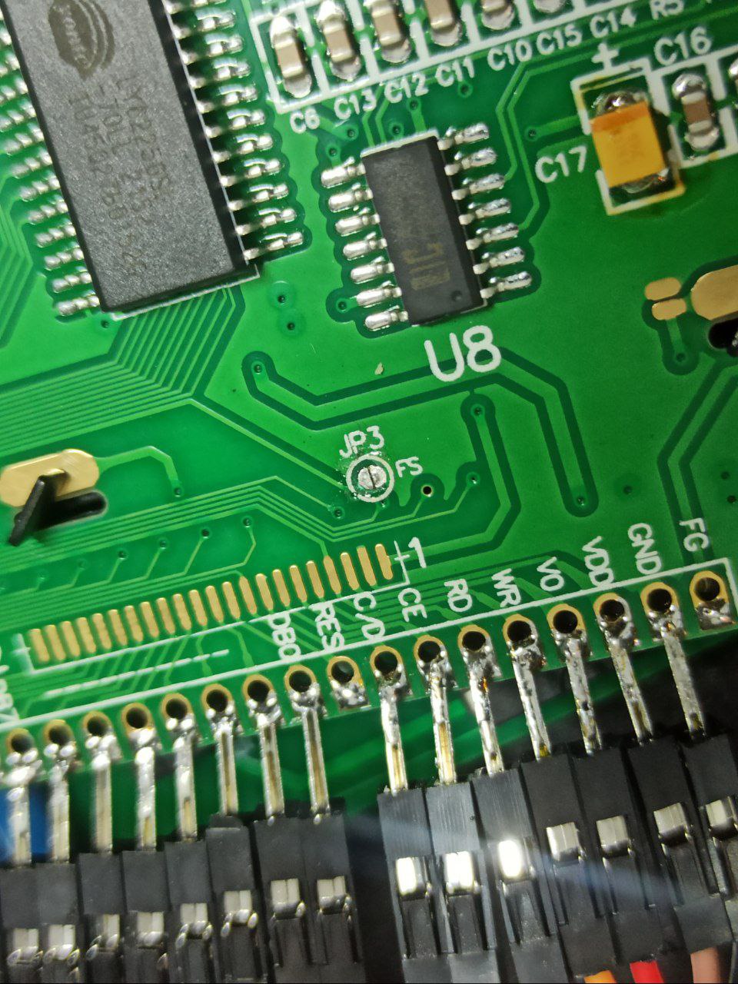
img/v17_fs_jumper.jpg
