and3rson/deck65/img/v17_lcd.jpg

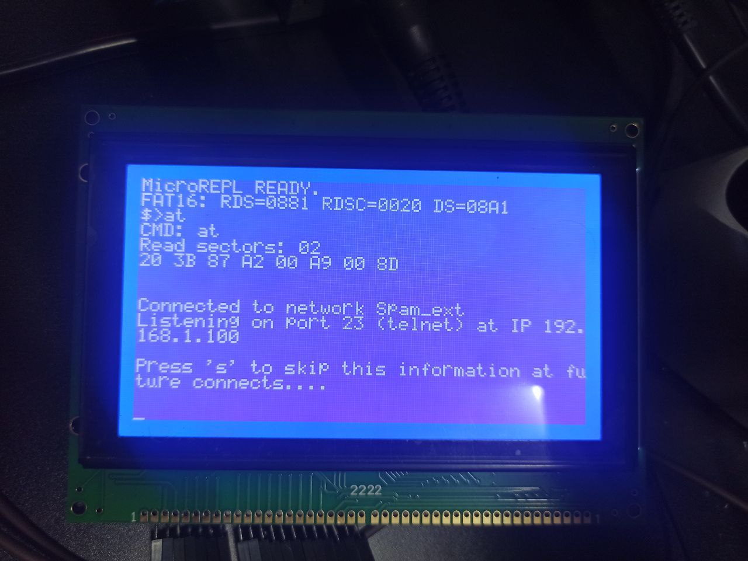
img/v17_lcd.jpg
