and3rson/deck65/img/v17_net.jpg

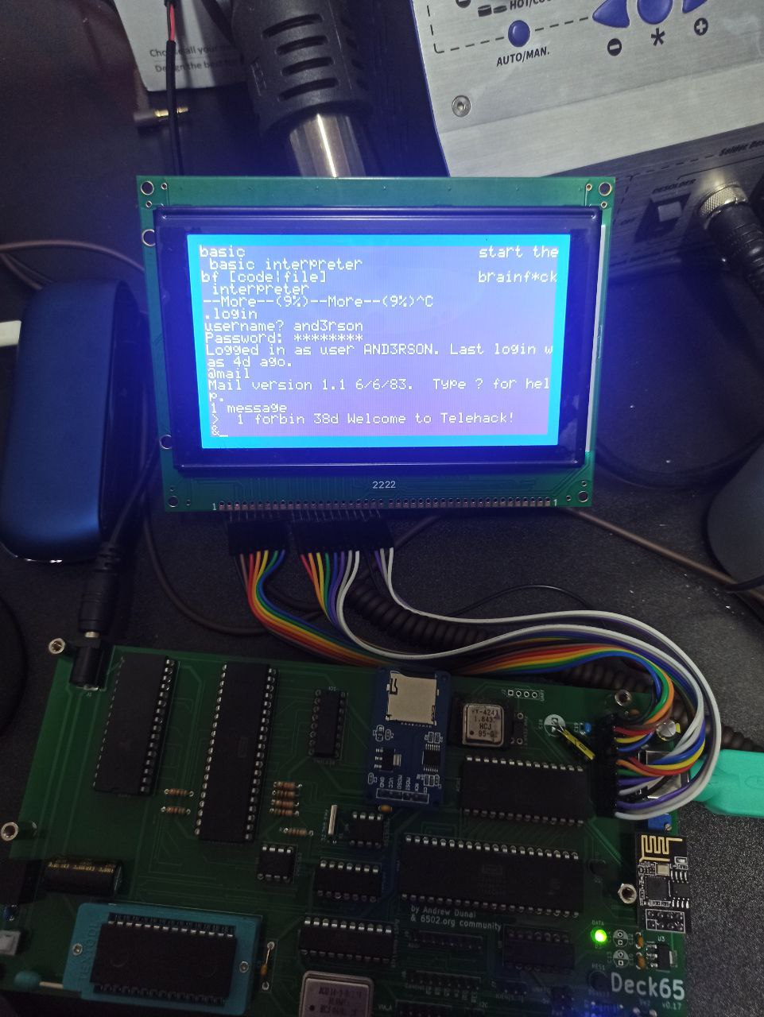
img/v17_net.jpg
