and3rson/deck65/img/v17_routed.png

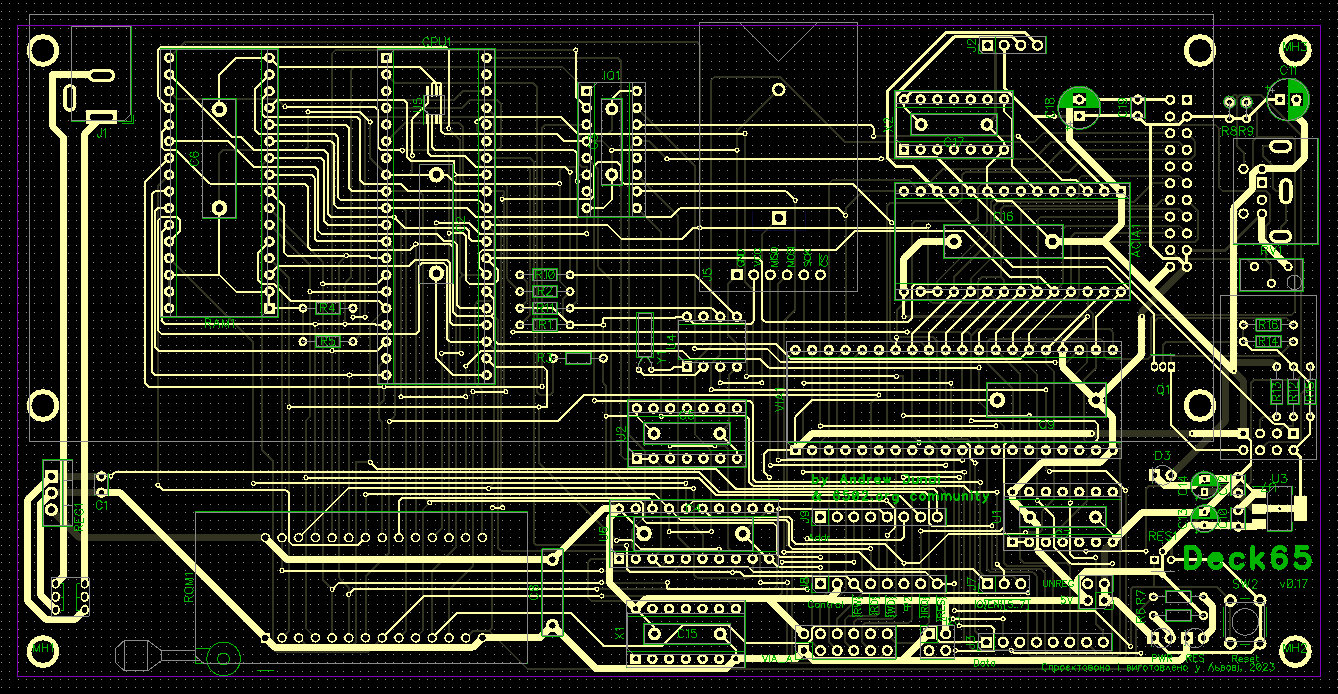
img/v17_routed.png
