and3rson/deck65/img/v17_routed_back.png

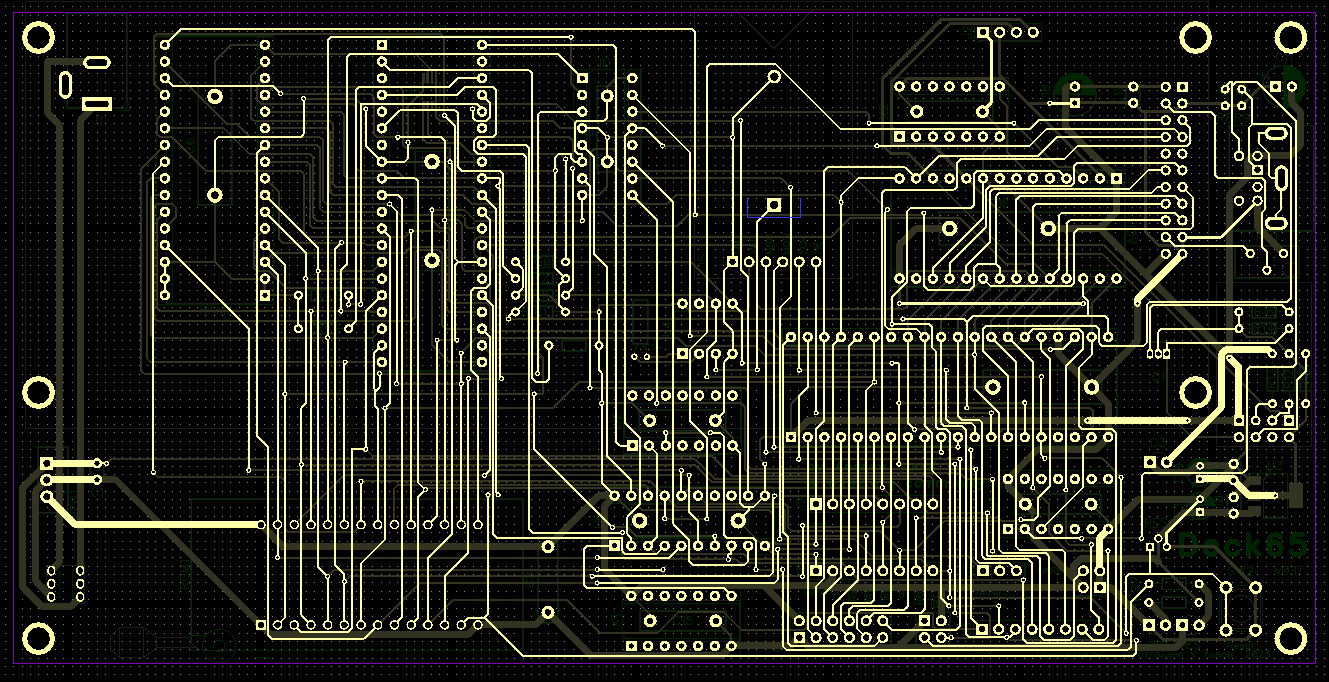
img/v17_routed_back.png
