and3rson/deck65/img/v17_unrouted.png

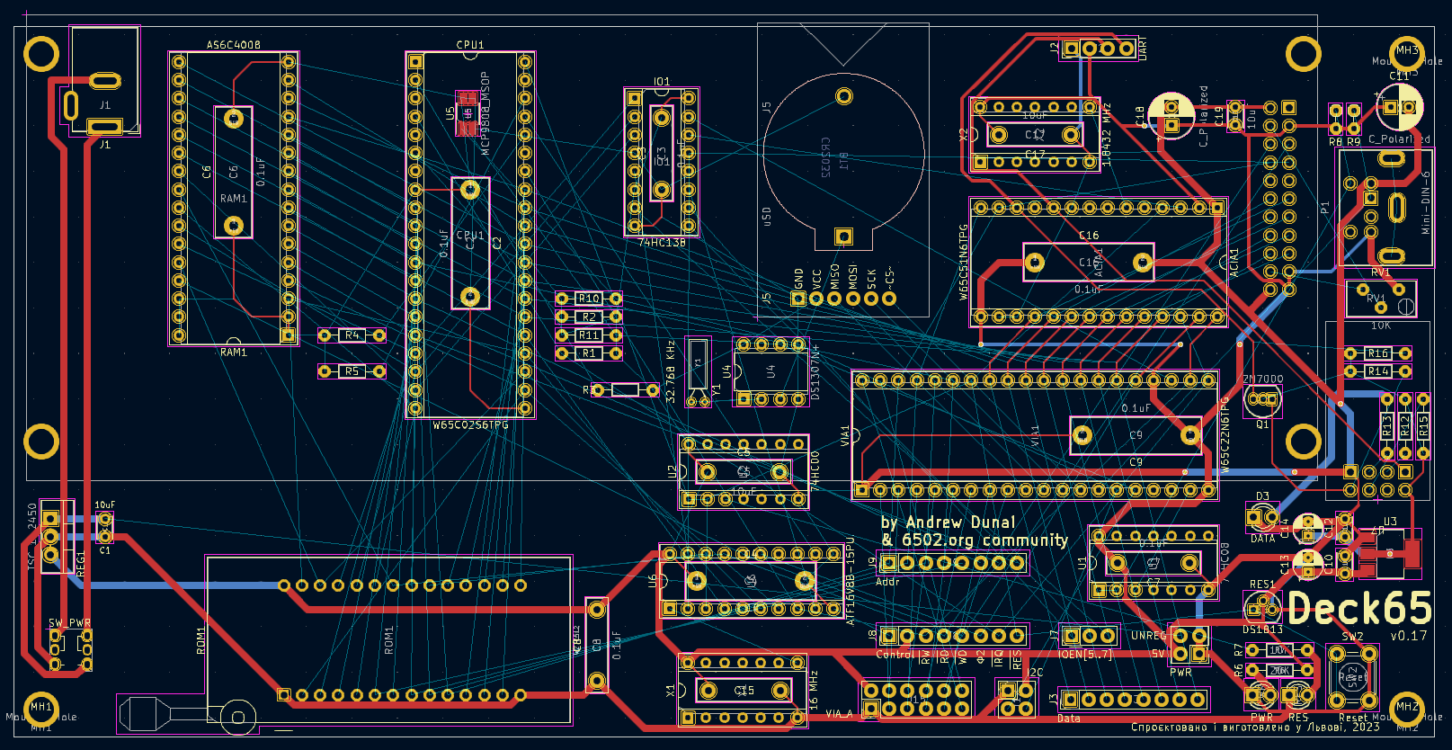
img/v17_unrouted.png
