and3rson/deck65/img/v17b_routed.png

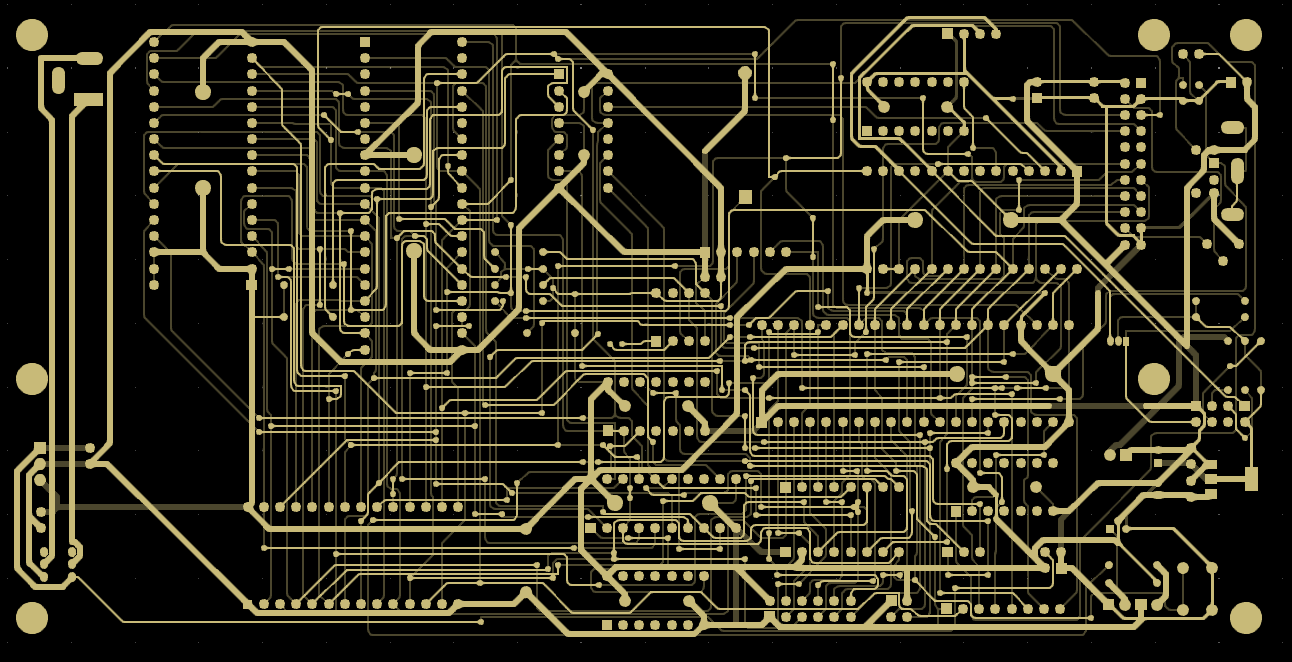
img/v17b_routed.png
