and3rson/deck65/img/v17b_unrouted.png

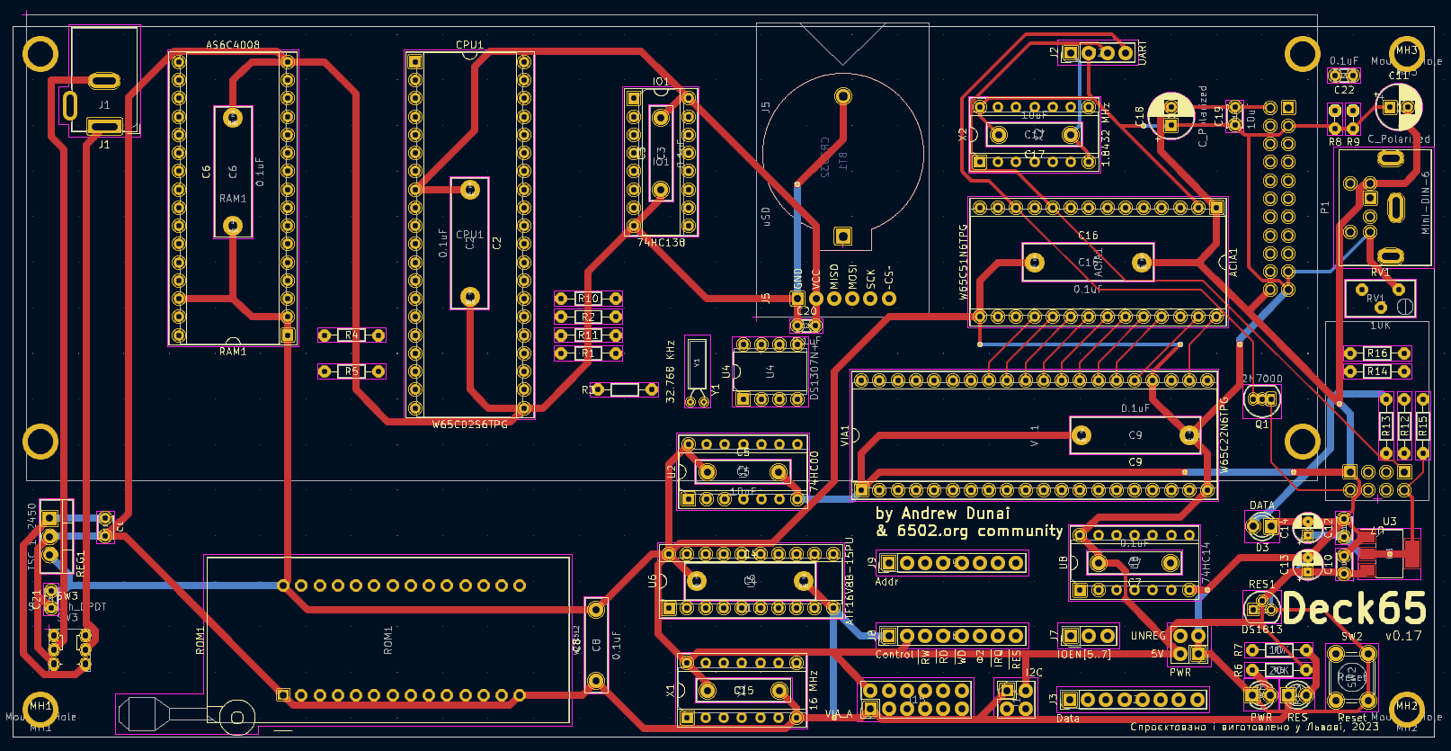
img/v17b_unrouted.png
