and3rson/deck65/img/v17c_routed.png

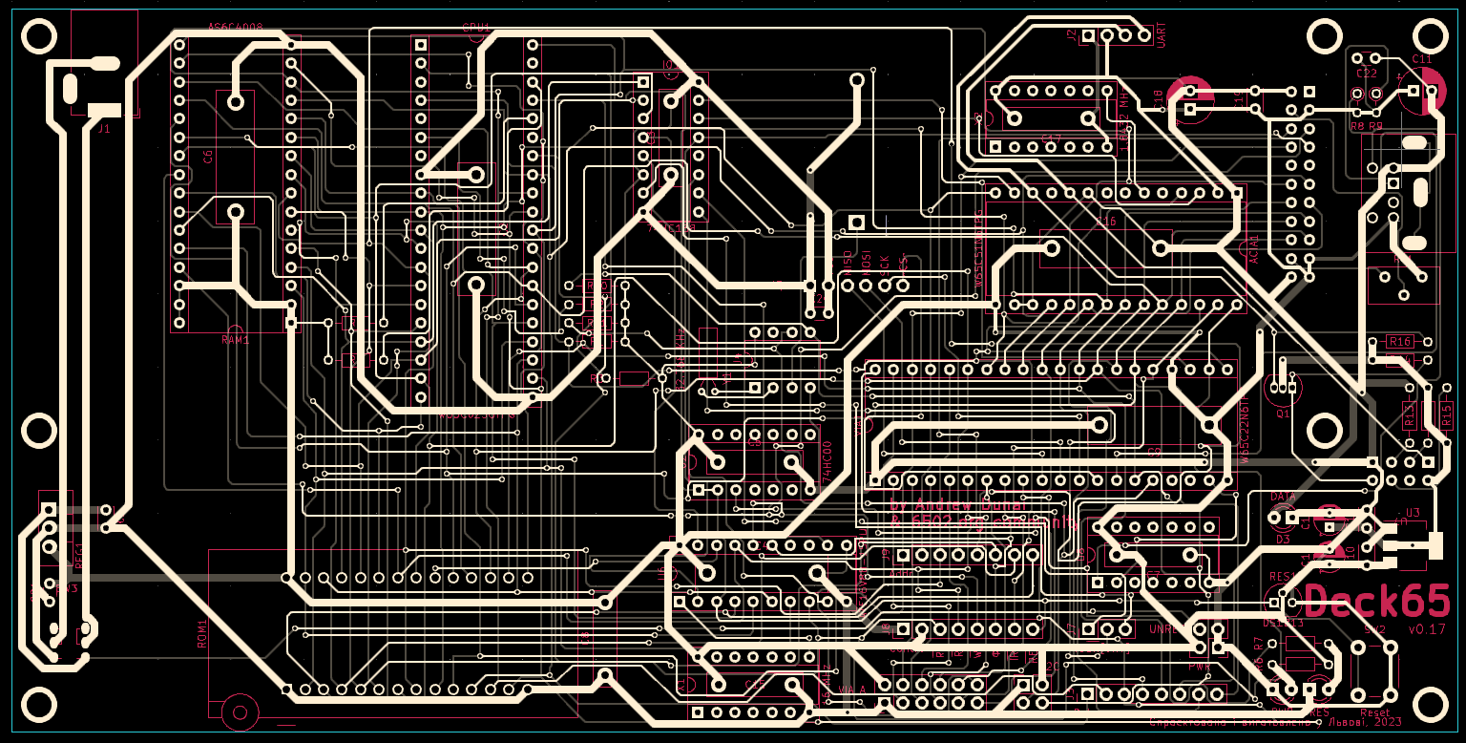
img/v17c_routed.png
