and3rson/deck65/img/zork.jpg

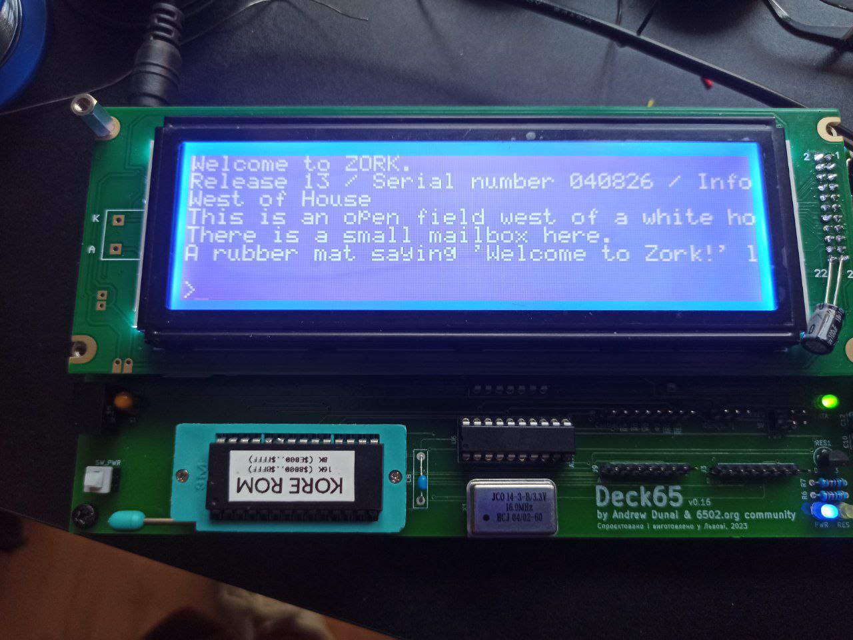
img/zork.jpg
