and3rson/deck65/img/v2_0_assembled1.jpg

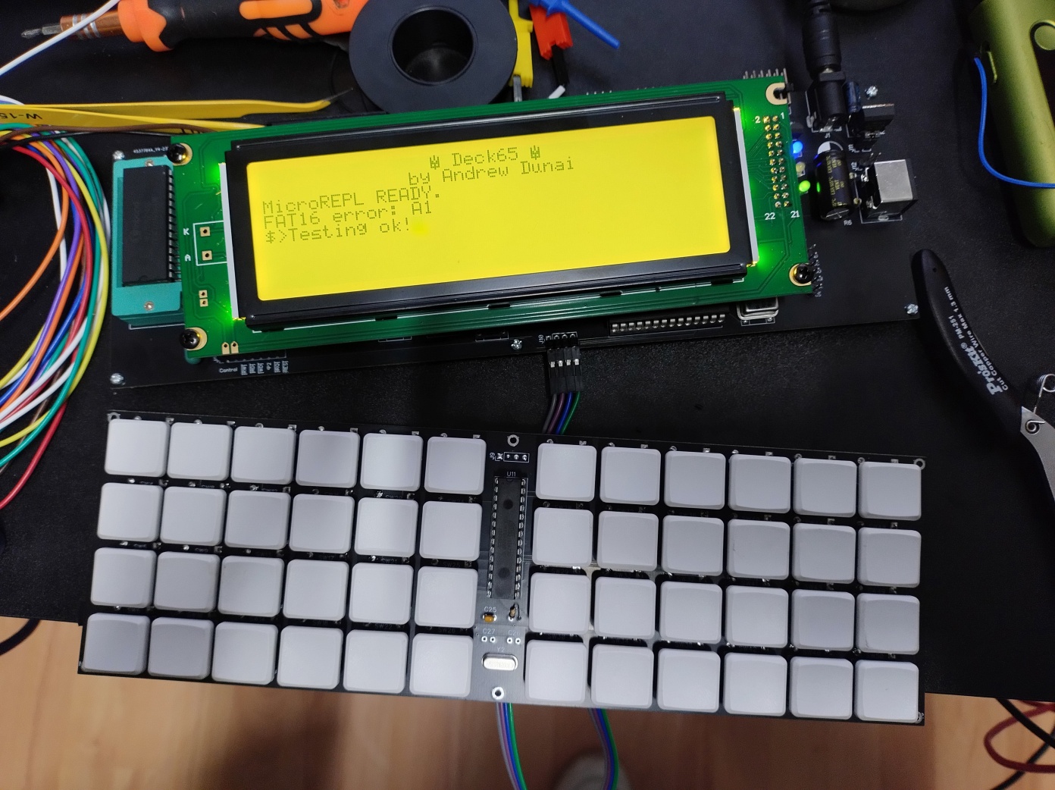
img/v2_0_assembled1.jpg
