and3rson/deck65/img/v09_printed1.jpg

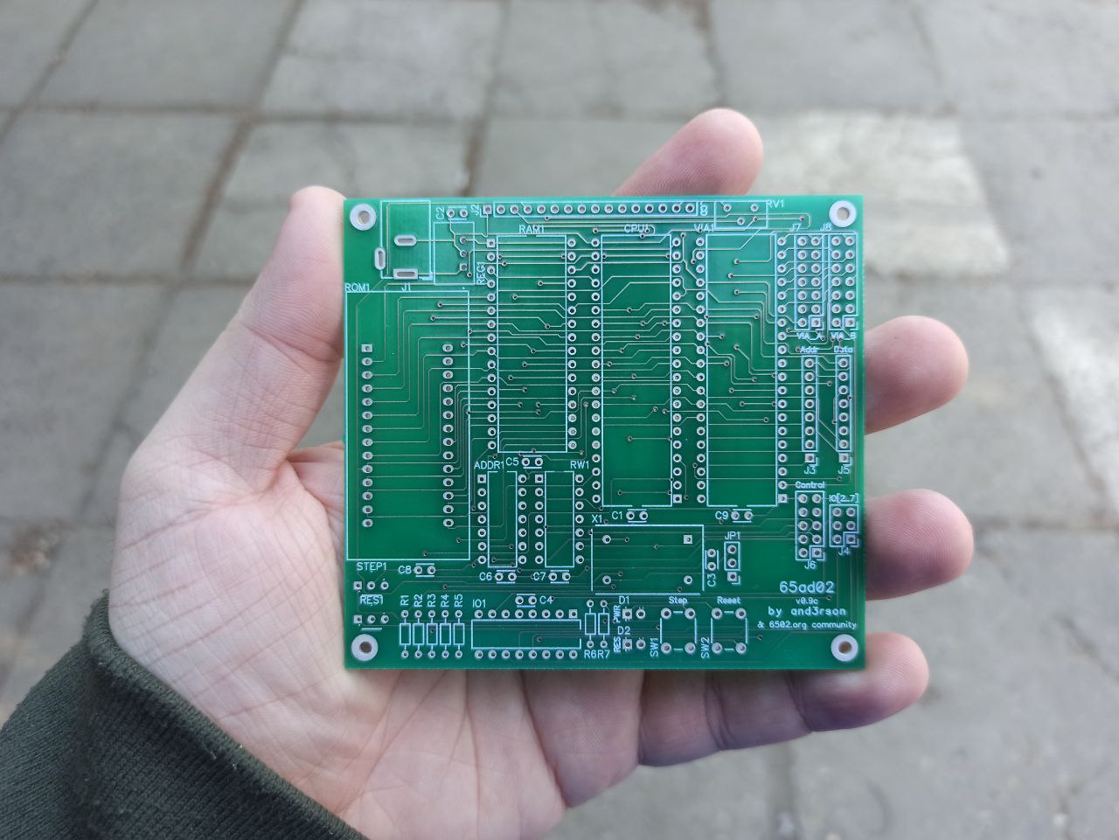
img/v09_printed1.jpg
