and3rson/deck65/img/v09_printed4.jpg

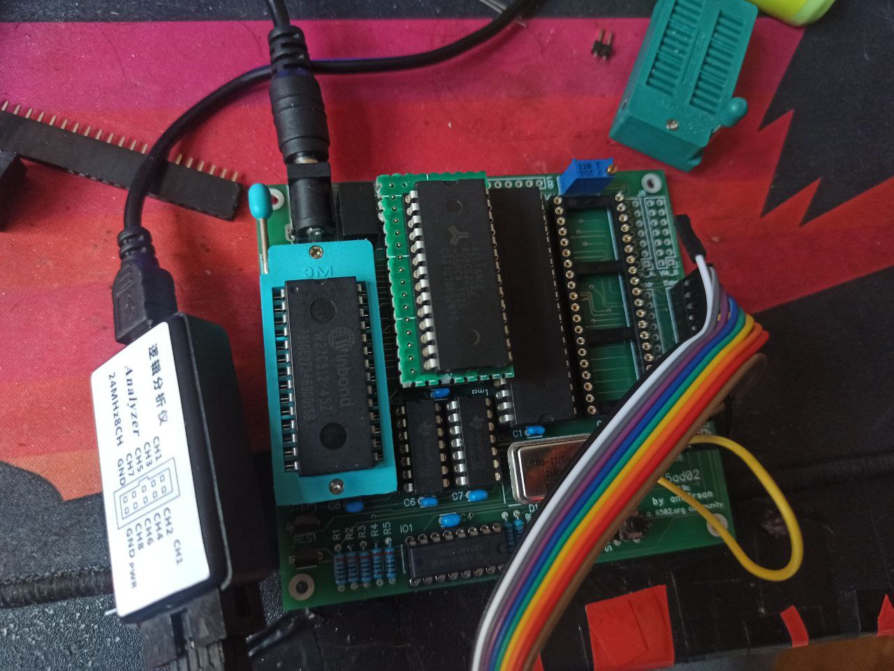
img/v09_printed4.jpg
