and3rson/deck65/img/gal_test_pass.png

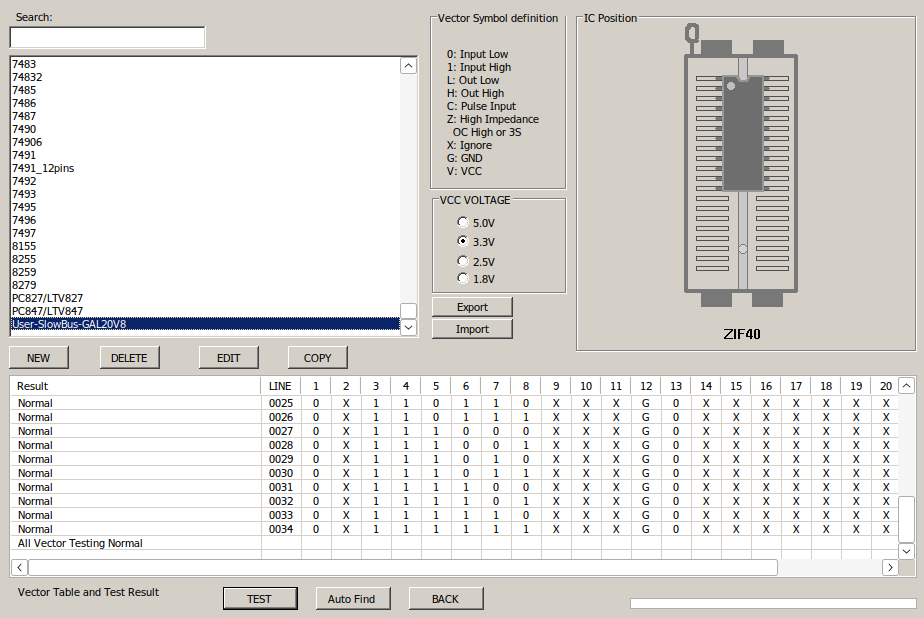
img/gal_test_pass.png
