and3rson/deck65/img/v09_lcd_fix_piggyback.png

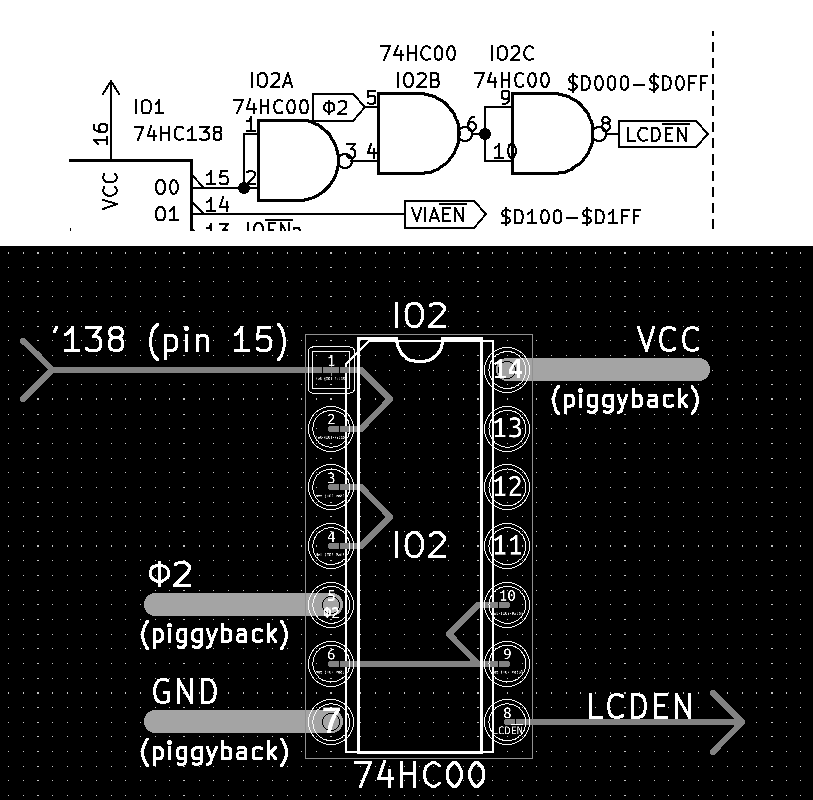
img/v09_lcd_fix_piggyback.png
