and3rson/deck65/keyboard/src/scancodes.h

#define _____       0x00
#define SC_ESC      0x76
#define SC_1        0x16
#define SC_2        0x1E
#define SC_3        0x26
#define SC_4        0x25
#define SC_5        0x2E
#define SC_6        0x36
#define SC_7        0x3D
#define SC_8        0x3E
#define SC_9        0x46
#define SC_0        0x45
#define SC_MINUS    0x4E
#define SC_EQUAL    0x55
#define SC_BKSPC    0x66
#define SC_TAB      0x0D
#define SC_Q        0x15
#define SC_W        0x1D
#define SC_E        0x24
#define SC_R        0x2D
#define SC_T        0x2C
#define SC_Y        0x35
#define SC_U        0x3C
#define SC_I        0x43
#define SC_O        0x44
#define SC_P        0x4D
#define SC_LBRAC    0x54
#define SC_RBRAC    0x5B
#define SC_ENTER    0x5A
#define SC_LCTRL    0x14
#define SC_A        0x1C
#define SC_S        0x1B
#define SC_D        0x23
#define SC_F        0x2B
#define SC_G        0x34
#define SC_H        0x33
#define SC_J        0x3B
#define SC_K        0x42
#define SC_L        0x4B
#define SC_SMCLN    0x4C
#define SC_APSTR    0x52
#define SC_GRAVE    0x0E
#define SC_LSHFT    0x12
#define SC_BKSLH    0x5D
#define SC_Z        0x1A
#define SC_X        0x22
#define SC_C        0x21
#define SC_V        0x2A
#define SC_B        0x32
#define SC_N        0x31
#define SC_M        0x3A
#define SC_COMMA    0x41
#define SC_PRIOD    0x49
#define SC_SLASH    0x4A
#define SC_RSHFT    0x59
#define SC_PTSCR    0x7E
#define SC_LALT     0x11
#define SC_SPACE    0x29
#define SC_CAPS     0x58
#define SC_F1       0x05
#define SC_F2       0x06
#define SC_F3       0x04
#define SC_F4       0x0C
#define SC_F5       0x03
#define SC_F6       0x0B
#define SC_F7       0x83
#define SC_F8       0x0A
#define SC_F9       0x01
#define SC_F10      0x09
#define SC_F11      0x78
#define SC_F12      0x07
#define SC_NUMLK    0x77
#define SC_SCRLK    0x7E
#define SC_NM_MINUS 0x7B
#define SC_NM_PLUS  0x79

#define EC_UP    0xE075
#define EC_PGUP  0xE07D
#define EC_LEFT  0xE06B
#define EC_RIGHT 0xE074
#define EC_HOME  0xE06C
#define EC_END   0xE069
#define EC_DOWN  0xE072
#define EC_PGDN  0xE07A
#define EC_INS   0xE070
#define EC_DEL   0xE071

#define CC_LYR1 0xC1
#define CC_LYR2 0xC2
