and3rson/deck65/sdcard/src/cltest.c

#include <stdio.h>
#include <conio.h>

int main(int argc, char **argv);

void foo(char a, char b) {
    char x = 0;
    gotoxy(10, 2);
    while (a < b) {
        puts("a");
        a++;
    }
    for (x = 0; x < 5; x++) {
        puts("b");
    }
    puts(" done\n");
}

int main(int argc, char **argv) {
    puts("Hello from C!\n");
    foo(2, 5);
    return 0;
}
